asilbalaban/MKYADA/docs/images/1-2x2-wide.png

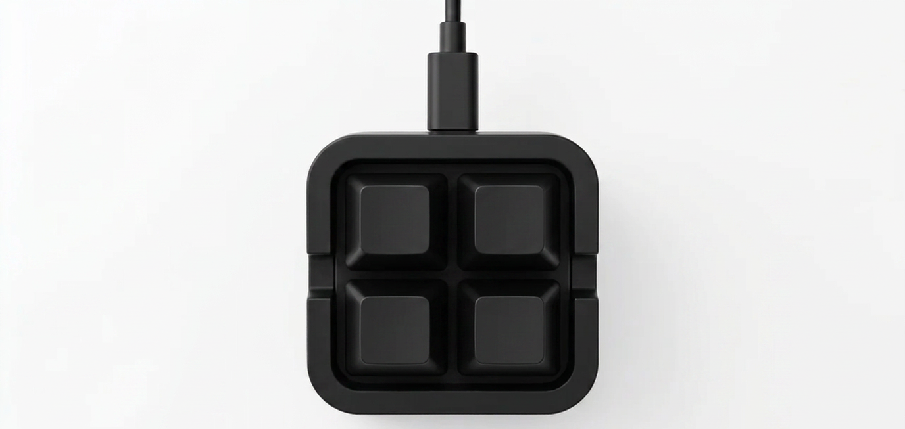
docs/images/1-2x2-wide.png
