asilbalaban/MKYADA/docs/images/2-3x2.png

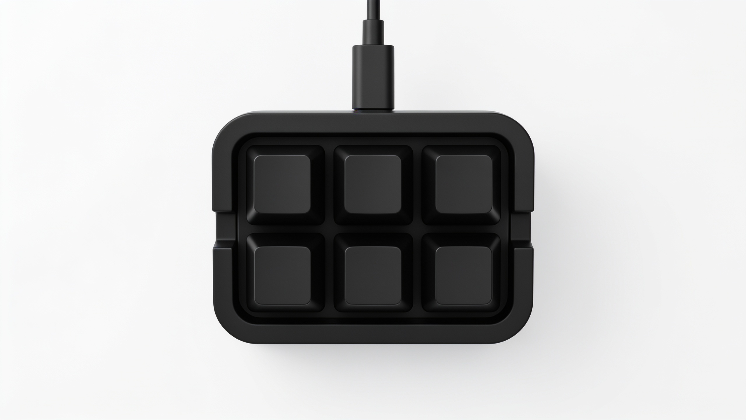
docs/images/2-3x2.png
