asilbalaban/MKYADA/docs/images/3-5x2-wide.png

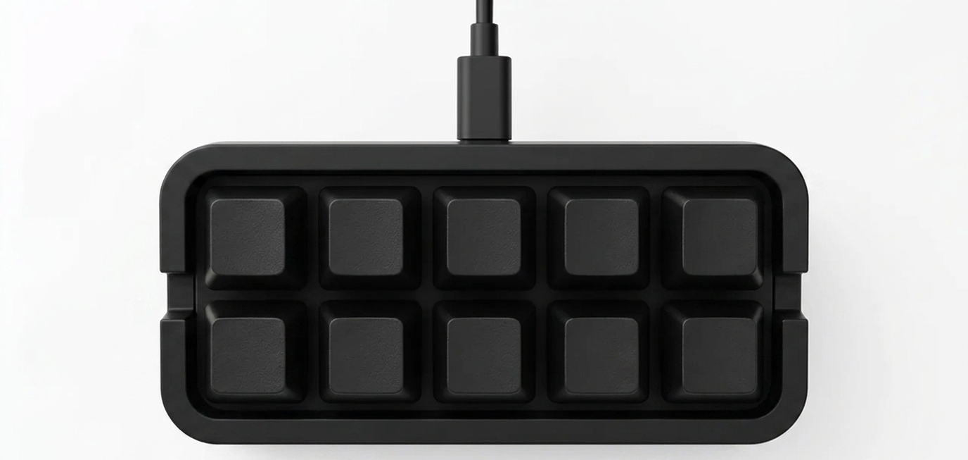
docs/images/3-5x2-wide.png
