asilbalaban/MKYADA/docs/images/3-5x2.png

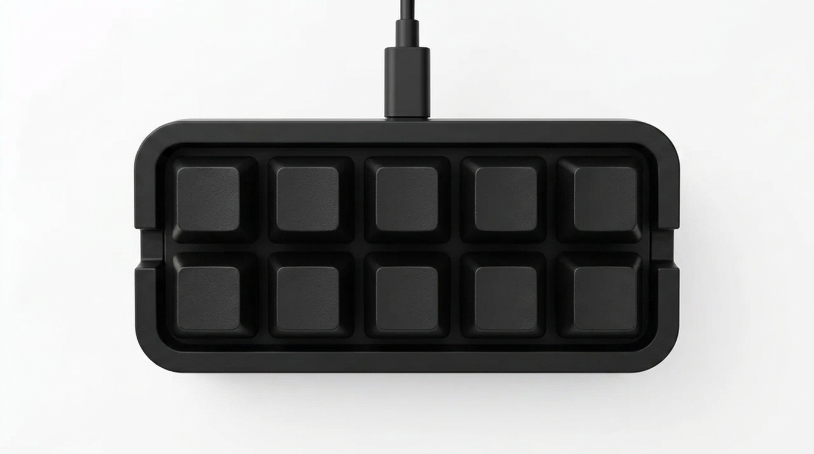
docs/images/3-5x2.png
