asilbalaban/MKYADA/docs/images/4-9x2.png

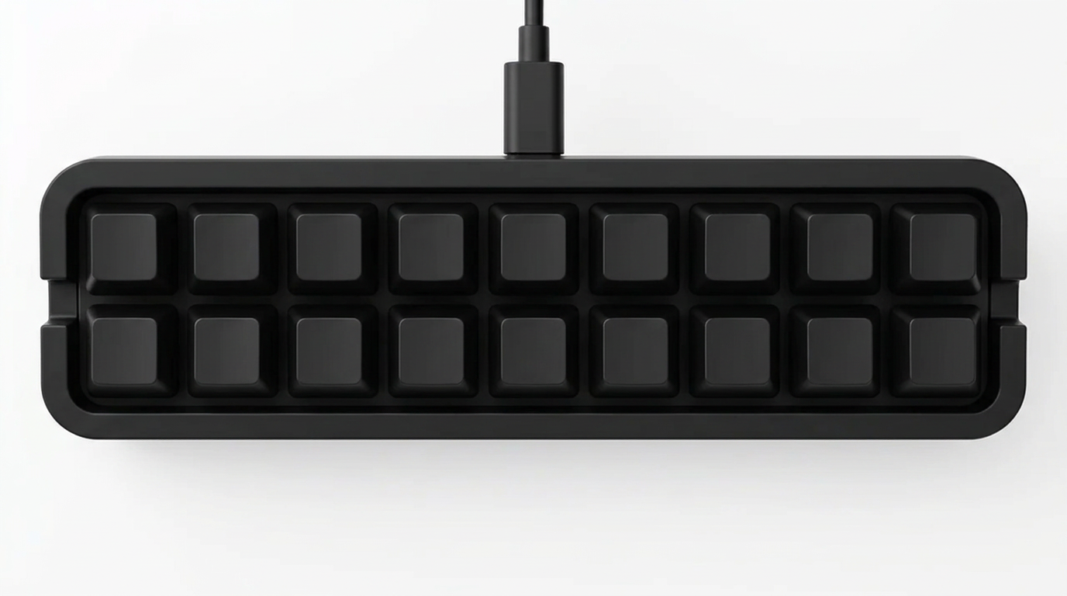
docs/images/4-9x2.png
