asilbalaban/MKYADA/docs/images/5-10x2.png

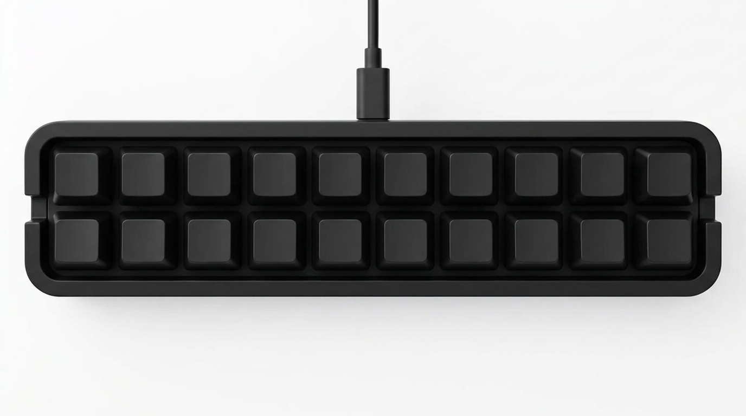
docs/images/5-10x2.png
