asilbalaban/MKYADA/docs/images/mkyada-backview-1800.jpg

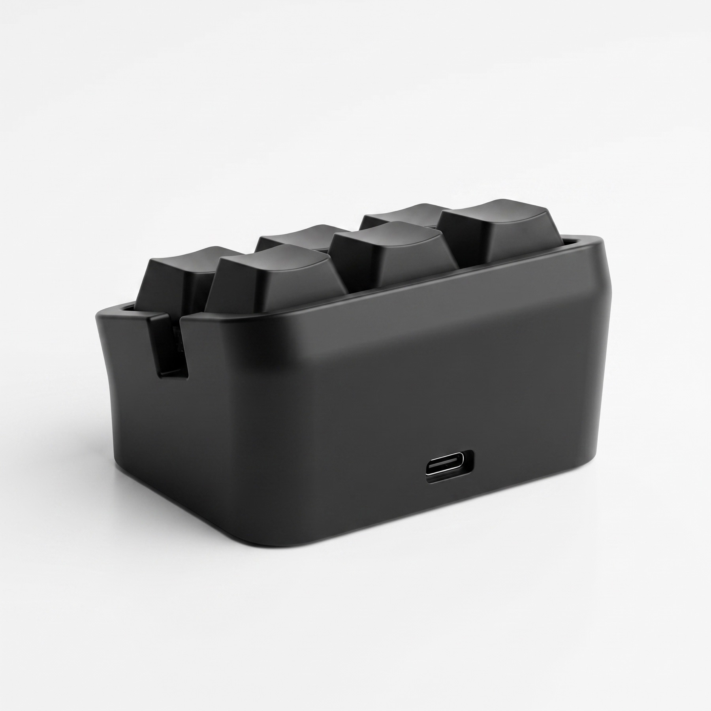
docs/images/mkyada-backview-1800.jpg
