asilbalaban/MKYADA/docs/images/mkyada-backview-cropped.png

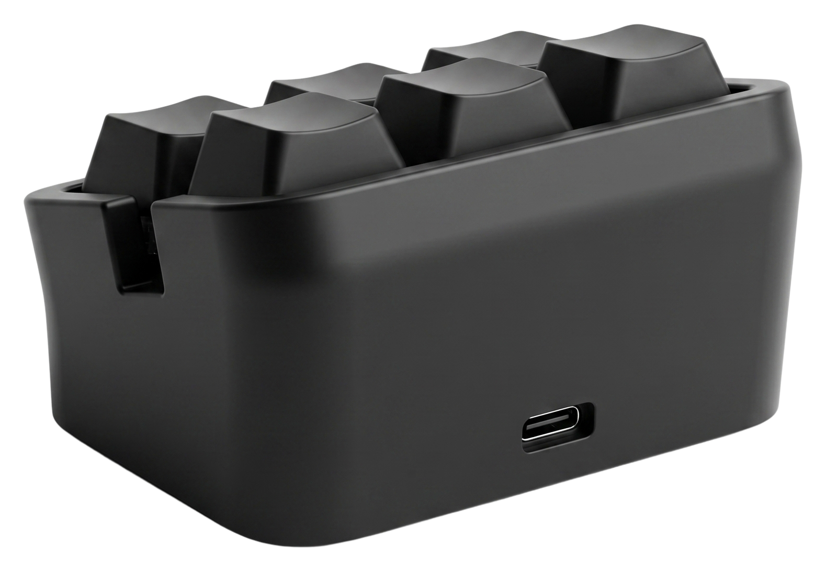
docs/images/mkyada-backview-cropped.png
