asilbalaban/MKYADA/docs/images/mkyada-backview-transparent.png

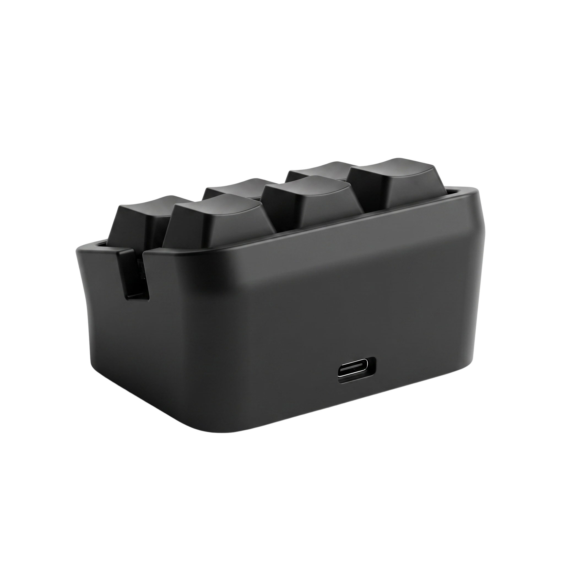
docs/images/mkyada-backview-transparent.png
