asilbalaban/MKYADA/docs/images/mkyada-topview-1800.jpg

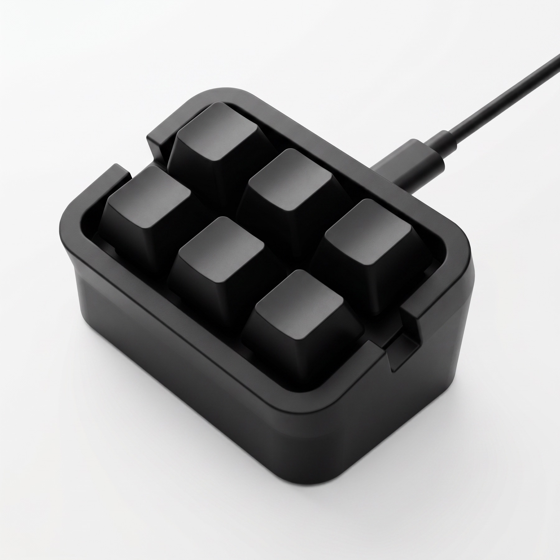
docs/images/mkyada-topview-1800.jpg
