asilbalaban/MKYADA/docs/images/mkyada-topview-cropped.png

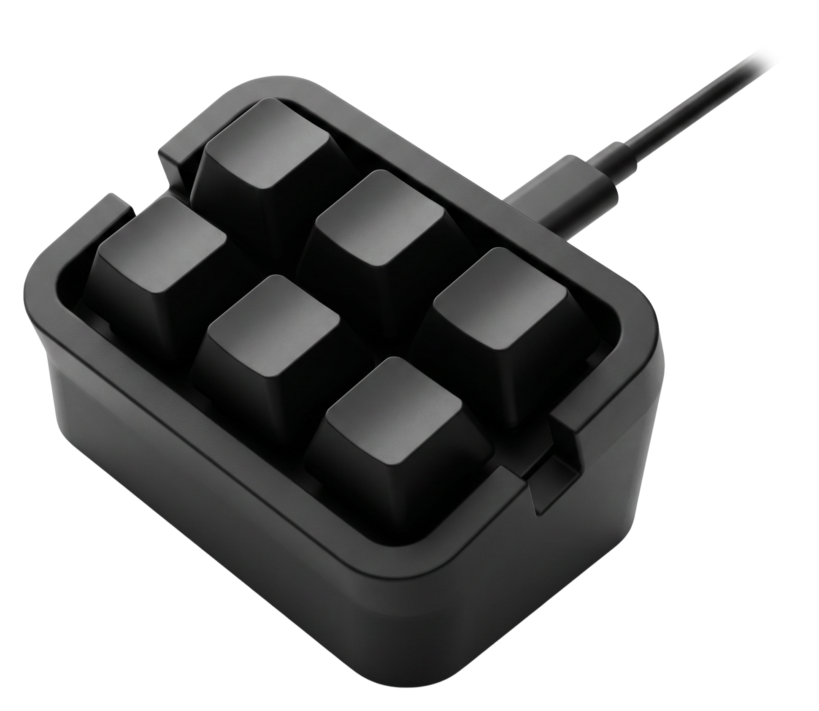
docs/images/mkyada-topview-cropped.png
