asilbalaban/MKYADA/docs/images/mkyada-topview-transparent.png

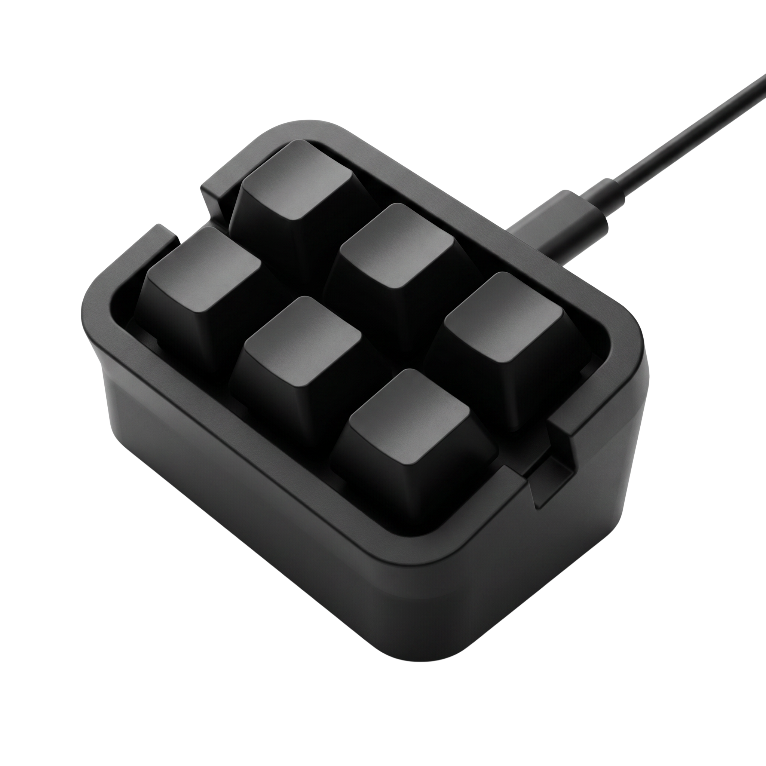
docs/images/mkyada-topview-transparent.png
