asilbalaban/MKYADA/docs/images/screens/core6-control-playing.png

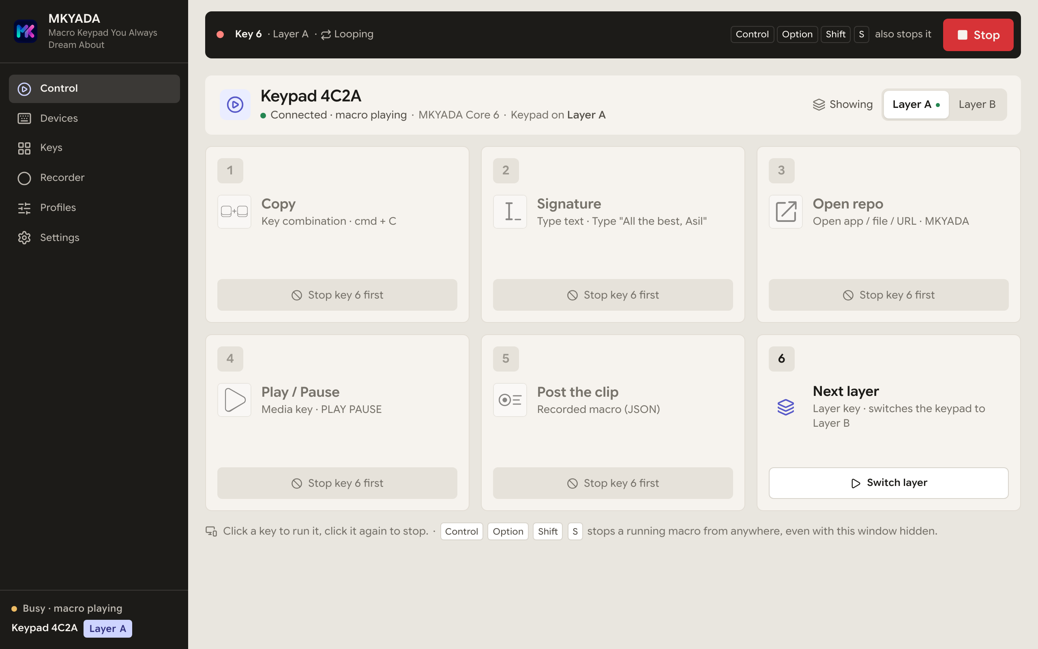
docs/images/screens/core6-control-playing.png
