asilbalaban/MKYADA/docs/images/screens/core6-control.png

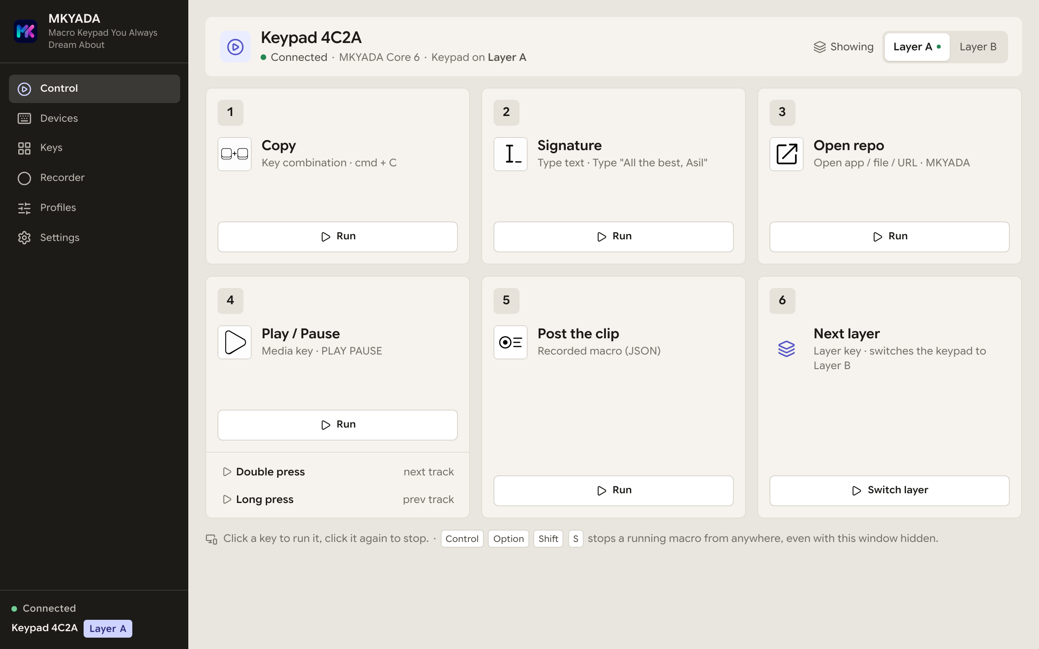
docs/images/screens/core6-control.png
