asilbalaban/MKYADA/docs/images/screens/core6-devices-others.png

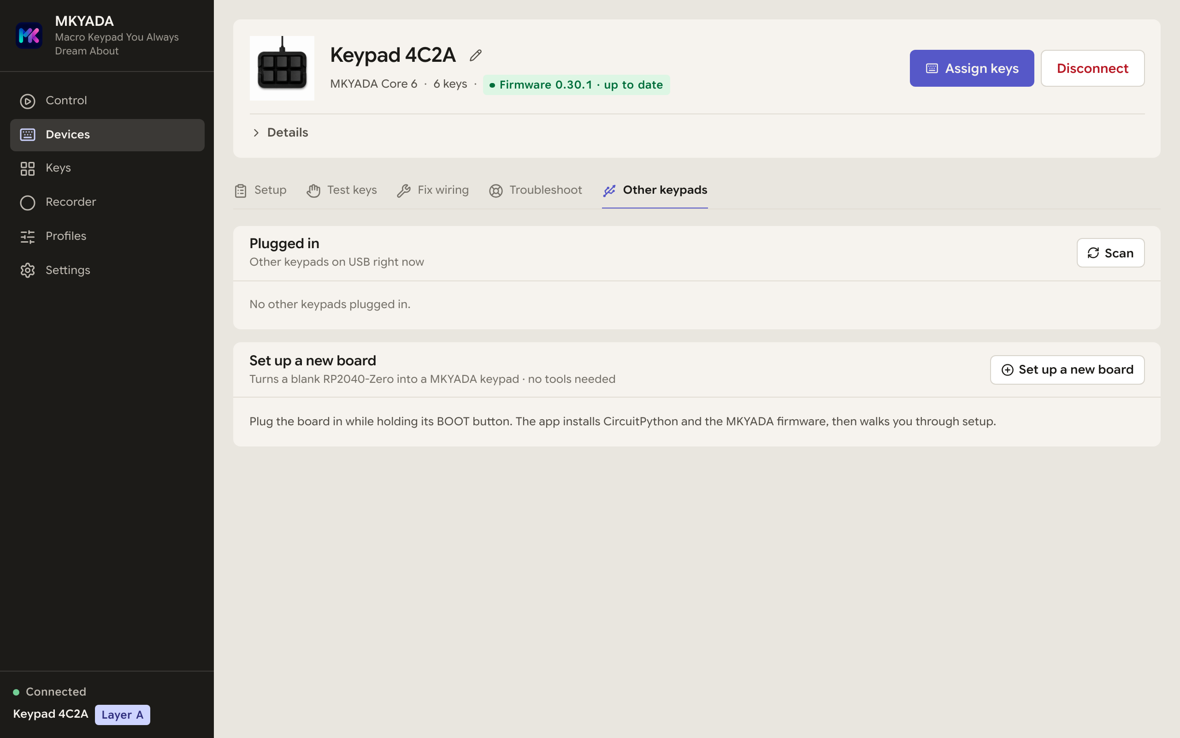
docs/images/screens/core6-devices-others.png
