asilbalaban/MKYADA/docs/images/screens/core6-settings-integrations.png

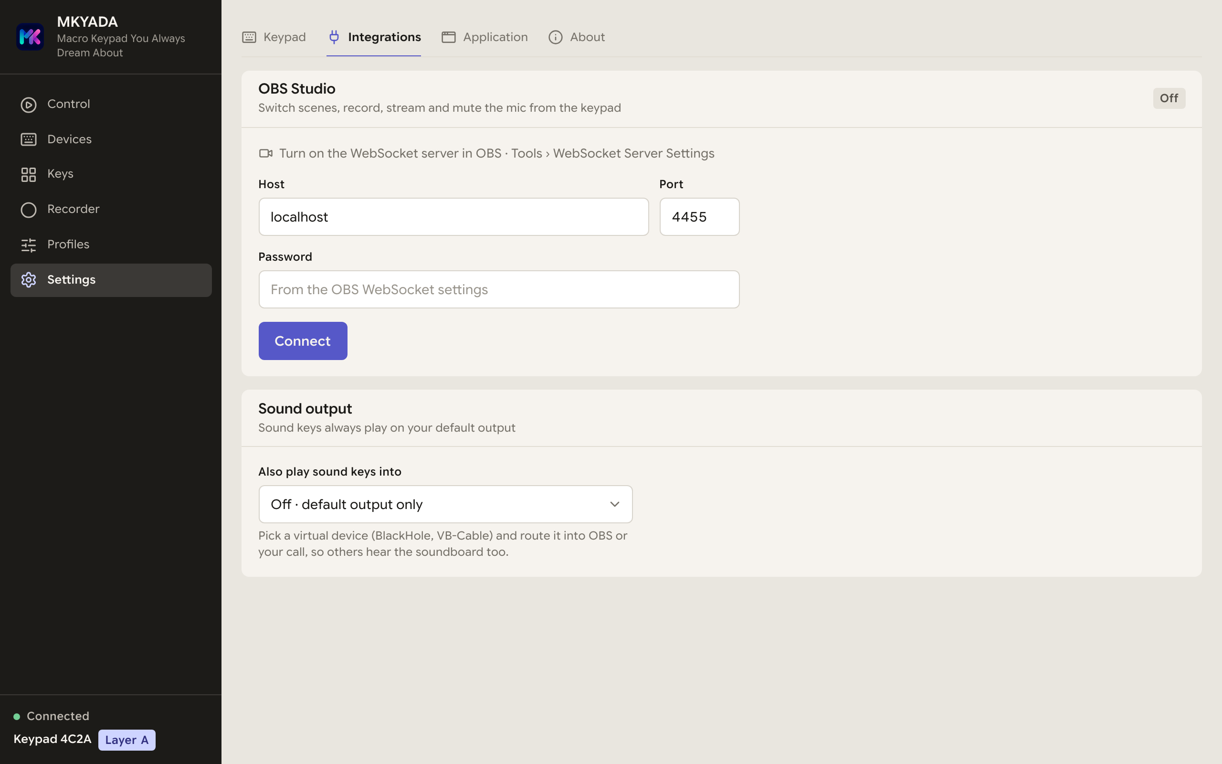
docs/images/screens/core6-settings-integrations.png
