asilbalaban/MKYADA/docs/images/screens/core6-settings.png

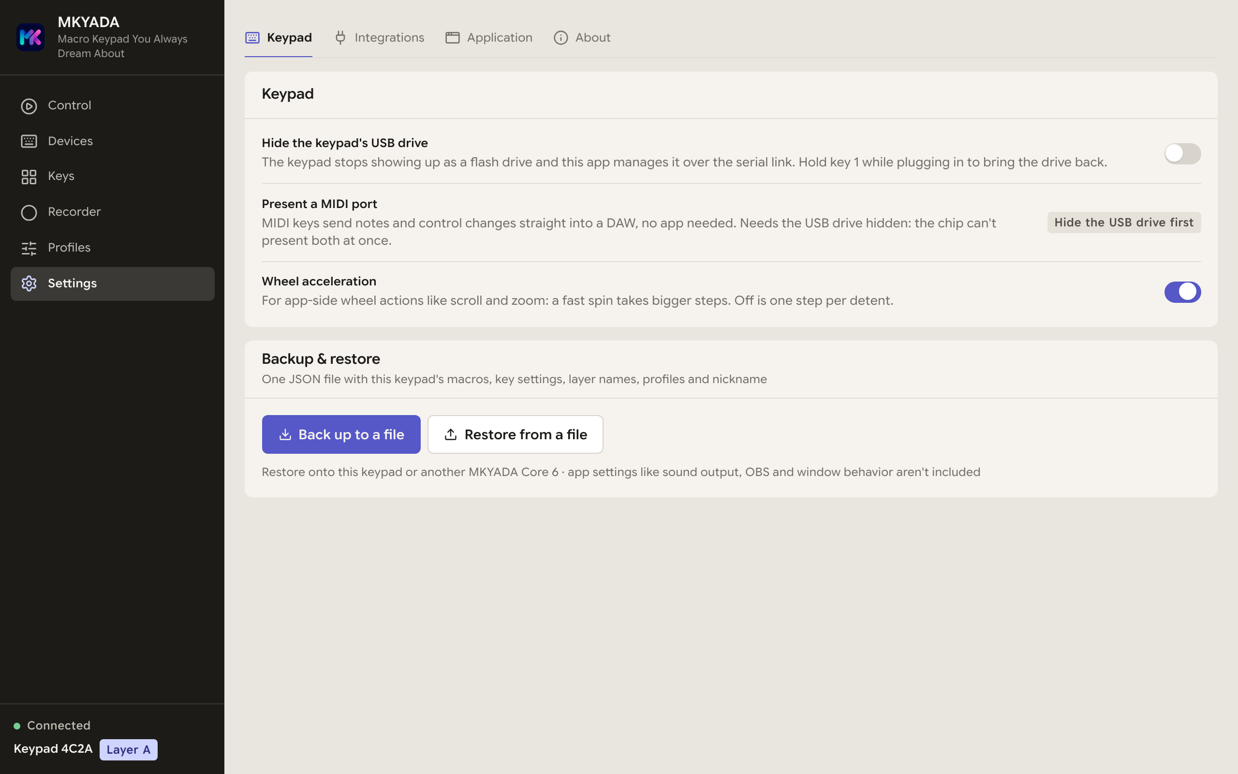
docs/images/screens/core6-settings.png
