asilbalaban/MKYADA/docs/images/screens/core6-wizard.png

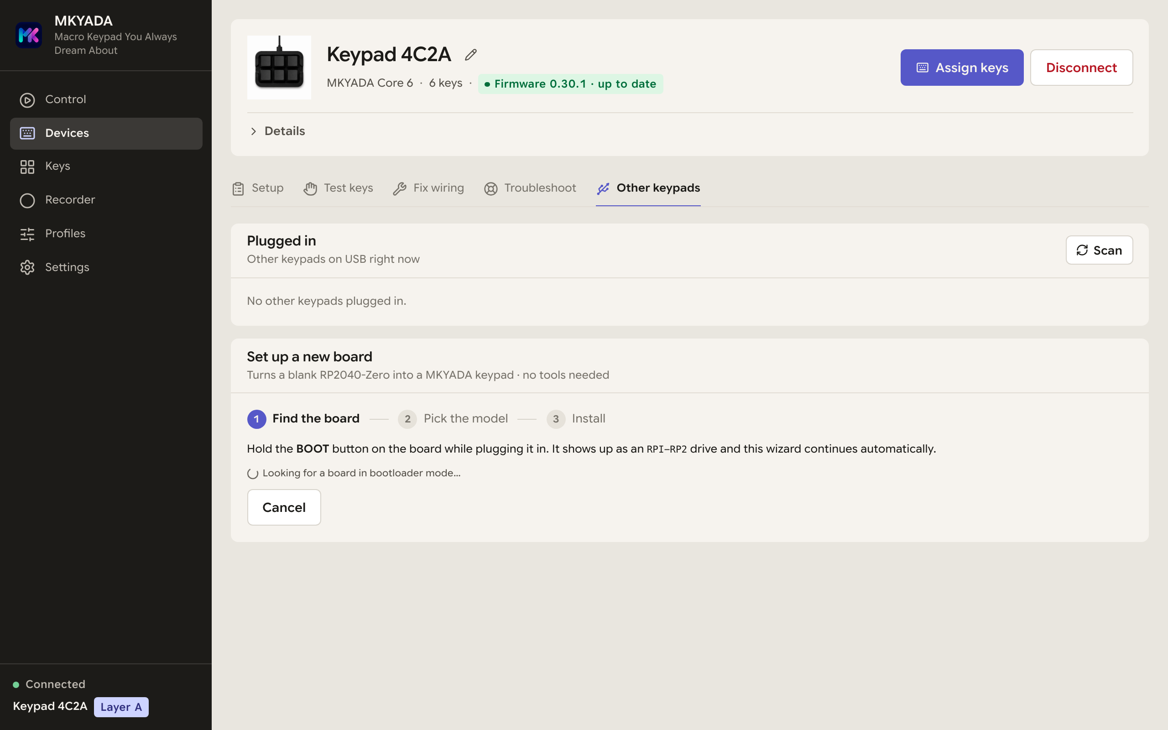
docs/images/screens/core6-wizard.png
