asilbalaban/MKYADA/docs/images/screens/core6-devices-wiring.png

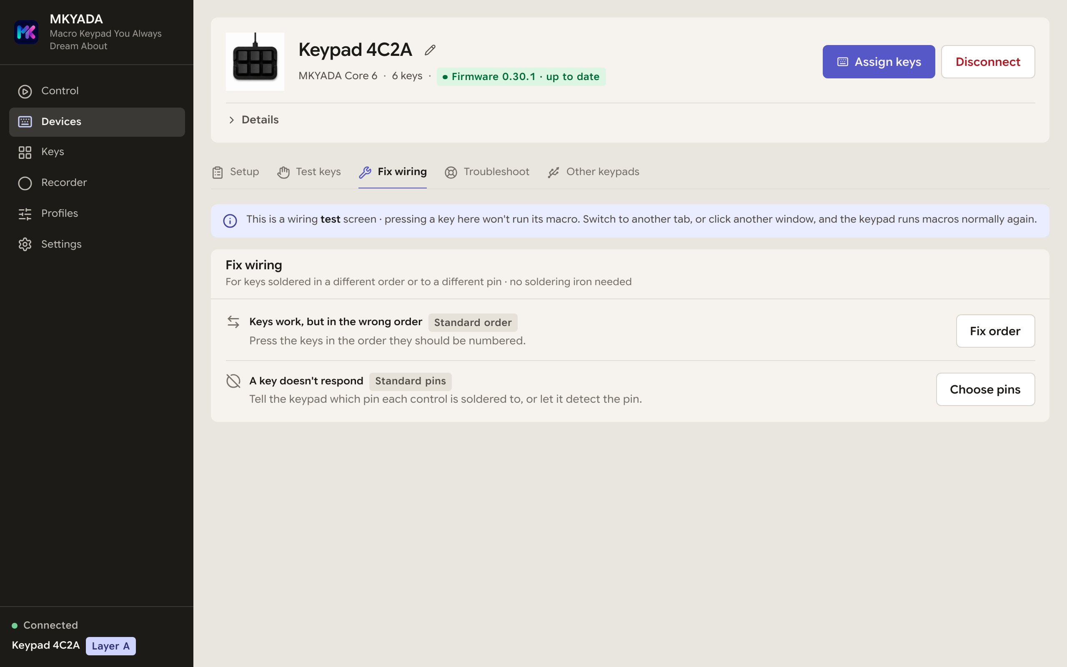
docs/images/screens/core6-devices-wiring.png
