asilbalaban/MKYADA/docs/images/screens/core6-devices-troubleshoot.png

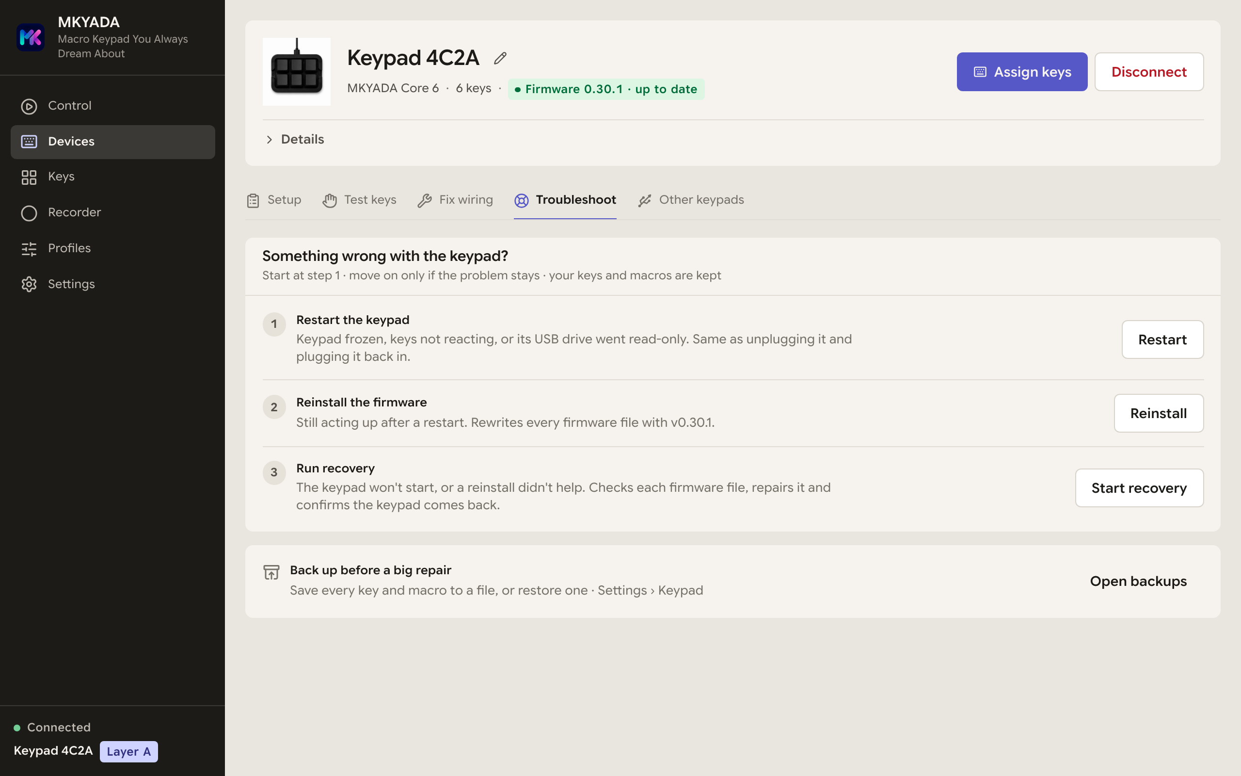
docs/images/screens/core6-devices-troubleshoot.png
