asilbalaban/MKYADA/firmware/mkyada/engine.py

# Macro playback engine: mkyada-macro JSON events -> USB HID reports.
# Port of the proven Raspberry Pi engine (pi/player.py); writes through
# usb_hid.devices instead of /dev/hidg*.

import struct
import time

import usb_hid

from mkyada.hidmap import CONSUMER_USAGE, resolve_key

try:
    from supervisor import ticks_ms
except ImportError:  # desktop simulation
    def ticks_ms():
        return int(time.monotonic() * 1000)

# supervisor.ticks_ms() wraps at 2**29; monotonic-float clocks lose ms
# precision after ~1h uptime, ticks don't.
_TICKS_PERIOD = 1 << 29
_TICKS_HALF = _TICKS_PERIOD // 2


def _ticks_diff(a, b):
    """a - b in ms, correct across the ticks_ms wrap."""
    return ((a - b + _TICKS_HALF) & (_TICKS_PERIOD - 1)) - _TICKS_HALF


def _find_device(usage_page, usage):
    for dev in usb_hid.devices:
        if dev.usage_page == usage_page and dev.usage == usage:
            return dev
    raise RuntimeError("HID device %02x:%02x not found" % (usage_page, usage))


class StopPlayback(Exception):
    pass


class Engine:
    """Owns the three HID interfaces and plays event streams through them."""

    POLL_MS = 20  # how often should_stop()/tick() run during playback

    def __init__(self):
        self.kbd = _find_device(0x01, 0x06)
        self.mouse = _find_device(0x01, 0x02)
        self.consumer = _find_device(0x0C, 0x01)
        self.mods = 0        # modifier byte
        self.keys = []       # pressed usages (max 6)
        self.buttons = 0     # mouse button byte (abs pointer, id 2)
        self.rel_buttons = 0  # mouse button byte (rel pointer, id 5)
        self.mx = 16384      # last absolute position (0..32767)
        self.my = 16384
        self.sw = 1919       # screen size - 1 for scaling
        self.sh = 1079
        self._last_poll = ticks_ms()
        self._midi_tried = False
        self._midi_port = None
        self._midi_notes = []  # (channel, note) sounding right now

    def set_screen(self, width, height):
        self.sw = max(1, int(width) - 1)
        self.sh = max(1, int(height) - 1)

    # --- keyboard ---
    def _kbd_report(self):
        ks = (self.keys + [0, 0, 0, 0, 0, 0])[:6]
        self.kbd.send_report(bytes([self.mods & 0xFF, 0] + ks))

    def key_down(self, ev):
        r = resolve_key(ev)
        if not r:
            return
        kind, val = r
        if kind == "mod":
            self.mods |= val
        elif val not in self.keys:
            if len(self.keys) < 6:
                self.keys.append(val)
        self._kbd_report()

    def key_up(self, ev):
        r = resolve_key(ev)
        if not r:
            return
        kind, val = r
        if kind == "mod":
            self.mods &= ~val & 0xFF
        elif val in self.keys:
            self.keys.remove(val)
        self._kbd_report()

    # --- mouse ---
    # Three reports on the mouse interface (boot.py ABS_MOUSE_DESCRIPTOR):
    # pointer (id 2) carries buttons + absolute X/Y, scroll (id 4) carries
    # the relative wheel/pan bytes ONLY, rel pointer (id 5) carries its own
    # button state + relative dX/dY. Absolute X/Y in a scroll report would
    # re-assert the last known position and teleport the cursor to wherever
    # the previous macro left it (screen center after boot); the rel report
    # exists so Dial drag slots can nudge the cursor from wherever the USER
    # left it. usb_hid rejects a wrong length, so these packs and boot.py's
    # in_report_lengths must stay in lockstep.
    def _mouse_report(self):
        self.mouse.send_report(struct.pack(
            "<BHH", self.buttons & 0x07, self.mx & 0x7FFF, self.my & 0x7FFF), 2)

    def _wheel_report(self, wheel=0, pan=0):
        self.mouse.send_report(struct.pack("<bb", wheel, pan), 4)

    def move(self, x, y):
        self.mx = max(0, min(32767, int(x * 32767 / self.sw)))
        self.my = max(0, min(32767, int(y * 32767 / self.sh)))
        self._mouse_report()

    def button(self, name, down, x=None, y=None):
        bit = {"left": 0x01, "right": 0x02, "middle": 0x04}.get(name, 0x01)
        if x is not None:
            self.move(x, y)
        if down:
            self.buttons |= bit
        else:
            self.buttons &= ~bit & 0xFF
        self._mouse_report()

    def _rel_report(self, dx=0, dy=0):
        self.mouse.send_report(struct.pack(
            "<Bbb", self.rel_buttons & 0x07,
            max(-127, min(127, int(dx))), max(-127, min(127, int(dy)))), 5)

    def rel_move(self, dx, dy):
        """Nudge the cursor relative to wherever it is now (report id 5).
        The id-2 abs state (mx/my) is deliberately untouched: abs macros
        keep replaying to their recorded positions regardless of nudges."""
        self._rel_report(dx, dy)

    def rel_button(self, name, down):
        bit = {"left": 0x01, "right": 0x02, "middle": 0x04}.get(name, 0x01)
        if down:
            self.rel_buttons |= bit
        else:
            self.rel_buttons &= ~bit & 0xFF
        self._rel_report()

    def hold_mods(self, mod_names):
        """Press modifier keys and KEEP them down (Dial move gestures:
        Ctrl+Opt+drag is Photoshop's brush-size scrub). Returns the modifier
        bits so the caller can drop_mods() exactly what it added."""
        from mkyada.hidmap import MOD_NAME
        added = 0
        for m in mod_names or ():
            added |= MOD_NAME.get(str(m).lower(), 0)
        if added:
            self.mods |= added
            self._kbd_report()
            time.sleep(0.01)  # let the host see the modifiers before the drag
        return added

    def drop_mods(self, bits):
        if bits:
            self.mods &= ~bits & 0xFF
            self._kbd_report()

    SCROLL_MAX_TICKS = 20  # per event/burst; matches the app's amount clamp

    def scroll(self, dy, dx=0):
        """Vertical (dy) and/or horizontal (dx) wheel ticks. Each unit is one
        detent-sized report, sent a few ms apart so hosts register every step
        (a single big report gets coalesced into one notch by some apps).
        The cursor never moves: scroll reports carry no X/Y."""
        vstep = 1 if dy > 0 else -1
        for _ in range(min(abs(int(dy)), self.SCROLL_MAX_TICKS)):
            self._wheel_report(wheel=vstep)
            time.sleep(0.008)
        hstep = 1 if dx > 0 else -1
        for _ in range(min(abs(int(dx)), self.SCROLL_MAX_TICKS)):
            self._wheel_report(pan=hstep)
            time.sleep(0.008)

    def wheel_burst(self, dy=0, dx=0, mod_names=None):
        """One serial-commanded scroll burst ({"t":"scroll"}, proto v6):
        optional modifiers held around the ticks (Ctrl+wheel = zoom). The
        app drives profile wheel slots through this — no file playback, so
        a spin feels like a real wheel, and it decides the acceleration."""
        from mkyada.hidmap import MOD_NAME
        added = 0
        for m in mod_names or ():
            added |= MOD_NAME.get(str(m).lower(), 0)
        if added:
            self.mods |= added
            self._kbd_report()
            time.sleep(0.01)  # let the host see the modifier before the ticks
        try:
            self.scroll(int(dy or 0), int(dx or 0))
        finally:
            if added:
                self.mods &= ~added & 0xFF
                self._kbd_report()

    # --- consumer (media keys) ---
    def consumer_tap(self, usage_name):
        usage = CONSUMER_USAGE.get(usage_name)
        if usage is None:
            return
        self.consumer.send_report(struct.pack("<H", usage))
        time.sleep(0.02)
        self.consumer.send_report(struct.pack("<H", 0))

    # --- MIDI ---
    # Lazy and optional, unlike the HID interfaces: usb_midi may be off at
    # boot (config "midi": false, or boot.py's endpoint budget refused it)
    # and the desktop simulator has no such module at all. A missing port is
    # a silent no-op — _find_device's RuntimeError would be wrong here.
    def _midi(self):
        if not self._midi_tried:
            self._midi_tried = True
            try:
                import usb_midi
                self._midi_port = usb_midi.ports[1]
            except (ImportError, IndexError, AttributeError):
                self._midi_port = None
        return self._midi_port

    def midi_send(self, msg, ch=0, d1=0, d2=0):
        """One MIDI message out. `msg` is note_on / note_off / cc / pc;
        d1 and d2 are note+velocity, controller+value, or program (d2
        unused). Held notes are tracked so release_all can silence them."""
        port = self._midi()
        if port is None:
            return
        ch = int(ch) & 0x0F
        d1 = int(d1) & 0x7F
        d2 = int(d2) & 0x7F
        if msg == "note_on":
            port.write(bytes([0x90 | ch, d1, d2]))
            if (ch, d1) not in self._midi_notes:
                self._midi_notes.append((ch, d1))
        elif msg == "note_off":
            port.write(bytes([0x80 | ch, d1, 0]))
            if (ch, d1) in self._midi_notes:
                self._midi_notes.remove((ch, d1))
        elif msg == "cc":
            port.write(bytes([0xB0 | ch, d1, d2]))
        elif msg == "pc":
            port.write(bytes([0xC0 | ch, d1]))

    def release_all(self):
        self.mods = 0
        self.keys = []
        self._kbd_report()
        # A macro stopped mid-note must not leave the DAW sounding — the
        # same contract as the key-up above, and the reason a note_on is
        # tracked at all.
        if self._midi_notes:
            held, self._midi_notes = self._midi_notes, []
            port = self._midi()
            if port is not None:
                for ch, note in held:
                    port.write(bytes([0x80 | ch, note, 0]))
        # Only touch the mouse when there is a button to release: the pointer
        # report is absolute, so sending it "just in case" teleports the
        # cursor to the last macro position (screen center after boot) even
        # for keyboard-only macros.
        if self.buttons:
            self.buttons = 0
            self._mouse_report()
        # Same rule for the rel pointer: only report when a drag is actually
        # held, and a zero-delta release leaves the cursor where it is.
        if self.rel_buttons:
            self.rel_buttons = 0
            self._rel_report()

    # --- direct combo (serial "keys" command / tiny bindings) ---
    def tap_combo(self, mod_names, key_label, hold_ms=30):
        from mkyada.hidmap import MOD_NAME
        for m in mod_names or ():
            self.mods |= MOD_NAME.get(str(m).lower(), 0)
        self._kbd_report()
        self.key_down({"key": key_label})
        time.sleep(hold_ms / 1000)
        self.key_up({"key": key_label})
        self.mods = 0
        self._kbd_report()

    # --- playback ---
    def _poll(self, should_stop, tick):
        self._last_poll = ticks_ms()
        if should_stop and should_stop():
            raise StopPlayback()
        if tick:
            tick()

    def _wait_until(self, start, due_ms, should_stop, tick):
        """Wait until `due_ms` after `start` (absolute deadline, so per-event
        overhead is absorbed instead of accumulating across the macro)."""
        while True:
            now = ticks_ms()
            if _ticks_diff(now, self._last_poll) >= self.POLL_MS:
                self._poll(should_stop, tick)
                now = ticks_ms()
            remaining = due_ms - _ticks_diff(now, start)
            if remaining <= 0:
                return
            # short slices keep the deadline sharp; host HID polling
            # quantizes to >=1ms anyway, so no busy-spin needed
            time.sleep(0.004 if remaining > 4 else remaining / 1000.0)

    def play(self, events, screen=None, speed=1.0, should_stop=None, tick=None):
        """Play one pass over an iterable of events. Raises StopPlayback on abort."""
        if screen:
            self.set_screen(screen.get("width", 1920), screen.get("height", 1080))
        speed = max(0.01, speed)
        self.release_all()
        start = ticks_ms()
        due = 0.0  # ms since start; float so speed scaling stays exact
        try:
            # poll once per pass so even an all-zero-delay macro (where no
            # wait ever goes stale) still honors stop/restart/switch presses
            self._poll(should_stop, tick)
            for ev in events:
                due += ev.get("delay", 0) / speed
                self._wait_until(start, due, should_stop, tick)
                t = ev.get("type")
                if t == "key":
                    (self.key_down if ev.get("action") == "down" else self.key_up)(ev)
                elif t == "move":
                    self.move(ev.get("x", 0), ev.get("y", 0))
                elif t == "button":
                    self.button(ev.get("button", "left"), ev.get("action") == "down",
                                ev.get("x"), ev.get("y"))
                elif t == "scroll":
                    self.scroll(ev.get("dy", 0), ev.get("dx", 0))
                elif t == "consumer":
                    self.consumer_tap(ev.get("usage", ""))
                elif t == "midi":
                    self.midi_send(ev.get("m", ""), ev.get("ch", 0),
                                   ev.get("d1", 0), ev.get("d2", 0))
                # "wait" and unknown types: delay already applied above
        finally:
            self.release_all()
