asilbalaban/MKYADA/firmware/mkyada/led.py

# Status LED on the RP2040-Zero's onboard WS2812 (GP16).
#
#   idle        layer color, dim solid (A green / B blue / C purple / D teal)
#   playing     amber fast blink; looping macro -> slow amber blink
#   host mode   layer color breathing toward white
#   error       red triple-blink overlay, then back to current state
#   override    app-commanded feedback color (serial "led" op, e.g. mic muted
#               -> solid red). Shown when idle/host; playback blinks win.
#               Cleared when the app disconnects, so the standalone LED
#               grammar is untouched without a host.

import time

import board

try:
    import neopixel
except ImportError:
    neopixel = None  # lib missing: run without a status LED

# A-D unchanged from the original 4-layer palette; E-H added for the
# 8-layer cap (amber is reserved for "playing", red for errors).
LAYER_COLORS = ((0, 255, 0), (0, 80, 255), (170, 0, 255), (0, 255, 180),
                (255, 255, 255), (255, 0, 150), (160, 255, 0), (255, 200, 0))
AMBER = (255, 120, 0)
RED = (255, 0, 0)

IDLE, PLAYING, LOOPING, HOST = 0, 1, 2, 3


class Led:
    def __init__(self):
        try:
            self.px = neopixel.NeoPixel(board.GP16, 1, brightness=0.15, auto_write=True) if neopixel else None
        except Exception:
            self.px = None
        self.state = IDLE
        self.layer = 0
        self.error_until = 0
        self.override = None  # ("solid"|"blink", (r, g, b)) from the app
        self._apply()

    def _color(self):
        return LAYER_COLORS[self.layer % len(LAYER_COLORS)]

    def _apply(self, color=None):
        if self.px:
            try:
                self.px[0] = color or self._color()
            except Exception:
                pass

    def set(self, state=None, layer=None):
        if state is not None:
            self.state = state
        if layer is not None:
            self.layer = layer
        self._apply(AMBER if self.state in (PLAYING, LOOPING) else None)

    def error(self):
        self.error_until = time.monotonic() + 1.2

    def set_override(self, mode, rgb):
        """App-commanded feedback color; mode "off" clears it."""
        if mode not in ("solid", "blink") or not rgb:
            self.override = None
        else:
            try:
                self.override = (mode, (int(rgb[0]), int(rgb[1]), int(rgb[2])))
            except (TypeError, ValueError, IndexError):
                self.override = None
        self._apply()

    def clear_override(self):
        self.override = None
        self._apply()

    def tick(self):
        """Animate; call every main-loop iteration."""
        if not self.px:
            return
        now = time.monotonic()
        if now < self.error_until:                       # red triple-blink overlay
            self._apply(RED if int(now * 5) % 2 == 0 else (0, 0, 0))
            return
        if self.state == LOOPING:                        # slow amber blink
            self._apply(AMBER if int(now * 2) % 2 == 0 else (0, 0, 0))
        elif self.state == PLAYING:                      # fast amber blink
            self._apply(AMBER if int(now * 4) % 2 == 0 else (0, 0, 0))
        elif self.override:                              # app feedback color
            mode, rgb = self.override
            if mode == "blink":
                self._apply(rgb if int(now * 2) % 2 == 0 else (0, 0, 0))
            else:
                self._apply(rgb)
        elif self.state == HOST:                         # breathe layer color -> white
            phase = (now % 2.0) / 2.0
            level = phase * 2 if phase < 0.5 else (1 - phase) * 2
            r, g, b = self._color()
            self._apply((int(r + (255 - r) * level * 0.6),
                         int(g + (255 - g) * level * 0.6),
                         int(b + (255 - b) * level * 0.6)))
        else:
            self._apply()
