asilbalaban/MKYADA/tests/firmware_sim_test.py

"""Desktop simulation of the MKYADA firmware: stubs CircuitPython modules,
then exercises engine playback, config loading, layer logic and the serial
protocol handler. Run: python3 tests/firmware_sim_test.py"""
import json
import os
import sys
import types

REPO = os.path.dirname(os.path.dirname(os.path.abspath(__file__)))
FFW = os.path.join(REPO, "firmware")

# ---------- CircuitPython stubs ----------
sent_reports = []


class FakeHidDevice:
    def __init__(self, usage_page, usage):
        self.usage_page, self.usage = usage_page, usage

    def send_report(self, buf, report_id=None):
        # mouse is a two-report device (pointer id 2 / scroll id 4); the
        # tests tell them apart by length, matching boot.py's lengths
        sent_reports.append((self.usage_page, self.usage, bytes(buf)))


usb_hid = types.ModuleType("usb_hid")
usb_hid.devices = [FakeHidDevice(0x01, 0x06), FakeHidDevice(0x01, 0x02),
                   FakeHidDevice(0x0C, 0x01)]
sys.modules["usb_hid"] = usb_hid

sent_midi = []


class FakeMidiPort:
    def write(self, buf):
        sent_midi.append(bytes(buf))


# ports[0] is in (host->device), ports[1] is out — engine.py only writes.
usb_midi = types.ModuleType("usb_midi")
usb_midi.ports = [None, FakeMidiPort()]
sys.modules["usb_midi"] = usb_midi

usb_cdc = types.ModuleType("usb_cdc")
usb_cdc.data = None
sys.modules["usb_cdc"] = usb_cdc

board = types.ModuleType("board")
for i in list(range(16)) + [16] + list(range(26, 30)):
    setattr(board, "GP%d" % i, "GP%d" % i)
sys.modules["board"] = board


class FakeDigitalInOut:
    def __init__(self, pin):
        self.pin = pin
        self.direction = None
        self.pull = None
        self.value = True  # not pressed (pull-up)


digitalio = types.ModuleType("digitalio")
digitalio.DigitalInOut = FakeDigitalInOut
digitalio.Direction = types.SimpleNamespace(INPUT="in")
digitalio.Pull = types.SimpleNamespace(UP="up")
sys.modules["digitalio"] = digitalio

class _ResetCalled(SystemExit):
    pass


microcontroller = types.ModuleType("microcontroller")
microcontroller.cpu = types.SimpleNamespace(uid=bytes(range(8)))
microcontroller.reset = lambda: (_ for _ in ()).throw(_ResetCalled())
microcontroller.RunMode = types.SimpleNamespace(UF2="uf2", BOOTLOADER="btl")
microcontroller.next_reset_to = []
microcontroller.on_next_reset = lambda mode: microcontroller.next_reset_to.append(mode)
sys.modules["microcontroller"] = microcontroller


class FakeNeoPixel(list):
    def __init__(self, pin, n, brightness=1.0, auto_write=True):
        super().__init__([(0, 0, 0)] * n)


neopixel = types.ModuleType("neopixel")
neopixel.NeoPixel = FakeNeoPixel
sys.modules["neopixel"] = neopixel

# --- display / encoder stubs (vision6 UI). busio, i2cdisplaybus and
# adafruit_displayio_sh1106 are deliberately NOT stubbed: Oled.__init__ then
# fails its retries and runs headless, which is exactly the code path a
# desktop test can exercise.


# displayio and bitmaptools are software implementations with real pixel
# semantics (tests/fakedisplayio.py), shared with tests/oled_render_test.py
# which renders the screens and diffs them against golden pictures.
sys.path.insert(0, os.path.join(REPO, "tests"))
import fakedisplayio  # noqa: E402

fakedisplayio.install()

rotaryio = types.ModuleType("rotaryio")


class FakeEncoder:
    def __init__(self, a, b):
        self.position = 0


rotaryio.IncrementalEncoder = FakeEncoder
sys.modules["rotaryio"] = rotaryio

keypad = types.ModuleType("keypad")


class FakeKeyEvent:
    def __init__(self, key_number, pressed):
        self.key_number, self.pressed = key_number, pressed


class FakeEventQueue:
    def __init__(self):
        self.queue = []

    def get(self):
        return self.queue.pop(0) if self.queue else None


class FakeKeys:
    def __init__(self, pins, value_when_pressed=False, pull=True):
        self.pins = pins
        self.events = FakeEventQueue()


keypad.Keys = FakeKeys
keypad.Event = FakeKeyEvent
sys.modules["keypad"] = keypad

sys.path.insert(0, FFW)

# ---------- tests ----------
failures = []


def check(name, cond, detail=""):
    print(("PASS" if cond else "FAIL"), name, detail if not cond else "")
    if not cond:
        failures.append(name)


# 1. hidmap resolution
from mkyada.hidmap import resolve_key  # noqa: E402

check("vk letter A", resolve_key({"vk": 65}) == ("key", 0x04))
check("mod ctrl_l by name", resolve_key({"key": "ctrl_l"}) == ("mod", 0x01))
check("char fallback 'a'", resolve_key({"key": "a"}) == ("key", 0x04))
check("f5 by name", resolve_key({"key": "f5"}) == ("key", 0x3E))
check("unknown -> None", resolve_key({"key": "☃"}) is None)

# 2. engine playback of the demo macro
from mkyada.engine import Engine, StopPlayback  # noqa: E402

eng = Engine()
with open(os.path.join(FFW, "macros", "key1.json")) as f:
    demo = json.load(f)
for ev in demo["events"]:
    ev["delay"] = min(ev["delay"], 1)  # speed the test up
eng.play(demo["events"], screen={"width": 1920, "height": 1080})
kbd = [r for r in sent_reports if r[1] == 0x06]
check("kbd reports emitted", len(kbd) > 12, str(len(kbd)))
check("report is 8 bytes", all(len(r[2]) == 8 for r in kbd))
check("'m' pressed", any(r[2][2] == 0x10 for r in kbd))
check("ends released", kbd[-1][2] == bytes(8))

# mouse + consumer
import struct  # noqa: E402

sent_reports.clear()
eng.play([{"delay": 0, "type": "move", "x": 960, "y": 540},
          {"delay": 0, "type": "button", "action": "down", "button": "left"},
          {"delay": 0, "type": "button", "action": "up", "button": "left"},
          {"delay": 0, "type": "consumer", "usage": "volume_up"}],
         screen={"width": 1920, "height": 1080})
mouse = [r for r in sent_reports if r[1] == 0x02]
cons = [r for r in sent_reports if r[0] == 0x0C]
# pointer report is buttons + X + Y (5 bytes, report id 2; boot.py descriptor)
check("mouse pointer report is 5 bytes", all(len(r[2]) == 5 for r in mouse), str(mouse[:1]))
xy = struct.unpack("<BHH", mouse[0][2]) if mouse else None
check("abs move scaled", xy and abs(xy[1] - 16383) < 40 and abs(xy[2] - 16391) < 60, str(xy))
check("left click down bit", any(r[2][0] & 0x01 for r in mouse))
check("consumer volume_up", any(struct.unpack('<H', r[2])[0] == 0xE9 for r in cons), str(cons))

# scroll: its own 2-byte report (wheel + pan) so the cursor never moves
sent_reports.clear()
eng.play([{"delay": 0, "type": "scroll", "dy": 3}], screen=None)
wheel = [struct.unpack("<bb", r[2]) for r in sent_reports
         if r[1] == 0x02 and len(r[2]) == 2]
check("vertical scroll wheel +1 steps", sum(1 for m in wheel if m[0] == 1) == 3, str(wheel))
check("vertical scroll no pan", all(m[1] == 0 for m in wheel), str(wheel))
check("scroll sends no pointer report",
      not any(r[1] == 0x02 and len(r[2]) == 5 for r in sent_reports),
      str(sent_reports))

# --- MIDI (proto v16) ---
sent_midi.clear()
sent_reports.clear()
eng.play([{"delay": 0, "type": "midi", "m": "note_on", "ch": 0, "d1": 60, "d2": 100},
          {"delay": 0, "type": "midi", "m": "note_off", "ch": 0, "d1": 60}],
         screen=None)
check("note on/off bytes", sent_midi[:2] == [b"\x90\x3c\x64", b"\x80\x3c\x00"],
      str(sent_midi))
# release_all's empty keyboard report bookends every macro; what must NOT
# happen is a mouse or consumer report, which would move the cursor or fire a
# media key alongside the note
check("midi touches no mouse or consumer device",
      all(r[0] == 0x01 and r[1] == 0x06 for r in sent_reports), str(sent_reports))

sent_midi.clear()
eng.play([{"delay": 0, "type": "midi", "m": "cc", "ch": 2, "d1": 74, "d2": 64},
          {"delay": 0, "type": "midi", "m": "pc", "ch": 15, "d1": 5}], screen=None)
check("cc carries its channel", sent_midi[0] == b"\xb2\x4a\x40", str(sent_midi))
check("pc is two bytes", sent_midi[1] == b"\xcf\x05", str(sent_midi))

# out-of-range values are masked, never sent raw (a 7-bit field with the top
# bit set would read as a status byte and desync the DAW's parser)
sent_midi.clear()
eng.midi_send("note_on", 99, 200, 300)
check("midi values masked to 7 bits",
      sent_midi == [b"\x93\x48\x2c"], str(sent_midi))

# a macro that ends mid-note must not leave the DAW sounding
sent_midi.clear()
eng.play([{"delay": 0, "type": "midi", "m": "note_on", "ch": 1, "d1": 64, "d2": 100}],
         screen=None)
check("hanging note silenced by release_all", sent_midi[-1] == b"\x81\x40\x00",
      str(sent_midi))
check("no note left tracked", eng._midi_notes == [], str(eng._midi_notes))

sent_reports.clear()
eng.play([{"delay": 0, "type": "scroll", "dy": 0, "dx": -2}], screen=None)
hwheel = [struct.unpack("<bb", r[2]) for r in sent_reports
          if r[1] == 0x02 and len(r[2]) == 2]
check("horizontal scroll pan -1 steps", sum(1 for m in hwheel if m[1] == -1) == 2, str(hwheel))
check("horizontal scroll no wheel", all(m[0] == 0 for m in hwheel), str(hwheel))

# keyboard-only macros must not touch the mouse at all — the pointer report
# is absolute, so a stray one teleports the cursor (the old release_all bug)
sent_reports.clear()
eng.play([{"delay": 0, "type": "key", "action": "down", "key": "a"},
          {"delay": 0, "type": "key", "action": "up", "key": "a"}], screen=None)
check("kbd-only macro sends no mouse report",
      not any(r[1] == 0x02 for r in sent_reports), str(sent_reports))

# wheel_burst (serial "scroll", proto v6): modifiers held around the ticks
sent_reports.clear()
eng.wheel_burst(2, 0, ["ctrl"])
burst_kbd = [r[2] for r in sent_reports if r[1] == 0x06]
burst_wheel = [struct.unpack("<bb", r[2]) for r in sent_reports
               if r[1] == 0x02 and len(r[2]) == 2]
check("wheel_burst holds ctrl", burst_kbd and burst_kbd[0][0] == 0x01, str(burst_kbd))
check("wheel_burst releases ctrl", burst_kbd[-1][0] == 0x00, str(burst_kbd))
check("wheel_burst ticks", [m[0] for m in burst_wheel] == [1, 1], str(burst_wheel))

# rel pointer (id 5, 3 bytes): Dial drag slots nudge from the user's position
sent_reports.clear()
eng.rel_move(30, -4)
rel = [struct.unpack("<Bbb", r[2]) for r in sent_reports
       if r[1] == 0x02 and len(r[2]) == 3]
check("rel move dx/dy", rel == [(0, 30, -4)], str(rel))
check("rel move sends no abs pointer",
      not any(r[1] == 0x02 and len(r[2]) == 5 for r in sent_reports),
      str(sent_reports))

sent_reports.clear()
eng.rel_move(500, -500)
rel = [struct.unpack("<Bbb", r[2]) for r in sent_reports
       if r[1] == 0x02 and len(r[2]) == 3]
check("rel move clamps to +/-127", rel == [(0, 127, -127)], str(rel))

sent_reports.clear()
eng.rel_button("left", True)
eng.rel_move(5, 0)
eng.release_all()
rel = [struct.unpack("<Bbb", r[2]) for r in sent_reports
       if r[1] == 0x02 and len(r[2]) == 3]
check("rel drag press/move/release", rel == [(1, 0, 0), (1, 5, 0), (0, 0, 0)],
      str(rel))
check("release_all clears rel buttons", eng.rel_buttons == 0)

sent_reports.clear()
eng.release_all()
check("release_all quiet without rel drag",
      not any(r[1] == 0x02 and len(r[2]) == 3 for r in sent_reports),
      str(sent_reports))

# stop mid-play
calls = {"n": 0}


def stopper():
    calls["n"] += 1
    return calls["n"] > 2


try:
    eng.play([{"delay": 5, "type": "wait"}] * 100, should_stop=stopper)
    check("StopPlayback raised", False)
except StopPlayback:
    check("StopPlayback raised", True)

# drift-free scheduling: 100 x 10ms events with a 2ms-slow tick must finish in
# ~1.0s wall time. The old per-event relative sleeps accumulated the tick cost
# (>=1.2s); absolute deadlines absorb it.
import time as _time  # noqa: E402

t0 = _time.monotonic()
eng.play([{"delay": 10, "type": "wait"}] * 100, tick=lambda: _time.sleep(0.002))
drift_t = _time.monotonic() - t0
check("playback timing drift-free", 0.93 <= drift_t <= 1.15, "%.3fs (want ~1.0s)" % drift_t)

# 3. serial protocol line parsing (the CircuitPython bytearray regression)
from mkyada.proto import Proto  # noqa: E402


class FakeSerial:
    def __init__(self, chunks):
        self.buf = b"".join(chunks)
        self.connected = True

    @property
    def in_waiting(self):
        return len(self.buf)

    def read(self, n):
        out, self.buf = self.buf[:n], self.buf[n:]
        return out

    def write(self, data):
        return len(data)


p = Proto()
p.ser = FakeSerial([b'{"t":"ping"}\n{"t":"iden', b'tify"}\npartial'])
msgs = p.poll()
check("proto parses two lines", [m["t"] for m in msgs] == ["ping", "identify"], str(msgs))
check("proto keeps partial", bytes(p.buf) == b"partial", str(bytes(p.buf)))

# 4. App logic (exec mkyada/app.py's body; nothing runs at module level —
# code.py's bootstrap is what calls main())
with open(os.path.join(FFW, "mkyada", "app.py")) as f:
    src = f.read()
code_mod = types.ModuleType("fwmain")
exec(compile(src, "app.py", "exec"), code_mod.__dict__)

app = code_mod.App()
check("default key_count", app.config["key_count"] == 6)
check("default key_map identity", app.config["key_map"] == [1, 2, 3, 4, 5, 6])
check("macro path layer a", app.macro_path(1) == "/macros/key1.json")
app.layer = 1
check("macro path layer b", app.macro_path(3) == "/macros/key3-b.json")
app.layer = 0

hello = app.hello()
check("hello uid", hello["uid"] == "0001020304050607")
check("hello mode", hello["mode"] == "standalone")

# layer toggle via on_edge (+ every change announces {"t":"layer"} to the app)
app.config["layer_key"] = 6
app.config["layer_count"] = 3
layer_msgs = []
_orig_send = app.proto.send
app.proto.send = lambda obj: (layer_msgs.append(obj), True)[1]
app.on_edge(5, True)
check("toggle -> layer b", app.layer == 1)
check("layer announced", layer_msgs[-1] == {"t": "layer", "layer": "b"}, str(layer_msgs))
app.on_edge(5, True)
check("toggle -> layer c", app.layer == 2)
app.on_edge(5, True)
check("toggle wraps -> a", app.layer == 0)

# "hold" layer mode was removed — even with it in config, press just cycles
app.config["layer_mode"] = "hold"
app.on_edge(5, True)
check("hold config still cycles", app.layer == 1)
app.on_edge(5, False)
check("release does nothing", app.layer == 1)
app.on_edge(5, True)
app.on_edge(5, True)
check("back to a", app.layer == 0)
app.proto.send = _orig_send

# key_map remap: GPIO 0 -> logical key 3
app.config["layer_key"] = None
app.config["layer_mode"] = "toggle"
app.config["key_map"] = [3, 1, 2, 4, 5, 6]
played = []
app.play_file = lambda path, trigger=None, **kw: played.append(path)
app.on_edge(0, True)
check("remap gpio0 -> key3", played == ["/macros/key3.json"], str(played))
app.on_edge(1, True)
check("remap gpio1 -> key1", played[-1] == "/macros/key1.json", str(played))

# key_map validation: bad map falls back to identity
app.config = dict(app.config)
del app.play_file  # restore real method

# more than 6 keys: key_count 8 survives load_config; 13 clamps to the pin count
import builtins as _b, io as _io
_real_open = _b.open
def _cfg_open(payload):
    def fake(path, *a, **k):
        if str(path) == "/config.json":
            return _io.StringIO(json.dumps(payload))
        return _real_open(path, *a, **k)
    return fake
_b.open = _cfg_open({"key_count": 8})
app.load_config()
check("8 keys allowed", app.config["key_count"] == 8, str(app.config["key_count"]))
check("8-key identity map", app.config["key_map"] == list(range(1, 9)), str(app.config["key_map"]))
_b.open = _cfg_open({"key_count": 99})
app.load_config()
check("key_count clamped to pins", app.config["key_count"] == 20, str(app.config["key_count"]))
_b.open = _real_open
_b.open = _cfg_open({"key_count": 6})
app.load_config()
_b.open = _real_open
app.config["key_map"] = [3, 1, 2, 4, 5, 6]

# host mode: btn events carry logical key + physical pin
outbox = []
app.proto.send = lambda obj: (outbox.append(obj), True)[1]
app.handle_msg({"t": "host_enter"})
check("mode host", app.mode == "host")
app.on_edge(1, True)
check("btn streamed logical", any(m.get("t") == "btn" and m["key"] == 1 for m in outbox), str(outbox))
check("btn has phys", any(m.get("t") == "btn" and m.get("phys") == 2 for m in outbox), str(outbox))

# play command with missing file -> err not_found
outbox.clear()
app.handle_msg({"t": "play", "file": "macros/nope.json"})
check("err not_found", any(m.get("code") == "not_found" for m in outbox), str(outbox))

# --- playback collision policies + hold-to-repeat ------------------------
import tempfile

app.handle_msg({"t": "host_leave"})
app.config["key_map"] = list(range(1, 7))
app.config["layer_key"] = None
app.config["busy_other"] = "ignore"
_orig_scan = app.buttons.scan
_orig_play = app.engine.play

def macro_file(settings):
    f = tempfile.NamedTemporaryFile("w", suffix=".json", delete=False)
    json.dump({"format": "mkyada-macro", "version": 2, "settings": settings,
               "events": [{"delay": 0, "type": "key", "action": "down", "key": "a"},
                          {"delay": 0, "type": "key", "action": "up", "key": "a"}]}, f)
    f.close()
    return f.name

# on_repress "restart": same key mid-play queues a replay
path_restart = macro_file({"on_repress": "restart"})
presses = [[(0, True)]]
app.buttons.scan = lambda: presses.pop(0) if presses else []
app.pending_play = None
app.play_file(path_restart, trigger=0)
check("restart queues same macro", app.pending_play == (path_restart, 0), str(app.pending_play))

# on_repress default: same key just stops
path_stop = macro_file({})
presses = [[(0, True)]]
app.pending_play = None
app.play_file(path_stop, trigger=0)
check("re-press stops by default", app.pending_play is None, str(app.pending_play))

# busy_other "switch": another key mid-play queues that key's macro
app.config["busy_other"] = "switch"
presses = [[(2, True)]]
app.pending_play = None
app.play_file(path_stop, trigger=0)
check("switch queues other macro", app.pending_play == ("/macros/key3.json", 2), str(app.pending_play))

# busy_other "ignore" (default): another key does nothing
app.config["busy_other"] = "ignore"
presses = [[(2, True)]]
app.pending_play = None
app.play_file(path_stop, trigger=0)
check("ignore keeps playing", app.pending_play is None, str(app.pending_play))

# single keys hold like a real keyboard BY DEFAULT (issue #20): the HID key
# stays down while the physical key is down — the host's typematic repeat
# makes the eeee… — and is released when the key is released. No replay loop.
path_hold = macro_file({})  # plain tap, no explicit hold_repeat
sent_reports.clear()
runs = {"n": 0}
app.engine.play = lambda *a, **kw: runs.__setitem__("n", runs["n"] + 1)
app.buttons.scan = lambda: []
app.buttons.stable[0] = True
_orig_tick = app.led.tick
ticks = {"n": 0}
def _release_after_3_ticks():
    ticks["n"] += 1
    if ticks["n"] >= 3:
        app.buttons.stable[0] = False
app.led.tick = _release_after_3_ticks
app.play_file(path_hold, trigger=0)
kbd = [r[2] for r in sent_reports if r[1] == 0x06]
check("hold: key pressed", any(0x04 in r[2:] for r in kbd), str(kbd))
check("hold: released on key-up", kbd and 0x04 not in kbd[-1][2:], str(kbd))
check("hold: held across ticks", ticks["n"] >= 3, str(ticks))
check("hold: no replay loop", runs["n"] == 0, str(runs))

# A momentary MIDI note rides the same hold path with a different transport:
# note_on on press, note_off on release. This is the mode Ableton's Looper and
# drum-rack pads need — a note that only ever sends "on" reads as stuck.
_midi_note = tempfile.NamedTemporaryFile("w", suffix=".json", delete=False)
json.dump({"format": "mkyada-macro", "version": 2, "kind": "midi",
           "midi": {"msg": "note", "ch": 0, "d1": 60, "d2": 100,
                    "mode": "momentary"},
           "events": [
               {"delay": 0, "type": "midi", "m": "note_on", "ch": 0,
                "d1": 60, "d2": 100},
               {"delay": 0, "type": "midi", "m": "note_off", "ch": 0,
                "d1": 60}]}, _midi_note)
_midi_note.close()
sent_midi.clear()
runs["n"] = 0
app.buttons.stable[0] = True
ticks["n"] = 0
app.led.tick = _release_after_3_ticks
app.play_file(_midi_note.name, trigger=0)
check("momentary: note on then off around the hold",
      sent_midi == [b"\x90\x3c\x64", b"\x80\x3c\x00"], str(sent_midi))
check("momentary: held across ticks, never replayed",
      ticks["n"] >= 3 and runs["n"] == 0, "ticks=%s runs=%s" % (ticks, runs))

# "tap" mode is the same two events, so only the payload tells them apart:
# it must go through normal playback instead of the hold path
_midi_tap = tempfile.NamedTemporaryFile("w", suffix=".json", delete=False)
json.dump({"format": "mkyada-macro", "version": 2, "kind": "midi",
           "midi": {"msg": "note", "ch": 0, "d1": 60, "d2": 100,
                    "mode": "tap"},
           "events": [
               {"delay": 0, "type": "midi", "m": "note_on", "ch": 0,
                "d1": 60, "d2": 100},
               {"delay": 20, "type": "midi", "m": "note_off", "ch": 0,
                "d1": 60}]}, _midi_tap)
_midi_tap.close()
sent_midi.clear()
runs["n"] = 0
app.buttons.stable[0] = True
ticks["n"] = 0
app.play_file(_midi_tap.name, trigger=0)
check("tap: plays straight through, no hold", runs["n"] == 1, str(runs))
# leave app.engine.play / led.tick stubbed: the checks below still count runs

# "hold_repeat": false opts a single key back into play-once
path_once = macro_file({"hold_repeat": False})
app.led.tick = _orig_tick
app.buttons.stable[0] = True
runs["n"] = 0
app.play_file(path_once, trigger=0)
check("hold_repeat false plays once", runs["n"] == 1, str(runs))
app.buttons.stable[0] = False

# non-single-key macros keep the replay-while-held behaviour
def multi_macro_file(settings):
    f = tempfile.NamedTemporaryFile("w", suffix=".json", delete=False)
    json.dump({"format": "mkyada-macro", "version": 2, "settings": settings,
               "events": [{"delay": 0, "type": "key", "action": "down", "key": "ctrl_l"},
                          {"delay": 0, "type": "key", "action": "down", "key": "a"},
                          {"delay": 0, "type": "key", "action": "up", "key": "a"},
                          {"delay": 0, "type": "key", "action": "up", "key": "ctrl_l"}]}, f)
    f.close()
    return f.name

path_multi = multi_macro_file({"hold_repeat": True})
runs["n"] = 0
def _fake_play(events, **kw):
    runs["n"] += 1
    if runs["n"] >= 3:
        app.buttons.stable[0] = False
app.engine.play = _fake_play
app.buttons.stable[0] = True
app.play_file(path_multi, trigger=0)
check("hold_repeat replays while held", runs["n"] == 3, str(runs))

# serial hold (proto v5): {"t":"play","hold":true} keeps the key down until
# the app's {"t":"stop"} — how host mode gives profile keys the same feel
app.engine.play = _orig_play
sent_reports.clear()
app.proto.ser = FakeSerial([])  # connected, so the hold doesn't bail out
app.last_rx = _time.monotonic()
_orig_poll = app.proto.poll
polls = {"n": 0}
def _stop_on_second_poll():
    polls["n"] += 1
    return [{"t": "stop"}] if polls["n"] >= 2 else []
app.proto.poll = _stop_on_second_poll
app.play_file(path_hold, trigger=None, hold=True)
kbd = [r[2] for r in sent_reports if r[1] == 0x06]
check("serial hold: key pressed", any(0x04 in r[2:] for r in kbd), str(kbd))
check("serial hold: released on stop", kbd and 0x04 not in kbd[-1][2:], str(kbd))
check("serial hold: waited for stop", polls["n"] >= 2, str(polls))
app.proto.poll = _orig_poll
app.proto.ser = None

app.buttons.scan = _orig_scan
app.engine.play = _orig_play

# --- remote control (proto v17): press / stop reply / playing state --------
# Users on a remote desktop can't touch the keypad: the app must be able to
# stop a looping macro and "press" a key exactly like a physical press.
def _ev(k):
    return [{"delay": 0, "type": "key", "action": "down", "key": k},
            {"delay": 0, "type": "key", "action": "up", "key": k}]

def rc_file(settings, variants=None, events=None):
    f = tempfile.NamedTemporaryFile("w", suffix=".json", delete=False)
    d = {"format": "mkyada-macro", "version": 3, "settings": settings,
         "events": events or _ev("a")}
    if variants:
        d["variants"] = variants
    json.dump(d, f)
    f.close()
    return f.name

rc_paths = {}
_orig_mpf = app.macro_path_for
app.macro_path_for = lambda k, l: rc_paths.get((k, l), "/nonexistent/key%d.json" % k)
app.macro_path = lambda k: app.macro_path_for(k, app.layer)
app.config["key_map"] = list(range(1, 7))
app.config["layer_key"] = None
app.config["layer_count"] = 3
app.config["busy_other"] = "ignore"
app.layer = 0
app.pending_play = None
app.remote = None
app.inbox = []
app.proto.ser = FakeSerial([])  # connected: key_action is only sent then
app.last_rx = _time.monotonic()
rc_out = []
app.proto.send = lambda obj: (rc_out.append(obj), True)[1]
rc_inbox = []
app.proto.poll = lambda: [rc_inbox.pop(0)] if rc_inbox else []
app.buttons.scan = lambda: []
rc_played = []
rc_seen = {}

def rc_engine(evs, **kw):
    """Record the played keys; a loop keeps asking should_stop until told."""
    rc_played.append([e.get("key") for e in evs])
    rc_seen["hello"] = app.hello().get("playing")
    for _ in range(50):
        if kw["should_stop"]():
            raise StopPlayback()
        if not rc_inbox:
            return

app.engine.play = rc_engine

def rc_by(t, **kv):
    return [m for m in rc_out
            if m.get("t") == t and all(m.get(k) == v for k, v in kv.items())]

# validation errors answer err re:"press" and queue nothing
for bad, code in (({"key": 0}, "bad_key"), ({"key": 9}, "bad_key"),
                  ({"key": "2"}, "bad_key"), ({"key": 2, "layer": 7}, "bad_layer"),
                  ({"key": 2, "layer": "z"}, "bad_layer"),
                  ({"key": 2, "gesture": "triple"}, "bad_gesture")):
    rc_out.clear()
    app.handle_msg(dict(bad, t="press"))
    check("press rejects %s" % code, rc_by("err", re="press", code=code)
          and app.remote is None, str(rc_out))

# idle press is queued, never run inside handle_msg
rc_paths[(2, 0)] = rc_file({}, variants={"double": {"events": _ev("d")},
                                         "hold": {"events": _ev("h")}})
rc_out.clear()
app.handle_msg({"t": "press", "key": 2})
check("press queued, not played in handle_msg",
      app.remote == (2, 0, "tap") and not rc_by("play_start"), str(rc_out))
app.handle_msg({"t": "press", "key": 2, "layer": "b", "gesture": "hold"})
check("press layer letter + gesture", app.remote == (2, 1, "hold"), str(app.remote))
# a stop right after a press drops the queued press
rc_out.clear()
app.handle_msg({"t": "stop"})
check("idle stop replies was_playing false",
      rc_by("ok", re="stop", was_playing=False), str(rc_out))
check("idle stop drops queued press", app.remote is None)

# gestures pick the variant directly (no physical key is read)
for g, want in (("tap", "a"), ("double", "d"), ("hold", "h")):
    rc_out.clear()
    rc_played.clear()
    app.remote_press(2, 0, g)
    check("press %s plays its variant" % g, rc_played == [[want, want]], str(rc_played))
    check("press %s announces key_action" % g,
          rc_by("key_action", key=2, variant=g, layer="a"), str(rc_out))
    check("press %s ok play" % g, rc_by("ok", re="press", action="play"), str(rc_out))
st = rc_by("play_start")
check("play_start carries key/layer/loop/src",
      st and st[-1].get("key") == 2 and st[-1].get("layer") == "a"
      and st[-1].get("loop") is False and st[-1].get("src") == "remote", str(st))
check("play_done reason done", rc_by("play_done", reason="done", stopped=False), str(rc_out))

# a looping key: hello reports it, a serial stop ends it and is acknowledged
rc_paths[(3, 0)] = rc_file({"repeat": 0})
rc_out.clear()
rc_inbox[:] = [{"t": "ping"}, {"t": "stop"}]
app.remote_press(3, 0, "tap")
check("hello.playing during a loop",
      rc_seen.get("hello") == {"file": rc_paths[(3, 0)], "key": 3,
                               "layer": "a", "loop": True}, str(rc_seen))
check("loop play_start loop:true", rc_by("play_start", loop=True, key=3), str(rc_out))
check("stop mid-loop acknowledged", rc_by("ok", re="stop", was_playing=True), str(rc_out))
check("stop mid-loop reason stop", rc_by("play_done", stopped=True, reason="stop"), str(rc_out))
check("hello.playing cleared after", app.hello().get("playing") is None)

# pressing the playing key remotely = physical re-press (stop)
rc_out.clear()
rc_inbox[:] = [{"t": "press", "key": 3}]
app.remote_press(3, 0, "tap")
check("remote re-press stops the loop",
      rc_by("play_done", stopped=True, reason="repress")
      and rc_by("ok", re="press", action="stop") and app.remote is None, str(rc_out))

# on_repress "restart": the re-press queues the same press again
rc_paths[(4, 0)] = rc_file({"repeat": 0, "on_repress": "restart"})
rc_out.clear()
rc_inbox[:] = [{"t": "press", "key": 4, "gesture": "double"}]
app.remote_press(4, 0, "tap")
check("remote re-press restart queues it", app.remote == (4, 0, "double")
      and rc_by("play_done", reason="repress"), str((app.remote, rc_out)))
app.remote = None

# another key while busy: busy_other ignore -> err busy, loop keeps going
rc_out.clear()
rc_inbox[:] = [{"t": "press", "key": 2}, {"t": "stop"}]
app.remote_press(3, 0, "tap")
check("other key ignored -> err busy", rc_by("err", re="press", code="busy")
      and rc_by("play_done", reason="stop") and app.remote is None, str(rc_out))
# ...busy_other switch -> stops and queues the other key's press
app.config["busy_other"] = "switch"
rc_out.clear()
rc_inbox[:] = [{"t": "press", "key": 2, "gesture": "hold"}]
app.remote_press(3, 0, "tap")
check("other key switch queues it", app.remote == (2, 0, "hold")
      and rc_by("play_done", reason="other"), str((app.remote, rc_out)))
app.remote = None
app.config["busy_other"] = "ignore"
# a bad press mid-playback is refused without stopping anything
rc_out.clear()
rc_inbox[:] = [{"t": "press", "key": 99}, {"t": "stop"}]
app.remote_press(3, 0, "tap")
check("bad press mid-loop doesn't stop", rc_by("err", re="press", code="bad_key")
      and rc_by("play_done", reason="stop"), str(rc_out))

# a physical press of the remotely started key is a re-press too
rc_out.clear()
_phys = [[(2, True)]]
app.buttons.scan = lambda: _phys.pop(0) if _phys else []
app.remote_press(3, 0, "tap")
check("physical key re-presses a remote loop",
      rc_by("play_done", reason="repress"), str(rc_out))
app.buttons.scan = lambda: []

# test mode doesn't block a remote press (explicit user action)
app.test_mode = True
rc_out.clear()
app.remote_press(2, 0, "tap")
check("remote press plays in test mode", rc_by("play_start", src="remote"), str(rc_out))
app.test_mode = False

# layer key cycles the layer; menu keys and missing files are refused
app.config["layer_key"] = 6
rc_out.clear()
app.remote_press(6, 0, "tap")
check("remote layer key cycles", app.layer == 1
      and rc_by("ok", re="press", action="layer"), str(rc_out))
app.set_layer_idx(0)
app.config["layer_key"] = None
_orig_pom = app.press_opens_menu
app.press_opens_menu = lambda k, l=None: True
rc_out.clear()
app.remote_press(2, 0, "tap")
check("menu key -> err unsupported", rc_by("err", re="press", code="unsupported")
      and not rc_by("play_start"), str(rc_out))
app.press_opens_menu = _orig_pom
rc_out.clear()
app.remote_press(5, 2, "tap")
check("unassigned key -> err not_assigned",
      rc_by("err", re="press", code="not_assigned"), str(rc_out))
app.xfer = True
rc_out.clear()
app.remote_press(2, 0, "tap")
check("press during transfer -> err busy", rc_by("err", re="press", code="busy")
      and not rc_by("play_start"), str(rc_out))
app.xfer = False

# a stop that lands while a physical gesture is still resolving (pump()
# parks it in the inbox) must cancel the playback that follows
rc_paths[(1, 0)] = rc_file({"repeat": 0, "double_ms": 20},
                           variants={"double": {"events": _ev("d")}})
app.buttons.stable[0] = True
def _release_scan():
    app.buttons.stable[0] = False
    return []
app.buttons.scan = _release_scan
rc_inbox[:] = [{"t": "stop"}]
rc_out.clear()
rc_played.clear()
app.play_file(rc_paths[(1, 0)], trigger=0)
check("stop during gesture resolution cancels the loop",
      not rc_played and rc_by("play_done", stopped=True, reason="stop")
      and rc_by("ok", re="stop", was_playing=True), str((rc_played, rc_out)))
check("physical play_start src key", rc_by("play_start", src="key", key=1), str(rc_out))
check("inbox emptied of the stop", not any(m.get("t") == "stop" for m in app.inbox))

# the app's play command reports src host
rc_out.clear()
app.handle_msg({"t": "play", "file": rc_paths[(2, 0)].lstrip("/")})
check("host play src host", rc_by("play_start", src="host", key=None), str(rc_out))

app.inbox = []
app.buttons.scan = _orig_scan
app.engine.play = _orig_play
app.proto.poll = _orig_poll
app.proto.ser = None
app.proto.send = lambda obj: (outbox.append(obj), True)[1]
del app.macro_path_for, app.macro_path  # back to the real methods

# --- v4 stream macro files (proto v4): header line + one event per line ---
def stream_macro_file(events, settings=None):
    f = tempfile.NamedTemporaryFile("w", suffix=".json", delete=False)
    hdr = {"format": "mkyada-macro", "version": 4, "stream": True,
           "screen": {"width": 1920, "height": 1080}}
    if settings:
        hdr["settings"] = settings
    f.write(json.dumps(hdr) + "\n")
    for ev in events:
        f.write(json.dumps(ev) + "\n")
    f.close()
    return f.name


tap_events = [{"delay": 0, "type": "key", "action": "down", "key": "a"},
              {"delay": 0, "type": "key", "action": "up", "key": "a"}]

outbox.clear()
sent_reports.clear()
path_stream = stream_macro_file(
    tap_events + [{"delay": 0, "type": "move", "x": 960, "y": 540}])
app.play_file(path_stream)
check("stream file plays", any(m.get("t") == "play_done" and not m.get("stopped")
                               for m in outbox), str(outbox))
check("stream kbd 'a' pressed", any(r[1] == 0x06 and r[2][2] == 0x04 for r in sent_reports))
check("stream move emitted", any(r[1] == 0x02 for r in sent_reports))
check("stream no error", not any(m.get("t") == "err" for m in outbox), str(outbox))

# repeat replays by seeking back to the first event line — no extra RAM
outbox.clear()
sent_reports.clear()
path_stream3 = stream_macro_file(tap_events, settings={"repeat": 3})
app.play_file(path_stream3)
presses3 = sum(1 for r in sent_reports if r[1] == 0x06 and r[2][2] == 0x04)
check("stream repeat=3 replays 3x", presses3 == 3, str(presses3))

# a corrupt event line is skipped, not fatal
path_corrupt = stream_macro_file(tap_events)
with open(path_corrupt, "a") as fh:
    fh.write("{not json}\n")
    fh.write(json.dumps({"delay": 0, "type": "move", "x": 10, "y": 10}) + "\n")
outbox.clear()
app.play_file(path_corrupt)
check("stream corrupt line skipped",
      any(m.get("t") == "play_done" for m in outbox)
      and not any(m.get("t") == "err" for m in outbox), str(outbox))

# pretty-printed whole-file JSON still plays (hand-made files on the drive)
fpp = tempfile.NamedTemporaryFile("w", suffix=".json", delete=False)
json.dump({"format": "mkyada-macro", "version": 2, "events": tap_events}, fpp, indent=2)
fpp.close()
outbox.clear()
sent_reports.clear()
app.play_file(fpp.name)
check("pretty JSON still plays",
      any(m.get("t") == "play_done" for m in outbox)
      and not any(m.get("t") == "err" for m in outbox), str(outbox))

# a HID report the USB stack rejects (boot.py descriptor older than
# engine.py after a partial update) fails the key soft: err "hid" + LED
# blink, never the fatal handler's crash-loop. The macro must actually
# touch the mouse: keyboard-only macros no longer send pointer reports.
outbox.clear()


def _reject(buf, report_id=None):
    raise ValueError("report length must be 6")


fmm = tempfile.NamedTemporaryFile("w", suffix=".json", delete=False)
json.dump({"format": "mkyada-macro", "version": 2,
           "events": [{"delay": 0, "type": "move", "x": 10, "y": 10}]}, fmm)
fmm.close()
_orig_mouse_send = app.engine.mouse.send_report
app.engine.mouse.send_report = _reject
app.play_file(fmm.name)
check("hid mismatch -> err not crash",
      any(m.get("t") == "err" and m.get("code") == "hid" for m in outbox)
      and any(m.get("t") == "play_done" and m.get("stopped") for m in outbox),
      str(outbox))
app.engine.mouse.send_report = _orig_mouse_send

# --- key logic: tap / double press / long press (macro format v3) ---------
def variant_file():
    f = tempfile.NamedTemporaryFile("w", suffix=".json", delete=False)
    json.dump({
        "format": "mkyada-macro", "version": 3,
        "settings": {"hold_ms": 30, "double_ms": 30},
        "events": [{"delay": 0, "type": "key", "action": "down", "key": "a"},
                   {"delay": 0, "type": "key", "action": "up", "key": "a"}],
        "variants": {
            "double": {"events": [
                {"delay": 0, "type": "key", "action": "down", "key": "b"},
                {"delay": 0, "type": "key", "action": "up", "key": "b"}]},
            "hold": {"events": [
                {"delay": 0, "type": "key", "action": "down", "key": "c"},
                {"delay": 0, "type": "key", "action": "up", "key": "c"}]},
        },
    }, f)
    f.close()
    return f.name


def pressed_usages():
    return {r[2][2] for r in sent_reports if r[1] == 0x06 and r[2][2]}


path_variants = variant_file()
outbox.clear()
app.proto.send = lambda obj: (outbox.append(obj), True)[1]
app.proto.ser = FakeSerial([])  # "connected" so key_action is announced

# tap: key released before the call, no second press within the window
sent_reports.clear()
app.buttons.stable[0] = False
presses = []
app.buttons.scan = lambda: presses.pop(0) if presses else []
app.play_file(path_variants, trigger=0)
check("variant tap plays top-level events", pressed_usages() == {0x04}, str(pressed_usages()))
check("variant tap announced", any(
    m.get("t") == "key_action" and m.get("variant") == "tap" for m in outbox), str(outbox))

# double: a second press arrives inside the double window
sent_reports.clear()
outbox.clear()
app.buttons.stable[0] = False
presses = [[(0, True)]]
app.play_file(path_variants, trigger=0)
check("variant double plays double events", pressed_usages() == {0x05}, str(pressed_usages()))
check("variant double announced", any(
    m.get("t") == "key_action" and m.get("variant") == "double" for m in outbox), str(outbox))

# hold: key stays down past hold_ms
sent_reports.clear()
outbox.clear()
app.buttons.stable[0] = True
presses = []
app.play_file(path_variants, trigger=0)
check("variant hold plays hold events", pressed_usages() == {0x06}, str(pressed_usages()))
check("variant hold announced", any(
    m.get("t") == "key_action" and m.get("variant") == "hold" for m in outbox), str(outbox))
app.buttons.stable[0] = False
app.buttons.scan = _orig_scan
app.proto.send = _orig_send

# --- standalone btn streaming: edges reach a connected app in both modes --
outbox.clear()
app.proto.send = lambda obj: (outbox.append(obj), True)[1]
app.handle_msg({"t": "host_leave"})
app.play_file = lambda path, trigger=None, **kw: None  # don't actually play
app.on_edge(1, True)
check("standalone btn streamed when connected",
      any(m.get("t") == "btn" and m.get("edge") == "down" for m in outbox), str(outbox))
del app.play_file
app.proto.send = _orig_send
app.proto.ser = None

# --- serial "led" op (proto v2): app feedback override --------------------
check("hello reports proto v17", app.hello()["proto"] == 17, str(app.hello()["proto"]))
# hello reports the PORT, not the config key: boot.py can refuse MIDI (a
# visible drive, or key 1 held at power-on) while config still says true, and
# an "On" switch over a board that cannot send anything is a lie.
check("hello reports the live midi port", app.hello()["midi"] is True,
      str(app.hello().get("midi")))
_saved_ports = usb_midi.ports
usb_midi.ports = ()
check("hello reports midi off when boot.py refused it",
      app.hello()["midi"] is False, str(app.hello().get("midi")))
usb_midi.ports = _saved_ports
check("hello reports usb_drive", app.hello()["usb_drive"] == app.config["usb_drive"], str(app.hello()))

# profile path resolution (issue #23): a profile is a full independent config —
# numbered keys resolve to the profile's file with NO fallback (a cleared key
# does nothing), while module slots keep their standalone fallback.
app.handle_msg({"t": "profile", "id": "p_test"})
check("profile set via serial", app.profile_id == "p_test")
check("profile key path no fallback", app.macro_path_for(1, 0) == "/macros/p_test_key1.json",
      app.macro_path_for(1, 0))
check("profile key path ignores layer", app.macro_path_for(2, 1) == "/macros/p_test_key2.json",
      app.macro_path_for(2, 1))
check("profile slot falls back to standalone", app.slot_path("enc-cw", 0) == "/macros/enc-cw.json",
      app.slot_path("enc-cw", 0))
app.handle_msg({"t": "profile", "id": None})
check("profile cleared", app.profile_id is None)
check("no profile -> standalone key path", app.macro_path_for(1, 0) == "/macros/key1.json",
      app.macro_path_for(1, 0))
app.proto.ser = FakeSerial([])
app.handle_msg({"t": "led", "mode": "solid", "rgb": [255, 0, 0]})
check("led solid override set", app.led.override == ("solid", (255, 0, 0)), str(app.led.override))
app.handle_msg({"t": "led", "mode": "blink", "rgb": [0, 0, 255]})
check("led blink override set", app.led.override == ("blink", (0, 0, 255)), str(app.led.override))
app.handle_msg({"t": "led", "mode": "off"})
check("led override cleared by off", app.led.override is None, str(app.led.override))
app.handle_msg({"t": "led", "mode": "solid", "rgb": "garbage"})
check("led garbage rgb tolerated", app.led.override is None, str(app.led.override))

# --- serial "label" op (fw 0.9.0): app-pushed profile label ---------------
outbox.clear()
app.proto.send = lambda obj: (outbox.append(obj), True)[1]
app.handle_msg({"t": "label", "text": "Photoshop"})
check("label stored", app.host_label == "Photoshop", str(app.host_label))
check("label acked", outbox[-1] == {"t": "ok", "re": "label"}, str(outbox[-1:]))
app.handle_msg({"t": "label", "text": "x" * 40})
check("label truncated to 24", app.host_label == "x" * 24, str(app.host_label))
app.handle_msg({"t": "label", "text": ""})
check("label empty clears", app.host_label is None, str(app.host_label))
app.handle_msg({"t": "label"})
check("label missing text clears", app.host_label is None, str(app.host_label))

# proto v6: the label can carry the profile's key names (host-mode grid)
app.handle_msg({"t": "label", "text": "PS", "keys": ["Zoom in", "Zoom out",
                "", "Undo", "Redo", "Save", "extra7"]})
check("label keys stored (capped at 6)",
      app.host_keys == ["Zoom in", "Zoom out", "", "Undo", "Redo", "Save"],
      str(app.host_keys))
app.handle_msg({"t": "label", "text": "PS", "keys": ["", "", "", "", "", ""]})
check("label all-empty keys -> None", app.host_keys is None, str(app.host_keys))
app.handle_msg({"t": "label", "text": "PS", "keys": "garbage"})
check("label garbage keys tolerated", app.host_keys is None, str(app.host_keys))
app.handle_msg({"t": "label", "text": ""})
check("label clear drops keys too", app.host_label is None and app.host_keys is None)

# --- serial "scroll" op (proto v6): app-accelerated wheel -----------------
sent_reports.clear()
outbox.clear()
app.handle_msg({"t": "scroll", "dy": 4, "mods": ["CTRL"]})
check("scroll acked", outbox[-1] == {"t": "ok", "re": "scroll"}, str(outbox[-1:]))
s_wheel = [struct.unpack("<bb", r[2]) for r in sent_reports
           if r[1] == 0x02 and len(r[2]) == 2]
s_kbd = [r[2] for r in sent_reports if r[1] == 0x06]
check("scroll ticks sent", sum(1 for m in s_wheel if m[0] == 1) == 4, str(s_wheel))
check("scroll holds+releases ctrl",
      s_kbd and s_kbd[0][0] == 0x01 and s_kbd[-1][0] == 0x00, str(s_kbd))
outbox.clear()
app.handle_msg({"t": "scroll", "dy": "garbage"})
check("scroll garbage -> err", outbox[-1].get("code") == "hid", str(outbox[-1:]))
app.proto.send = _orig_send
app.proto.ser = None

# --- serial file management (proto v3): fs_* commands ---------------------
# The firmware roots every path at "/" (the CIRCUITPY drive). That maps
# directly onto a POSIX temp dir but not onto Windows drive letters, so this
# section runs on POSIX only (CI covers it).
import binascii  # noqa: E402
import shutil  # noqa: E402


def fs_section():
    fs_dir = tempfile.mkdtemp()  # absolute path; fs_path() keeps it absolute
    fs_rel = fs_dir.lstrip("/")
    outbox.clear()
    app.proto.send = lambda obj: (outbox.append(obj), True)[1]
    # meta.json (proto v14) lives next to the macros; point the module there
    # so the manifest-upkeep checks below see the real file
    import mkyada.meta as metamod
    _meta_path_orig = metamod.PATH
    metamod.PATH = fs_dir + "/macros/meta.json"

    # chunked write: two chunks + eof, lands atomically via .part + rename
    payload = b'{"format":"mkyada-macro","version":2,"events":[]}' * 50
    half = len(payload) // 2
    b64 = lambda b: binascii.b2a_base64(b).decode().strip()  # noqa: E731
    app.handle_msg({"t": "fs_write", "path": fs_rel + "/macros/key1.json",
                    "seq": 0, "data": b64(payload[:half]), "eof": False})
    check("fs_write chunk acked", outbox[-1] == {"t": "ok", "re": "fs_write", "seq": 0}, str(outbox[-1:]))
    app.handle_msg({"t": "fs_write", "path": fs_rel + "/macros/key1.json",
                    "seq": 1, "data": b64(payload[half:]), "eof": True})
    check("fs_write eof acked", outbox[-1].get("eof") is True, str(outbox[-1:]))
    with open(fs_dir + "/macros/key1.json", "rb") as f:
        check("fs_write content intact", f.read() == payload)
    check("fs_write .part cleaned", not os.path.exists(fs_dir + "/macros/key1.json.part"))

    # proto v14: the eof write maintains the meta.json manifest — crc+size
    # land in the entry, and any stale override is cleared (the body written
    # over serial carries the truth now)
    with open(metamod.PATH) as f:
        man = json.load(f)["entries"]
    want_crc = binascii.crc32(payload) & 0xFFFFFFFF
    check("fs_write updates manifest",
          man.get("key1", {}).get("c") == want_crc
          and man["key1"].get("z") == len(payload), str(man))
    metamod.update("key1", fields={"s": 55})
    app.meta_ov["key1"] = {"s": 55}
    app.handle_msg({"t": "fs_write", "path": fs_rel + "/macros/key1.json",
                    "seq": 0, "data": b64(payload), "eof": True})
    with open(metamod.PATH) as f:
        man = json.load(f)["entries"]
    check("fs_write clears stale overrides",
          "s" not in man.get("key1", {}) and "key1" not in app.meta_ov,
          str(man))

    # out-of-order chunk -> bad_seq error, upload discarded
    app.handle_msg({"t": "fs_write", "path": fs_rel + "/x.bin", "seq": 0,
                    "data": b64(b"aa"), "eof": False})
    app.handle_msg({"t": "fs_write", "path": fs_rel + "/x.bin", "seq": 5,
                    "data": b64(b"bb"), "eof": True})
    check("fs_write bad seq rejected", outbox[-1].get("code") == "bad_seq", str(outbox[-1:]))
    check("fs_write bad seq leaves no file", not os.path.exists(fs_dir + "/x.bin"))

    # read it back (multi-chunk: the app acks each chunk; stub that here)
    outbox.clear()
    app.wait_fs_ack = lambda: True
    app.handle_msg({"t": "fs_read", "path": fs_rel + "/macros/key1.json"})
    del app.wait_fs_ack
    chunks = [m for m in outbox if m.get("t") == "fs_chunk"]
    got = b"".join(binascii.a2b_base64(m["data"]) for m in chunks if m["data"])
    check("fs_read roundtrip", got == payload and chunks[-1]["eof"] is True,
          "%d chunks, %d bytes" % (len(chunks), len(got)))

    outbox.clear()
    app.handle_msg({"t": "fs_read", "path": fs_rel + "/nope.json"})
    check("fs_read missing -> not_found", outbox[-1].get("code") == "not_found", str(outbox[-1:]))

    # a MemoryError mid-read reports oom instead of propagating (which would
    # crash the loop and repaint the console onto the OLED)
    outbox.clear()
    _orig_send = app.proto.send
    _calls = {"n": 0}

    def _boom(obj):
        if obj.get("t") == "fs_chunk":
            _calls["n"] += 1
            raise MemoryError("simulated")
        return _orig_send(obj)

    app.proto.send = _boom
    app.wait_fs_ack = lambda: True
    app.handle_msg({"t": "fs_read", "path": fs_rel + "/macros/key1.json"})
    app.proto.send = _orig_send
    del app.wait_fs_ack
    # the adaptive reader halves the chunk a few times before giving up, so
    # several attempts are expected — what matters is err oom, not a crash
    check("fs_read oom -> err not crash",
          _calls["n"] >= 1 and outbox and outbox[-1].get("code") == "oom",
          str(outbox[-1:]))

    # list + delete
    outbox.clear()
    app.handle_msg({"t": "fs_list", "path": fs_rel + "/macros"})
    listed = outbox[-1]
    check("fs_list sees the file",
          listed.get("t") == "fs_list"
          and any(e["name"] == "key1.json" and e["size"] == len(payload) and not e["dir"]
                  for e in listed.get("entries", [])),
          str(listed))
    # a big directory pages its listing (>8 entries → "more"-flagged batches),
    # so the reply never needs one multi-KB dumps on a fragmented heap
    for i in range(20):
        with open(fs_dir + "/macros/pg%02d.json" % i, "w") as f:
            f.write("{}")
    outbox.clear()
    app.handle_msg({"t": "fs_list", "path": fs_rel + "/macros"})
    pages = [m for m in outbox if m.get("t") == "fs_list"]
    total = sum(len(p.get("entries", [])) for p in pages)
    check("fs_list paginates",
          len(pages) >= 3 and all(p.get("more") for p in pages[:-1])
          and not pages[-1].get("more") and total >= 20,
          "pages=%d total=%d" % (len(pages), total))
    for i in range(20):
        os.remove(fs_dir + "/macros/pg%02d.json" % i)

    app.handle_msg({"t": "fs_delete", "path": fs_rel + "/macros/key1.json"})
    check("fs_delete ok", outbox[-1].get("re") == "fs_delete" and outbox[-1].get("t") == "ok", str(outbox[-1:]))
    check("fs_delete removed", not os.path.exists(fs_dir + "/macros/key1.json"))
    with open(metamod.PATH) as f:
        check("fs_delete drops manifest entry",
              "key1" not in json.load(f)["entries"])

    # path traversal is refused
    outbox.clear()
    app.handle_msg({"t": "fs_read", "path": "../etc/passwd"})
    check("fs path traversal refused", outbox[-1].get("code") == "bad_path", str(outbox[-1:]))

    # mid-playback: fs ops answer busy instead of silently stalling the app
    outbox.clear()
    app.handle_msg({"t": "fs_write", "path": fs_rel + "/y.bin", "seq": 0,
                    "data": "", "eof": True}, in_playback=True)
    check("fs busy during playback", outbox[-1].get("code") == "busy", str(outbox[-1:]))

    app.proto.send = _orig_send
    metamod.PATH = _meta_path_orig
    shutil.rmtree(fs_dir, ignore_errors=True)


if os.name != "nt":
    fs_section()
else:
    print("SKIP fs_* section (POSIX-rooted paths; covered on CI)")

# usb_drive config: finished-product default is hidden (False); an explicit
# true shows the drive and survives load_config
_b.open = _cfg_open({"usb_drive": True})
app.load_config()
check("usb_drive true honored", app.config["usb_drive"] is True)
_b.open = _cfg_open({})
app.load_config()
check("usb_drive defaults off", app.config["usb_drive"] is False)
_b.open = _real_open
app.load_config()

# show_layer / show_profile (fw 0.9.0): default off, non-bool coerced off
_b.open = _cfg_open({"show_layer": True, "show_profile": "yes"})
app.load_config()
check("show_layer true honored", app.config["show_layer"] is True)
check("show_profile non-bool -> off", app.config["show_profile"] is False)
_b.open = _cfg_open({})
app.load_config()
check("band flags default off", app.config["show_layer"] is False
      and app.config["show_profile"] is False)
check("hello mirrors band flags", app.hello()["show_layer"] is False
      and app.hello()["show_profile"] is False, str(app.hello()))
_b.open = _real_open
app.load_config()

# --- models / two-device plumbing -----------------------------------------
from mkyada import models as modelsmod  # noqa: E402

VIS_PINS = ["GP29", "GP28", "GP27", "GP26", "GP15", "GP14"]
check("resolve core6", modelsmod.resolve_model("core6") == "core6")
check("resolve vision6", modelsmod.resolve_model("vision6") == "vision6")
check("resolve default (no i2c hw)", modelsmod.resolve_model(None) == "core6")
check("pins valid", modelsmod.validate_key_pins(VIS_PINS, 6, "vision6") == VIS_PINS)
check("pins wrong len", modelsmod.validate_key_pins(VIS_PINS[:5], 6, "vision6") is None)
check("pins reserved refused",
      modelsmod.validate_key_pins(["GP0"] + VIS_PINS[1:], 6, "vision6") is None)
check("pins duplicate refused",
      modelsmod.validate_key_pins(["GP29"] + VIS_PINS[:5], 6, "vision6") is None)
check("pins unknown refused",
      modelsmod.validate_key_pins(["GP99"] + VIS_PINS[1:], 6, "vision6") is None)
cands = modelsmod.detect_candidates("vision6")
check("detect candidates skip reserved",
      "GP13" in cands and not any(c in cands for c in
                                  ("GP0", "GP1", "GP2", "GP3", "GP4", "GP5", "GP6", "GP16")),
      str(cands))

hello2 = app.hello()
check("hello model core6", hello2["model"] == "core6", str(hello2.get("model")))
check("hello pins default order", hello2["pins"] == ["GP0", "GP1", "GP2", "GP3", "GP4", "GP5"],
      str(hello2["pins"]))

# custom pins survive load_config and drive the button pin list
_b.open = _cfg_open({"pins": ["GP5", "GP4", "GP3", "GP2", "GP1", "GP0"]})
app.load_config()
check("custom pins accepted", app.key_pin_names() == ["GP5", "GP4", "GP3", "GP2", "GP1", "GP0"])
_b.open = _cfg_open({"pins": ["GP16", "GP4", "GP3", "GP2", "GP1", "GP0"]})
app.load_config()
check("reserved pin falls back to default", app.config["pins"] is None)
_b.open = _real_open
app.load_config()

# pin_detect: wiring wizard streams GPIO edges, then restores the keys
outbox.clear()
app.proto.send = lambda obj: (outbox.append(obj), True)[1]
app.proto.ser = FakeSerial([])
app.handle_msg({"t": "pin_detect", "on": True})
check("pin watch armed", app.pin_watch is not None)
watch_names, watch_btns = app.pin_watch
watch_btns.ios[watch_names.index("GP13")].value = False  # user presses the key
import time as _t2  # noqa: E402

app.tick_pin_watch(_t2.monotonic())
check("pin event streamed",
      any(m.get("t") == "pin" and m.get("pin") == "GP13" and m.get("down") for m in outbox),
      str(outbox))
app.handle_msg({"t": "pin_detect", "on": False})
check("pin watch restored", app.pin_watch is None and len(app.buttons.stable) == 6)
app.proto.send = _orig_send
app.proto.ser = None

# --- vision6: fresh module exec with a vision6 config ---------------------
_b.open = _cfg_open({"model": "vision6", "layer_key": 3, "layer_count": 1,
                     "key_count": 12})
vis_mod = types.ModuleType("fwvis")
exec(compile(src, "app.py", "exec"), vis_mod.__dict__)
vapp = vis_mod.App()
_b.open = _real_open
import mkyada.ui as uimod  # noqa: E402

check("vision6 model resolved", vapp.model == "vision6")
check("vision6 layer_key forced null", vapp.config["layer_key"] is None)
check("vision6 single layer allowed", vapp.config["layer_count"] == 1)
check("vision6 key_count clamped to 6", vapp.config["key_count"] == 6)
vhello = vapp.hello()
check("vision6 hello model", vhello["model"] == "vision6")
check("vision6 hello pins", vhello["pins"] == VIS_PINS, str(vhello["pins"]))
check("vision6 oled headless on desktop", vis_mod.OLED is not None and not vis_mod.OLED.ok)
check("vision6 ui attached", vapp.ui is not None)

# --- vision6 UI: labels, speed persistence, slots, host events ------------
ui = vapp.ui
voutbox = []
vapp.proto.send = lambda obj: (voutbox.append(obj), True)[1]
vapp.proto.ser = FakeSerial([])
# The device's paths are always POSIX ("/macros/key1.json"), and the firmware
# splits them accordingly — meta.stem_of() does path.rsplit("/", 1). Handing
# it os.path.join's backslashes on Windows made every sidecar entry key on the
# whole absolute path, so the meta tests failed there and only there while CI
# (Linux) stayed green. Join the way the device does, on every platform.
mac_dir = tempfile.mkdtemp().replace(os.sep, "/")
LN = "abcdefgh"


def mpath(name):
    return "%s/%s" % (mac_dir, name)


def vpath(k, l):
    return mpath("key%d%s.json" % (k, "" if l == 0 else "-" + LN[l]))


vapp.macro_path_for = vpath
vapp.slot_path = lambda s, l: mpath(
    "%s%s.json" % (s, "" if l == 0 else "-" + LN[l]))

with open(vpath(1, 0), "w") as f:  # v4 stream file: name+speed in the header
    f.write(json.dumps({"format": "mkyada-macro", "version": 4, "stream": True,
                        "name": "volume up", "settings": {"speed": 1.5}}) + "\n")
    f.write(json.dumps({"delay": 0, "type": "key", "action": "down", "key": "a"}) + "\n")
    f.write(json.dumps({"delay": 0, "type": "key", "action": "up", "key": "a"}) + "\n")
with open(vpath(2, 0), "w") as f:  # single-line legacy whole-file macro
    json.dump({"format": "mkyada-macro", "version": 2, "name": "mute",
               "settings": {"speed": 2.0}, "events": []}, f)

ui.load_layer(0)
vlabels = ui.labels(0)
# "volume up" is 35px wide and a cell holds 40, so it now stays on ONE line.
# The old fixed 10-character cut split it for no reason — that is the
# proportional font paying for itself.
check("label split from stream header", vlabels[0] == ("volume up", ""), str(vlabels[0]))
check("label fallback K3", vlabels[2][0] == "K3", str(vlabels))
check("speed tenths from stream", ui.speed_tenths(0, 0) == 15)
check("speed tenths from legacy", ui.speed_tenths(0, 1) == 20)

# Splitting is by pixels now. The display is headless here (no I2C bus on a
# desktop) so no font was loaded; attach the real one so these exercise the
# metrics the device actually uses.
from mkyada.font import Font as _Font  # noqa: E402
ui.oled.font = _Font(os.path.join(FFW, "fonts", "mkyada.fnt"))
ui._labels.clear()
ui.load_layer(0)
vlabels = ui.labels(0)
check("split short stays", ui._split_name("copy") == ("copy", ""))
check("split at word gap", ui._split_name("switch weapon") == ("switch", "weapon"),
      str(ui._split_name("switch weapon")))
check("narrow letters pack tighter than wide ones",
      ui._split_name("lllllllllllll")[1] == ""
      and ui._split_name("WWWWWWWWWWWWW")[1] != "")
check("split hard cut", ui._split_name("abcdefghijklmnop") == ("abcdefghij", "klmnop"))

# proto v14: a speed edit writes /macros/meta.json, never the macro body —
# the old whole-file rewrite could out-run the watchdog on a long recording
import mkyada.meta as metamod  # noqa: E402

metamod.PATH = mpath("meta.json")
with open(vpath(1, 0), "rb") as f:
    v_before = f.read()
res = ui.persist_speed(0, 0, 30)
check("persist speed ok", res == "ok")
with open(vpath(1, 0), "rb") as f:
    check("persist leaves macro bytes untouched", f.read() == v_before)
with open(metamod.PATH) as f:
    vmeta = json.load(f)
check("meta sidecar format", vmeta.get("format") == "mkyada-meta")
check("meta speed entry", vmeta["entries"]["key1"]["s"] == 30, str(vmeta))
check("persist announces macro_changed",
      any(m.get("t") == "macro_changed" and m.get("reason") == "speed" for m in voutbox),
      str(voutbox))
check("persist cache updated", ui.speed_tenths(0, 0) == 30)
check("persist resident override", vapp.meta_ov.get("key1", {}).get("s") == 30)
check("persist missing file", ui.persist_speed(0, 4, 10) == "missing")
res2 = ui.persist_speed(0, 1, 5)
with open(vpath(2, 0)) as f:
    vdata2 = json.load(f)
check("persist whole-file body untouched",
      res2 == "ok" and vdata2["settings"]["speed"] == 2.0)
with open(metamod.PATH) as f:
    check("meta second entry", json.load(f)["entries"]["key2"]["s"] == 5)

# a fresh boot re-reads only the override fields, and the layer cache
# re-applies them after an invalidate
check("load_overrides picks up sidecar",
      metamod.load_overrides().get("key1") == {"s": 30})
ui.invalidate_labels()
check("speed override survives cache drop", ui.speed_tenths(0, 0) == 30)

# playback resolves the override too (meta_ov beats the header's 1.5)
_played = {}
_orig_engine_play = vapp.engine.play


def _spy_play(events, **kw):
    _played.update(kw)


vapp.engine.play = _spy_play
vapp.play_file(vpath(1, 0))
vapp.engine.play = _orig_engine_play
check("play_file uses meta speed", _played.get("speed") == 3.0,
      str(_played.get("speed")))

# per-profile speed (issue #23): the override keys on the PROFILE's stem —
# no copy-on-write of the whole file anymore. A key without a profile file
# is unassigned in that profile, so its speed edit reports missing.
def vprof_path(k, l):
    return mpath("p_test_key%d.json" % k)


_vpath_std = vapp.macro_path_for
vapp.profile_id = "p_test"
vapp.macro_path_for = vprof_path  # what the real one resolves under a profile
check("profile speed missing without file", ui.persist_speed(0, 0, 40) == "missing")
shutil.copyfile(vpath(1, 0), vprof_path(1, 0))
check("profile speed ok", ui.persist_speed(0, 0, 40) == "ok")
with open(metamod.PATH) as f:
    ventries = json.load(f)["entries"]
check("profile override on profile stem",
      ventries.get("p_test_key1", {}).get("s") == 40
      and ventries["key1"]["s"] == 30, str(ventries))
with open(vpath(1, 0), "rb") as f:  # standalone macro still untouched
    check("standalone macro untouched", f.read() == v_before)
vapp.profile_id = None
vapp.macro_path_for = _vpath_std
ui._speeds.clear()  # drop the profile-scoped cache before the slot tests

with open(vapp.slot_path("enc-cw", 0), "w") as f:  # custom encoder slot
    json.dump({"format": "mkyada-macro", "version": 2, "name": "vol+",
               "events": []}, f)
ui.invalidate_labels()
check("slot found on layer a", bool(ui.slots(0)["enc-cw"]))
check("slot layer b falls back to a",
      ui.slots(1)["enc-cw"]["path"] == vapp.slot_path("enc-cw", 0),
      str(ui.slots(1)["enc-cw"]))
check("slot unassigned is None", ui.slots(0)["btn-back"] is None)
check("slot meta tap is play", ui.slots(0)["enc-cw"]["tap"] == ("play",),
      str(ui.slots(0)["enc-cw"]))

# boot goes straight to the active layer's grid, not the layer picker
ui.start()
check("boot lands on grid not home", ui.state == uimod.S_SELECT)

vplays = []
vapp.play_file = lambda path, trigger=None, **k: vplays.append(path)
ui.state = uimod.S_SELECT
ui.sel_mode = False
ui.enc.position += 2
ui.tick(_t2.monotonic())
check("custom encoder plays per detent",
      vplays == [vapp.slot_path("enc-cw", 0)] * 2, str(vplays))
ui.state = uimod.S_SELECT
ui.sel_mode = True  # select mode: rotation moves the cell instead
vplays.clear()
ui.enc.position += 1
ui.tick(_t2.monotonic())
check("select mode keeps navigation", vplays == [] and ui.sel_key == 1,
      "%s sel=%d" % (vplays, ui.sel_key))

ui._labels[1] = [("x", "")] * 6
ui.invalidate_labels("/macros/key3-b.json")
check("invalidate drops layer b", 1 not in ui._labels)

# menu-nav injected by a macro key drives the UI like the encoder/buttons
ui.state = uimod.S_SELECT
ui.sel_mode = True   # plain navigation grid
ui.sel_key = 0
ui.inject("right")
check("inject right moves selection", ui.sel_key == 1, "sel=%d" % ui.sel_key)
ui.inject("left")
check("inject left moves selection", ui.sel_key == 0, "sel=%d" % ui.sel_key)
ui.inject("confirm")
check("inject confirm opens speed editor", ui.state == uimod.S_SPEED)
ui.inject("back")
check("inject back leaves speed editor", ui.state != uimod.S_SPEED)
prev_state = ui.state
ui.state = uimod.S_HOST
ui.inject("right")  # ignored while app owns the screen
check("inject ignored in host mode", ui.state == uimod.S_HOST)
ui.state = prev_state

# --- wheel paging across layers -------------------------------------------
# With wheel_layers on, a detent past the sixth tile lands on the next layer's
# first. The bug this guards: every detent called set_layer_idx, whose
# on_layer callback reset the selection to tile 0 AND repainted, so the grid
# visibly bounced through the first tile on its way ("2 -> 1 -> 3"). A detent
# must produce exactly one paint, showing the tile it is actually landing on.
_grid_calls = []
_orig_show_grid = ui.oled.show_grid


def _cap_show_grid(labels, active, *a, **k):
    _grid_calls.append(active)
    return _orig_show_grid(labels, active, *a, **k)


ui.oled.show_grid = _cap_show_grid
vapp.config["wheel_layers"] = True
vapp.config["layer_count"] = 3
ui.state = uimod.S_SELECT
vapp.set_layer_idx(0)
# This grid has a custom encoder slot, so navigation needs select mode on —
# and it must survive a layer crossing, or the next detent plays the macro.
ui.sel_mode = True

ui.sel_key = 1
_grid_calls.clear()
ui.enc.position += 1
ui.tick(_t2.monotonic())
check("a detent inside a layer paints once, on the new tile",
      _grid_calls == [2], "sel=%d paints=%s" % (ui.sel_key, _grid_calls))
check("a detent inside a layer does not change layer", vapp.layer == 0,
      "layer=%d" % vapp.layer)

ui.sel_key = 5
_grid_calls.clear()
ui.enc.position += 1
ui.tick(_t2.monotonic())
check("a detent past the last tile crosses into the next layer",
      vapp.layer == 1 and ui.sel_key == 0,
      "layer=%d sel=%d" % (vapp.layer, ui.sel_key))
check("crossing a layer still paints once, never the first tile twice",
      _grid_calls == [0], "paints=%s" % _grid_calls)
check("select mode survives a layer crossing", ui.sel_mode is True)

ui.sel_key = 0
_grid_calls.clear()
ui.enc.position -= 1
ui.tick(_t2.monotonic())
check("a detent before the first tile wraps back to the previous layer's last",
      vapp.layer == 0 and ui.sel_key == 5,
      "layer=%d sel=%d" % (vapp.layer, ui.sel_key))
check("wrapping backwards paints once", _grid_calls == [5],
      "paints=%s" % _grid_calls)

# The layer key / serial set_layer path must STILL reset to the first tile —
# only the wheel is exempt, and only while it is mid-detent.
ui.sel_key = 4
_grid_calls.clear()
vapp.set_layer_idx(2)
check("an outside layer change still resets the selection",
      ui.sel_key == 0 and _grid_calls == [0],
      "sel=%d paints=%s" % (ui.sel_key, _grid_calls))
check("_wheel_move does not leak past the detent", ui._wheel_move is False)

ui.oled.show_grid = _orig_show_grid
vapp.config["wheel_layers"] = False
vapp.set_layer_idx(0)
ui.sel_key = 0

voutbox.clear()
vapp.handle_msg({"t": "host_enter"})
check("host mode shows host screen", ui.state == uimod.S_HOST)
ui.enc.position += 3
ui.tick(_t2.monotonic())
check("host encoder event batched",
      any(m.get("t") == "enc" and m.get("d") == 1 and m.get("n") == 3 for m in voutbox),
      str(voutbox))
ui.nav.events.queue.append(FakeKeyEvent(1, True))
ui.tick(_t2.monotonic())
check("host nav slot event",
      any(m.get("t") == "btn" and m.get("slot") == "back" and m.get("down") for m in voutbox),
      str(voutbox))
vapp.handle_msg({"t": "host_leave"})
check("host exit restores grid", ui.state == uimod.S_SELECT)

# host-mode grid (proto v6): the app pushes the profile's key names in the
# label message; entering host mode (or a label change while in it) draws
# them as a grid — headless here, so the point is state + no crash
vapp.handle_msg({"t": "label", "text": "Photoshop",
                 "keys": ["Zoom in", "Zoom out", "Undo", "", "", ""]})
vapp.handle_msg({"t": "host_enter"})
check("host grid state", ui.state == uimod.S_HOST)
vapp.handle_msg({"t": "label", "text": "Photoshop",
                 "keys": ["A", "B", "C", "D", "E", "F"]})  # on_label redraw
check("host grid survives label update", ui.state == uimod.S_HOST)
vapp.handle_msg({"t": "label", "text": ""})  # back to plain host screen
check("host label cleared in host mode",
      vapp.host_label is None and vapp.host_keys is None)
vapp.handle_msg({"t": "host_leave"})
check("host grid exit restores grid", ui.state == uimod.S_SELECT)

# --- issue #19: btn-psh, slot key logic, per-context overrides ------------
# btn-psh is a grid slot: tap plays its macro (resolved from a queued
# release), holding it past ESC_HOLD_S is the guaranteed select-mode escape
with open(vapp.slot_path("btn-psh", 0), "w") as f:
    json.dump({"format": "mkyada-macro", "version": 2, "name": "mute",
               "kind": "media", "events": []}, f)
ui.invalidate_labels()
ui.state = uimod.S_SELECT
ui.sel_mode = False
vplays.clear()
ui.nav.events.queue.append(FakeKeyEvent(0, False))  # released -> tap
ui._dispatch(_t2.monotonic(), 0, uimod.K_PSH)
check("psh tap plays its macro", vplays == [vapp.slot_path("btn-psh", 0)],
      str(vplays))
vplays.clear()
ui._dispatch(_t2.monotonic(), 0, uimod.K_PSH)  # never released -> escape hold
check("psh hold escape toggles select mode", ui.sel_mode and vplays == [],
      "sel_mode=%s %s" % (ui.sel_mode, vplays))
ui._dispatch(_t2.monotonic(), 0, uimod.K_PSH)  # sel_mode: default PSH exits it
check("psh in select mode toggles back", not ui.sel_mode)

# an own hold variant beats the escape and drives BUILT-IN navigation
with open(vapp.slot_path("btn-psh", 0), "w") as f:
    json.dump({"format": "mkyada-macro", "version": 3, "name": "mute",
               "kind": "media", "events": [],
               "variants": {"hold": {"kind": "menu", "menu": "back",
                                     "events": []}}}, f)
ui.invalidate_labels()
ui.state = uimod.S_SELECT
ui.sel_mode = False
vplays.clear()
ui._dispatch(_t2.monotonic(), 0, uimod.K_PSH)  # held -> hold variant
check("psh hold variant = menu back goes home",
      ui.state == uimod.S_HOME and not ui.sel_mode and vplays == [],
      "state=%d" % ui.state)

# menu-kind tap on an encoder slot drives the built-in nav (no recursion)
with open(vapp.slot_path("enc-ccw", 0), "w") as f:
    json.dump({"format": "mkyada-macro", "version": 2, "kind": "menu",
               "menu": "left", "events": []}, f)
ui.invalidate_labels()
ui.state = uimod.S_SELECT
ui.sel_mode = False
ui.sel_key = 3
vplays.clear()
ui._dispatch(_t2.monotonic(), -1, None)
check("menu-kind enc slot drives built-in nav",
      ui.sel_key == 2 and vplays == [], "sel=%d %s" % (ui.sel_key, vplays))

# menu:"none" = the app's "Do nothing": the input is swallowed — no nav
# move, no playback (an off switch that overrides the built-in action)
with open(vapp.slot_path("enc-ccw", 0), "w") as f:
    json.dump({"format": "mkyada-macro", "version": 2, "kind": "menu",
               "menu": "none", "events": []}, f)
ui.invalidate_labels()
ui.state = uimod.S_SELECT
ui.sel_mode = False
ui.sel_key = 3
vplays.clear()
ui._dispatch(_t2.monotonic(), -1, None)
check("menu-none enc slot swallows the input",
      ui.sel_key == 3 and vplays == [], "sel=%d %s" % (ui.sel_key, vplays))
with open(vapp.slot_path("btn-back", 0), "w") as f:
    json.dump({"format": "mkyada-macro", "version": 2, "kind": "menu",
               "menu": "none", "events": []}, f)
ui.invalidate_labels()
ui._dispatch(_t2.monotonic(), 0, uimod.K_BACK)
check("menu-none BACK slot swallows the press",
      ui.state == uimod.S_SELECT and vplays == [], "state=%d" % ui.state)
os.remove(mpath("btn-back.json"))
ui.invalidate_labels()

# direct-jump menu actions (fw 0.12.0): "settings" opens the settings menu,
# "home" the layer screen — injected from a macro key or assigned to a slot
ui.state = uimod.S_SELECT
ui.inject("settings")
check("inject settings jumps to the settings menu",
      ui.state == uimod.S_SET_MENU, "state=%d" % ui.state)
ui.inject("home")
check("inject home jumps to the layer screen",
      ui.state == uimod.S_HOME and ui.home_pos == vapp.layer,
      "state=%d pos=%d" % (ui.state, ui.home_pos))
with open(vapp.slot_path("btn-confirm", 0), "w") as f:
    json.dump({"format": "mkyada-macro", "version": 2, "kind": "menu",
               "menu": "settings", "events": []}, f)
ui.invalidate_labels()
ui.state = uimod.S_SELECT
vplays.clear()
ui._dispatch(_t2.monotonic(), 0, uimod.K_CONFIRM)
check("menu-settings CONFIRM slot opens settings",
      ui.state == uimod.S_SET_MENU and vplays == [], "state=%d" % ui.state)
os.remove(mpath("btn-confirm.json"))
ui.invalidate_labels()
_lyr0 = vapp.layer
ui.inject("layer_next")
check("inject layer_next cycles the layer and shows the grid",
      vapp.layer == (_lyr0 + 1) % vapp.config["layer_count"]
      and ui.state == uimod.S_SELECT,
      "layer=%d state=%d" % (vapp.layer, ui.state))
ui.inject("layer_prev")
check("inject layer_prev returns", vapp.layer == _lyr0, str(vapp.layer))
ui.state = uimod.S_HOME
ui.inject("grid")
check("inject grid jumps to the key grid", ui.state == uimod.S_SELECT,
      "state=%d" % ui.state)
ui._enter_grid()

# --- context-aware wheel menu (issue: wheel-menu redesign) ----------------
# CONFIRM on the selected key opens a menu that fits the key's action kind,
# not always the speed editor. Each key1 rewrite below is re-read after
# invalidate_labels drops the (kind, sub) cache.
def _write_key1(obj):
    obj.setdefault("format", "mkyada-macro")
    obj.setdefault("version", 2)
    obj.setdefault("events", [])
    with open(vpath(1, 0), "w") as f:
        json.dump(obj, f)
    ui.invalidate_labels("/macros/key1.json")


def _confirm_key1():
    ui.state = uimod.S_SELECT
    ui.sel_mode = False
    ui.sel_key = 0
    vplays.clear()
    ui._dispatch(_t2.monotonic(), 0, uimod.K_CONFIRM)


# no kind (a plain recorded/stream macro) still opens the speed editor
_write_key1({"name": "macro", "stream": True, "settings": {"speed": 1.0}})
_confirm_key1()
check("ctx: kindless key opens speed editor", ui.state == uimod.S_SPEED,
      "state=%d" % ui.state)

# keystroke -> a "key" card (turn = turbo-fire, CONFIRM = fire once)
_write_key1({"name": "Undo", "kind": "keystroke", "combo": {"mods": [], "key": "z"}})
_confirm_key1()
check("ctx: keystroke opens an action card",
      ui.state == uimod.S_CTX and ui.ctx["mode"] == "key",
      "state=%d ctx=%s" % (ui.state, ui.ctx))
ui.enc.position += 2  # turn -> fire the key twice
vplays.clear()
ui.tick(_t2.monotonic())
check("ctx: keystroke card turbo-fires per detent",
      vplays == [vpath(1, 0)] * 2, str(vplays))

# media -> an options browser: cursor starts on the assigned usage; a tap
# fires the highlighted one, a hold reassigns the key to it (issue: grammar)
_write_key1({"name": "Vol+", "kind": "media", "media": "volume_up",
             "events": [{"delay": 0, "type": "consumer", "usage": "volume_up"}]})
_confirm_key1()
check("ctx: media opens an options browser",
      ui.state == uimod.S_CTX and ui.ctx["mode"] == "optlist"
      and ui.ctx["assigned"] == uimod.MEDIA_OPTS.index("volume_up"),
      "ctx=%s" % (ui.ctx,))
# tap the highlighted option -> fires it once (queue a release so it reads tap)
_creports = len(sent_reports)
ui.nav.events.queue.append(FakeKeyEvent(uimod.K_CONFIRM, True))
ui.nav.events.queue.append(FakeKeyEvent(uimod.K_CONFIRM, False))
ui.tick(_t2.monotonic())
check("ctx: media tap fires the highlighted key",
      len(sent_reports) > _creports, "reports+%d" % (len(sent_reports) - _creports))
# hold on a different option -> reassigns the key (device writes the macro)
ui.ctx["sel"] = uimod.MEDIA_OPTS.index("play_pause")
ui.nav.events.queue.append(FakeKeyEvent(uimod.K_CONFIRM, True))  # never released -> hold
ui.tick(_t2.monotonic())
with open(vpath(1, 0)) as f:
    _reassigned = json.load(f)
check("ctx: media hold reassigns the key",
      _reassigned.get("kind") == "media" and _reassigned.get("media") == "play_pause",
      str(_reassigned))

# midi -> the same browser over all 128 notes. The parts the picker does NOT
# edit (channel, velocity, note mode) have to survive a reassign, which is why
# it reads the payload from the file rather than the label cache.
_write_key1({"name": "Note C3 (ch 10)", "kind": "midi", "version": 3,
             "icon": "note", "settings": {"speed": 2.0},
             "midi": {"msg": "note", "ch": 9, "d1": 60, "d2": 111,
                      "mode": "momentary"},
             "events": [
                 {"delay": 0, "type": "midi", "m": "note_on", "ch": 9,
                  "d1": 60, "d2": 111},
                 {"delay": 20, "type": "midi", "m": "note_off", "ch": 9,
                  "d1": 60}]})
_confirm_key1()
check("ctx: midi opens a note browser on the assigned note",
      ui.state == uimod.S_CTX and ui.ctx["mode"] == "optlist"
      and ui.ctx["kind"] == "midi_note" and ui.ctx["assigned"] == 60
      and len(ui.ctx["opts"]) == 128, "ctx=%s" % (ui.ctx.get("kind"),))
check("ctx: midi labels notes the way DAWs print them",
      uimod.note_name(60) == "C3" and uimod.note_name(0) == "C-2"
      and uimod.note_name(127) == "G8", uimod.note_name(60))
# tap auditions the highlighted note as a real on/off pair — a bare note-on
# would hang until something else cleaned it up
ui.ctx["sel"] = 64
sent_midi.clear()
ui.nav.events.queue.append(FakeKeyEvent(uimod.K_CONFIRM, True))
ui.nav.events.queue.append(FakeKeyEvent(uimod.K_CONFIRM, False))
ui.tick(_t2.monotonic())
check("ctx: midi tap auditions the highlighted note",
      sent_midi == [b"\x99\x40\x6f", b"\x89\x40\x00"], str(sent_midi))
# hold reassigns, keeping channel, velocity and mode
ui.ctx["sel"] = 67
ui.nav.events.queue.append(FakeKeyEvent(uimod.K_CONFIRM, True))  # held -> assign
ui.tick(_t2.monotonic())
with open(vpath(1, 0)) as f:
    _remidi = json.load(f)
check("ctx: midi hold reassigns the note",
      _remidi.get("kind") == "midi" and _remidi["midi"]["d1"] == 67
      and _remidi["events"][0]["d1"] == 67, str(_remidi))
check("ctx: midi reassign keeps channel, velocity and mode",
      _remidi["midi"]["ch"] == 9 and _remidi["midi"]["d2"] == 111
      and _remidi["midi"]["mode"] == "momentary", str(_remidi.get("midi")))
check("ctx: midi reassign names the key exactly as the app would",
      _remidi.get("name") == "Note G3 (ch 10)", str(_remidi.get("name")))
check("ctx: midi reassign keeps the icon and variants the app set",
      _remidi.get("icon") == "note" and _remidi.get("version") == 3,
      str({k: _remidi.get(k) for k in ("icon", "version")}))
# a fast spin must cover ground: a tick can carry several detents, and one
# step per tick put the far end of a 128-note list out of reach
ui._enter_grid()
_confirm_key1()
ui.ctx["sel"] = 60
ui.last_move = _t2.monotonic() - 1.0
ui.enc.position += 4          # four detents coalesced into one tick
ui.tick(_t2.monotonic())
check("ctx: a fast spin moves further than one note",
      ui.ctx["sel"] > 63, "sel=%d" % ui.ctx["sel"])
# short lists stay one-per-detent so a nine-item browser cannot overshoot
_write_key1({"name": "Vol+", "kind": "media", "media": "volume_up",
             "events": [{"delay": 0, "type": "consumer", "usage": "volume_up"}]})
ui._enter_grid()
_confirm_key1()
_msel = ui.ctx["sel"]
ui.last_move = _t2.monotonic() - 1.0
ui.enc.position += 1
ui.tick(_t2.monotonic())
check("ctx: a short browser still steps one per detent",
      ui.ctx["sel"] == min(_msel + 1, len(ui.ctx["opts"]) - 1),
      "sel=%d from %d" % (ui.ctx["sel"], _msel))

# a bare key press still plays it — the browser is the PSH/CONFIRM gesture
ui._enter_grid()
check("press: a midi key still runs (no press-menu)",
      ui.wants_press_menu(1) is False)

# discoverability: the browser's bottom bar must advertise hold-to-reassign,
# otherwise a first-timer never learns the gesture (issue: hold hint on screen)
_menu_kw = {}
_orig_show_menu = ui.oled.show_menu
def _cap_show_menu(*a, **k):
    _menu_kw.clear()
    _menu_kw.update(k)
    return _orig_show_menu(*a, **k)
ui.oled.show_menu = _cap_show_menu
_write_key1({"name": "Vol+", "kind": "media", "media": "volume_up",
             "events": [{"delay": 0, "type": "consumer", "usage": "volume_up"}]})
_confirm_key1()
ui._draw_optlist()
check("ctx: media browser shows the hold-to-reassign hint",
      bool(_menu_kw.get("hold")), str(_menu_kw))

# menu (layer / nav) key: the wheel browses the whole family, taps run the
# highlighted one live and holds reassign — not just "run next layer" forever
# (issue: layer keys only ran next layer, no prev/goto/reassign)
vapp.config["layer_count"] = 2
_write_key1({"name": "Layer+", "kind": "menu", "menu": "layer_next"})
_confirm_key1()
check("ctx: menu opens the layer browser",
      ui.state == uimod.S_CTX and ui.ctx.get("mode") == "optlist"
      and ui.ctx.get("kind") == "menu"
      and ui.ctx["opts"][ui.ctx["assigned"]] == "layer_next",
      "ctx=%s" % (ui.ctx,))
check("ctx: layer browser shows the hold-to-reassign hint",
      bool(_menu_kw.get("hold")), str(_menu_kw))
# turn to "layer_prev" and hold -> the device rewrites the key standalone
ui.ctx["sel"] = ui.ctx["opts"].index("layer_prev")
ui.nav.events.queue.append(FakeKeyEvent(uimod.K_CONFIRM, True))  # never released
ui.tick(_t2.monotonic())
with open(vpath(1, 0)) as f:
    _mre = json.load(f)
check("ctx: menu hold reassigns the key to prev layer",
      _mre.get("kind") == "menu" and _mre.get("menu") == "layer_prev", str(_mre))
# a tap on a layer action runs it live and leaves the wheel menu
_write_key1({"name": "Layer+", "kind": "menu", "menu": "layer_next"})
_confirm_key1()
_lyr_before = vapp.layer
ui.ctx["sel"] = ui.ctx["opts"].index("layer_next")
ui.nav.events.queue.append(FakeKeyEvent(uimod.K_CONFIRM, True))
ui.nav.events.queue.append(FakeKeyEvent(uimod.K_CONFIRM, False))  # release -> tap
ui.tick(_t2.monotonic())
check("ctx: menu tap runs the layer action and leaves the menu",
      ui.state != uimod.S_CTX and vapp.layer == (_lyr_before + 1) % 2,
      "state=%d layer=%d" % (ui.state, vapp.layer))
vapp.set_layer_idx(0)  # the tap switched layers; restore for the tests below
vapp.config["layer_count"] = 1  # restore the single-layer vision6 fixture
ui.invalidate_labels("/macros/key1.json")

# a host-only kind (OBS) with no app menu support -> the app-needed toast
vapp.host_menus = False
_write_key1({"name": "Scene", "kind": "obs", "obs": {"action": "setScene"}})
_confirm_key1()
check("ctx: host kind shows the app-needed toast", ui.state == uimod.S_TOAST,
      "state=%d" % ui.state)

# with the app advertising menu support (hostinfo): CONFIRM asks the app for a
# menu (ctx message) and shows a waiting card until the app answers
vapp.handle_msg({"t": "hostinfo", "menus": 1})
check("ctx: hostinfo sets host_menus", vapp.host_menus is True)
voutbox.clear()
_confirm_key1()
_ctxmsg = next((m for m in voutbox if m.get("t") == "ctx"), None)
check("ctx: host kind asks the app (ctx message)",
      _ctxmsg is not None and _ctxmsg.get("kind") == "obs"
      and _ctxmsg.get("sub") == "setScene" and _ctxmsg.get("key") == 1,
      str(_ctxmsg))
check("ctx: host kind waits for the menu",
      ui.state == uimod.S_CTX and ui.ctx["mode"] == "wait", "ctx=%s" % (ui.ctx,))

# the app answers with a list menu (scene picker) -> rendered, cursor navigable
ui.on_menu({"t": "menu", "mtype": "list", "key": 1, "title": "SCENE",
            "items": [["Intro", "Intro", 0], ["Game", "Game", 1]], "sel": 1})
check("ctx: menu switches to host list", ui.ctx["mode"] == "host"
      and ui.ctx["mtype"] == "list" and ui.ctx["sel"] == 1, "ctx=%s" % (ui.ctx,))
# a plain host list (no hold flag) shows no reassign hint...
_menu_kw.clear()
ui._draw_host_menu()
check("ctx: host list without hold flag has no reassign hint",
      not _menu_kw.get("hold"), str(_menu_kw))
# ...but when the app marks the menu reassignable (OBS scene / mic mode), the
# device shows the hold-to-reassign affordance so the gesture is discoverable
ui.on_menu({"t": "menu", "mtype": "list", "key": 1, "title": "SCENE",
            "items": [["Intro", "Intro", 0], ["Game", "Game", 1]], "sel": 1,
            "hold": True})
_menu_kw.clear()
ui._draw_host_menu()
check("ctx: reassignable host list shows the hold hint",
      bool(_menu_kw.get("hold")), str(_menu_kw))
ui.oled.show_menu = _orig_show_menu
voutbox.clear()
ui.enc.position -= 1  # turn up -> select the first scene
ui.tick(_t2.monotonic())
check("ctx: list turn moves the cursor", ui.ctx["sel"] == 0, "sel=%d" % ui.ctx["sel"])
# a tap on a list item = "pick" (use it live); a hold = "assign" (reassign)
ui.nav.events.queue.append(FakeKeyEvent(uimod.K_CONFIRM, True))
ui.nav.events.queue.append(FakeKeyEvent(uimod.K_CONFIRM, False))
ui.tick(_t2.monotonic())
_pick = next((m for m in voutbox if m.get("t") == "menu_ev"), None)
check("ctx: list tap picks the item (live)",
      _pick is not None and _pick.get("ev") == "pick" and _pick.get("id") == "Intro",
      str(_pick))
voutbox.clear()
ui.nav.events.queue.append(FakeKeyEvent(uimod.K_CONFIRM, True))  # held -> assign
ui.tick(_t2.monotonic())
_assign = next((m for m in voutbox if m.get("t") == "menu_ev"), None)
check("ctx: list hold reassigns the item",
      _assign is not None and _assign.get("ev") == "assign" and _assign.get("id") == "Intro",
      str(_assign))

# the app answers menu_result -> the menu closes with a toast
ui.on_menu_result({"t": "menu_result", "ok": True, "toast": ["SCENE", "Saved"]})
check("ctx: menu_result closes to a toast", ui.state == uimod.S_TOAST)

# a status card: CONFIRM sends a "fire" event, the app performs the action
ui._enter_grid()
ui.state = uimod.S_SELECT
vapp.host_menus = True
_write_key1({"name": "Rec", "kind": "obs", "obs": {"action": "recordToggle"}})
_confirm_key1()
ui.on_menu({"t": "menu", "mtype": "card", "key": 1, "title": "RECORD",
            "big": "REC", "l1": "ready", "hint": "toggle"})
check("ctx: card menu renders", ui.ctx["mtype"] == "card")
voutbox.clear()
ui.nav.events.queue.append(FakeKeyEvent(uimod.K_CONFIRM, True))
ui.tick(_t2.monotonic())
_fire = next((m for m in voutbox if m.get("t") == "menu_ev"), None)
check("ctx: card CONFIRM fires", _fire is not None and _fire.get("ev") == "fire",
      str(_fire))

# mtype "obs" (proto v11): a live status screen rather than a chooser. The app
# re-pushes it while the recorder runs; the device owns the blink so the dot
# keeps its rhythm even when a push is late.
_obs = {"t": "menu", "mtype": "obs", "key": 1, "title": "OBS", "obsview": "rec",
        "rec": True, "live": False, "mic": 60, "time": "00:12", "scene": "Intro",
        "hint": "stop"}
ui.on_menu(dict(_obs))
check("ctx: obs menu renders", ui.ctx["mtype"] == "obs" and ui.ctx["rec"],
      str(ui.ctx.get("mtype")))
check("ctx: obs record dot starts lit", ui._blink_on is True)
check("ctx: obs carries the view", ui.ctx["obsview"] == "rec")
_ob = _t2.monotonic()
ui.tick(_ob + 0.7)   # no input: only the blink moves
check("ctx: obs blinks on the device's own clock", ui._blink_on is False)
check("ctx: obs blink does not close the menu", ui.state == uimod.S_CTX)
voutbox.clear()
ui.nav.events.queue.append(FakeKeyEvent(uimod.K_CONFIRM, True))
ui.tick(_t2.monotonic())
_fire = next((m for m in voutbox if m.get("t") == "menu_ev"), None)
check("ctx: obs CONFIRM fires the action",
      _fire is not None and _fire.get("ev") == "fire", str(_fire))
# "main" is the full status screen, "rec" the recorder card — both must draw
ui.on_menu(dict(_obs, obsview="main", rec=False, live=True))
check("ctx: obs main view renders",
      ui.ctx["obsview"] == "main" and ui.ctx["live"] and not ui.ctx["rec"])

# the app going away abandons an open host menu
ui.on_menu({"t": "menu", "mtype": "card", "key": 1, "title": "RECORD", "big": "REC"})
ui.on_host_gone()
check("ctx: host disconnect closes the menu", ui.state == uimod.S_SELECT)

# volume kind: app present -> host slider (ctx asked); app absent -> a local
# HID volume knob card (press mutes)
ui.state = uimod.S_SELECT
vapp.host_menus = True
_write_key1({"name": "Vol", "kind": "volume",
             "events": [{"delay": 0, "type": "consumer", "usage": "mute"}]})
voutbox.clear()
_confirm_key1()
check("ctx: volume with app asks for a host slider",
      any(m.get("t") == "ctx" and m.get("kind") == "volume" for m in voutbox)
      and ui.ctx["mode"] == "wait", "ctx=%s" % (ui.ctx,))
vapp.host_menus = False
_confirm_key1()
check("ctx: volume without app falls back to a local knob",
      ui.state == uimod.S_CTX and ui.ctx["mode"] == "adjust"
      and ui.ctx["conf"] == "mute", "ctx=%s" % (ui.ctx,))

# a volume key opens its wheel menu when the PHYSICAL key is pressed (acts as
# PSH) — a slider kind has no useful "run"
_write_key1({"name": "Vol", "kind": "volume",
             "events": [{"delay": 0, "type": "consumer", "usage": "mute"}]})
ui._enter_grid()
check("press: volume key wants the menu on press", ui.wants_press_menu(1) is True)
ui.open_key_menu(1)
check("press: pressing a volume key opens its menu",
      ui.state == uimod.S_CTX and ui.ctx["mode"] == "adjust", "state=%d" % ui.state)
_write_key1({"name": "Play", "kind": "media", "media": "play_pause",
             "events": [{"delay": 0, "type": "consumer", "usage": "play_pause"}]})
ui._enter_grid()
check("press: a media key still runs (no press-menu)", ui.wants_press_menu(1) is False)

# live system volume shows on volume-kind grid cells (app pushes sysvol)
_write_key1({"name": "Vol", "kind": "volume",
             "events": [{"delay": 0, "type": "consumer", "usage": "mute"}]})
ui._enter_grid()
ui.on_sysvol(40)
check("sysvol: stored", ui.sysvol == 40)
_gl = ui._grid_labels(0)
check("sysvol: volume cell shows the percent", _gl[0][1] == "%40", str(_gl[0]))
ui.on_host_gone()
check("sysvol: cleared when the app disconnects", ui.sysvol is None)

# mic level is host-only: pressing asks the app for a slider
vapp.host_menus = True
_write_key1({"name": "MicLvl", "kind": "mic_level", "events": []})
ui._enter_grid()
voutbox.clear()
ui.open_key_menu(1)
check("ctx: mic_level asks the app for a slider",
      any(m.get("t") == "ctx" and m.get("kind") == "mic_level" for m in voutbox)
      and ui.ctx["mode"] == "wait", "ctx=%s" % (ui.ctx,))
vapp.host_menus = False

# --- Dial module (kind enc_module, proto v15) ------------------------------
# A device-native encoder toolset: the key's file carries six slots, a bare
# press opens the module, the six keys select slots, and the wheel drives the
# selected one as plain HID. Fully standalone — the ctx is only an announce.
_dial = {
    "name": "DaVinci", "kind": "enc_module",
    "enc_module": {"slots": [
        {"l": "JOG", "t": "keys",
         "cw": {"mods": [], "key": "right"}, "ccw": {"mods": [], "key": "left"},
         "m": 1, "b": {"t": "combo", "mods": [], "key": "space"}},
        {"l": "ZOOM", "t": "scroll", "axis": "v", "mods": ["cmd"], "m": 1},
        {"l": "WHEEL", "t": "move", "axis": "y", "step": 4, "drag": True,
         "m": 1, "b": {"t": "click"}},
        {"l": "VOL", "t": "consumer", "cw": "volume_up", "ccw": "volume_down",
         "m": 1, "b": {"t": "consumer", "u": "play_pause"}},
        None, None]}}
_write_key1(dict(_dial))
ui._enter_grid()
check("dial: a bare key press opens the module", ui.wants_press_menu(1) is True)
voutbox.clear()
ui.open_key_menu(1)
check("dial: module opens with the first slot selected",
      ui.state == uimod.S_CTX and ui.ctx["mode"] == "encmod"
      and ui.ctx["sel"] == 0, "ctx=%s" % (ui.ctx,))
check("dial: announced to the app as a plain ctx",
      any(m.get("t") == "ctx" and m.get("kind") == "enc_module"
          for m in voutbox), str(voutbox))
check("dial: keypad belongs to the module",
      ui.enc_module_active() and vapp.enc_module_active())

# a stray menu reply (an OLD app answering the announce) must not clobber it
ui.on_menu({"t": "menu", "mtype": "card", "key": 1, "title": "WHEEL", "big": "X"})
check("dial: a stray app menu is ignored", ui.ctx.get("mode") == "encmod")

# key edges route to slot selection — the local macro must NOT play
_kmap = vapp.config["key_map"]
vplays.clear()
vapp.on_edge(_kmap.index(4), True)
vapp.on_edge(_kmap.index(4), False)
check("dial: a key press selects that slot, plays nothing",
      ui.ctx["sel"] == 3 and vplays == [], "sel=%s plays=%s"
      % (ui.ctx["sel"], vplays))
vapp.on_edge(_kmap.index(5), True)  # empty slot: a dead key
check("dial: an empty slot's key is dead", ui.ctx["sel"] == 3)

# keys slot: one detent -> one tap of the combo (velocity accel forced off)
vapp.on_edge(_kmap.index(1), True)
_dnow = _t2.monotonic()
ui.last_move = _dnow - 1.0
sent_reports.clear()
ui.enc.position += 1
ui.tick(_dnow)
_dial_kbd = [r[2] for r in sent_reports if r[1] == 0x06]
check("dial: jog detent taps the cw combo once",
      sum(1 for r in _dial_kbd if r[2] == 0x4F) == 1, str(_dial_kbd))
# encoder button -> the slot's own action (space)
sent_reports.clear()
ui.nav.events.queue.append(FakeKeyEvent(uimod.K_CONFIRM, True))
ui.nav.events.queue.append(FakeKeyEvent(uimod.K_CONFIRM, False))
ui.tick(_t2.monotonic())
_dial_kbd = [r[2] for r in sent_reports if r[1] == 0x06]
check("dial: wheel press fires the slot's button action",
      any(r[2] == 0x2C for r in _dial_kbd), str(_dial_kbd))

# scroll slot: modifiers held around the wheel ticks (cmd+scroll zoom)
vapp.on_edge(_kmap.index(2), True)
_dnow = _t2.monotonic()
ui.last_move = _dnow - 1.0
sent_reports.clear()
ui.enc.position += 1
ui.tick(_dnow)
_dial_wheel = [struct.unpack("<bb", r[2]) for r in sent_reports
               if r[1] == 0x02 and len(r[2]) == 2]
_dial_kbd = [r[2] for r in sent_reports if r[1] == 0x06]
check("dial: zoom detent scrolls once with cmd held",
      [m[0] for m in _dial_wheel] == [1]
      and _dial_kbd and _dial_kbd[0][0] == 0x08
      and _dial_kbd[-1][0] == 0x00,
      "wheel=%s kbd=%s" % (_dial_wheel, _dial_kbd))

# move slot: rel pointer drag — button down rides the turn, released after
# the gesture window with the cursor untouched
vapp.on_edge(_kmap.index(3), True)
_dnow = _t2.monotonic()
ui.last_move = _dnow - 1.0
sent_reports.clear()
ui.enc.position += 1
ui.tick(_dnow)
_dial_rel = [struct.unpack("<Bbb", r[2]) for r in sent_reports
             if r[1] == 0x02 and len(r[2]) == 3]
check("dial: drag detent holds the button and nudges the cursor",
      _dial_rel == [(1, 0, 0), (1, 0, 4)], str(_dial_rel))
sent_reports.clear()
ui.tick(_dnow + 0.5)  # past DRAG_RELEASE_S with no detent
_dial_rel = [struct.unpack("<Bbb", r[2]) for r in sent_reports
             if r[1] == 0x02 and len(r[2]) == 3]
check("dial: the drag releases after the gesture window",
      _dial_rel == [(0, 0, 0)], str(_dial_rel))
# switching slots mid-drag releases too (must not leak across slots)
ui.enc.position += 1
ui.tick(_t2.monotonic())
sent_reports.clear()
vapp.on_edge(_kmap.index(4), True)
_dial_rel = [struct.unpack("<Bbb", r[2]) for r in sent_reports
             if r[1] == 0x02 and len(r[2]) == 3]
check("dial: switching slots drops a held drag",
      _dial_rel == [(0, 0, 0)] and ui.ctx["sel"] == 3, str(_dial_rel))

# consumer slot: turn down -> volume_down taps
_dnow = _t2.monotonic()
ui.last_move = _dnow - 1.0
sent_reports.clear()
ui.enc.position -= 1
ui.tick(_dnow)
_dial_cons = [struct.unpack("<H", r[2])[0] for r in sent_reports if r[0] == 0x0C]
check("dial: volume slot turns the volume down",
      0xEA in _dial_cons, str(_dial_cons))

# no idle timeout: a color session parks on the module for minutes
ui.activity_at = _t2.monotonic() - ui.idle_secs - 30
ui.tick(_t2.monotonic())
check("dial: the module never times out", ui.state == uimod.S_CTX
      and ui.ctx.get("mode") == "encmod", "state=%d" % ui.state)

# BACK closes: drag dropped, app told, keypad back to the grid
voutbox.clear()
ui.nav.events.queue.append(FakeKeyEvent(uimod.K_BACK, True))
ui.nav.events.queue.append(FakeKeyEvent(uimod.K_BACK, False))
ui.tick(_t2.monotonic())
check("dial: BACK returns to the grid", ui.state == uimod.S_SELECT
      and not ui.enc_module_active(), "state=%d" % ui.state)

# --- Dial midi_cc slots (proto v16) ----------------------------------------
# One slot per encoding. The relative ones send a DELTA so the DAW's value is
# the only one that matters; absolute counts on the device and can jump.
_write_key1({
    "name": "Mixer", "kind": "enc_module",
    "enc_module": {"slots": [
        {"l": "2C", "t": "midi_cc", "cc": 74, "ch": 0, "mode": "rel_2c", "m": 1},
        {"l": "BIN", "t": "midi_cc", "cc": 74, "ch": 0, "mode": "rel_bin", "m": 1},
        {"l": "SM", "t": "midi_cc", "cc": 74, "ch": 0, "mode": "rel_sm", "m": 1},
        {"l": "MCU", "t": "midi_cc", "cc": 74, "ch": 0, "mode": "rel_mackie", "m": 1},
        {"l": "ABS", "t": "midi_cc", "cc": 74, "ch": 0, "mode": "abs", "m": 1},
        None]}})
ui._enter_grid()
ui.open_key_menu(1)
check("dial: a midi_cc module opens",
      ui.state == uimod.S_CTX and ui.ctx["mode"] == "encmod", "ctx=%s" % (ui.ctx,))


def _dial_turn(key_no, delta):
    """Select a slot, turn one detent, return the MIDI bytes it sent."""
    vapp.on_edge(_kmap.index(key_no), True)
    now = _t2.monotonic()
    ui.last_move = now - 1.0   # slow detent: no velocity acceleration
    sent_midi.clear()
    ui.enc.position += delta
    ui.tick(now)
    return list(sent_midi)


check("dial midi: two's complement counts up 1..63",
      _dial_turn(1, 1) == [b"\xb0\x4a\x01"], str(sent_midi))
check("dial midi: two's complement counts down from 127",
      _dial_turn(1, -1) == [b"\xb0\x4a\x7f"], str(sent_midi))
check("dial midi: binary offset centres on 64",
      _dial_turn(2, 1) == [b"\xb0\x4a\x41"]
      and _dial_turn(2, -1) == [b"\xb0\x4a\x3f"], str(sent_midi))
check("dial midi: sign magnitude puts the sign in bit 6",
      _dial_turn(3, 1) == [b"\xb0\x4a\x01"]
      and _dial_turn(3, -1) == [b"\xb0\x4a\x41"], str(sent_midi))
check("dial midi: mackie matches sign magnitude",
      _dial_turn(4, 1) == [b"\xb0\x4a\x01"]
      and _dial_turn(4, -1) == [b"\xb0\x4a\x41"], str(sent_midi))
# absolute walks a value the device owns, starting from the mid point
check("dial midi: absolute walks up from 64", _dial_turn(5, 1) == [b"\xb0\x4a\x41"],
      str(sent_midi))
check("dial midi: absolute keeps its place", _dial_turn(5, 1) == [b"\xb0\x4a\x42"],
      str(sent_midi))
# the absolute value lives in the ctx, so closing the module forgets it — the
# parsed slot dict is thrown away and must never be written back to
ui.nav.events.queue.append(FakeKeyEvent(uimod.K_BACK, True))
ui.nav.events.queue.append(FakeKeyEvent(uimod.K_BACK, False))
ui.tick(_t2.monotonic())
ui.open_key_menu(1)
check("dial midi: absolute resets when the module reopens",
      _dial_turn(5, 1) == [b"\xb0\x4a\x41"], str(sent_midi))
ui.nav.events.queue.append(FakeKeyEvent(uimod.K_BACK, True))
ui.nav.events.queue.append(FakeKeyEvent(uimod.K_BACK, False))
ui.tick(_t2.monotonic())
check("dial: closing tells the app (menu_ev close)",
      any(m.get("t") == "menu_ev" and m.get("ev") == "close" for m in voutbox),
      str(voutbox))

# move slot with gesture modifiers (Ctrl+Opt+drag = Photoshop brush scrub):
# mods go down BEFORE the button, ride the whole gesture, and the release
# drops the button first, then the mods — the host never sees a bare drag
_write_key1({"name": "PS", "kind": "enc_module",
             "enc_module": {"slots": [
                 {"l": "BRUSH", "t": "move", "axis": "x", "step": 3,
                  "drag": True, "mods": ["CTRL", "ALT"], "m": 1},
                 None, None, None, None, None]}})
ui._enter_grid()
ui.open_key_menu(1)
_dnow = _t2.monotonic()
ui.last_move = _dnow - 1.0
sent_reports.clear()
ui.enc.position += 1
ui.tick(_dnow)
_kbd_i = next((i for i, r in enumerate(sent_reports) if r[1] == 0x06), None)
_btn_i = next((i for i, r in enumerate(sent_reports)
               if r[1] == 0x02 and len(r[2]) == 3), None)
check("dial: gesture mods go down before the drag button",
      _kbd_i is not None and _btn_i is not None and _kbd_i < _btn_i
      and sent_reports[_kbd_i][2][0] == 0x05,
      str([(r[1], bytes(r[2])) for r in sent_reports]))
sent_reports.clear()
ui.tick(_dnow + 0.5)  # inside the LONGER modded-gesture window: still held
check("dial: modded gesture outlives the plain-drag window",
      not sent_reports and vapp.engine.rel_buttons, str(sent_reports))
ui.tick(_dnow + 1.0)  # past MOD_DRAG_RELEASE_S
_btn_i = next((i for i, r in enumerate(sent_reports)
               if r[1] == 0x02 and len(r[2]) == 3), None)
_kbd_i = next((i for i, r in enumerate(sent_reports) if r[1] == 0x06), None)
check("dial: release drops the button first, then the mods",
      _btn_i is not None and _kbd_i is not None and _btn_i < _kbd_i
      and sent_reports[_kbd_i][2][0] == 0x00,
      str([(r[1], bytes(r[2])) for r in sent_reports]))
check("dial: no modifier left behind", vapp.engine.mods == 0)
ui.nav.events.queue.append(FakeKeyEvent(uimod.K_BACK, True))
ui.nav.events.queue.append(FakeKeyEvent(uimod.K_BACK, False))
ui.tick(_t2.monotonic())

# an all-empty module toasts instead of opening a dead screen
_write_key1({"name": "Empty", "kind": "enc_module",
             "enc_module": {"slots": [None] * 6}})
ui._enter_grid()
ui.open_key_menu(1)
check("dial: an empty module shows a toast", ui.state == uimod.S_TOAST,
      "state=%d" % ui.state)

# restore key1 to its original stream file for any later expectations
with open(vpath(1, 0), "w") as f:
    f.write(json.dumps({"format": "mkyada-macro", "version": 4, "stream": True,
                        "name": "volume up", "settings": {"speed": 3.0}}) + "\n")
    f.write(json.dumps({"delay": 0, "type": "key", "action": "down", "key": "a"}) + "\n")
    f.write(json.dumps({"delay": 0, "type": "key", "action": "up", "key": "a"}) + "\n")
ui.invalidate_labels("/macros/key1.json")
ui._enter_grid()

# per-context overrides: enc-cw@home plays on the layer picker; the other
# direction of a half-assigned wheel is dead; unassigned BACK stays default
vapp.slot_ctx_path = lambda s, c: mpath("%s@%s.json" % (s, c))
with open(vapp.slot_ctx_path("enc-cw", "home"), "w") as f:
    json.dump({"format": "mkyada-macro", "version": 2, "name": "vol+",
               "events": []}, f)
ui._ctx_slots.clear()
ui.state = uimod.S_HOME
ui.home_pos = 0
vplays.clear()
ui._dispatch(_t2.monotonic(), 1, None)
check("home ctx encoder override plays",
      vplays == [vapp.slot_ctx_path("enc-cw", "home")], str(vplays))
vplays.clear()
ui._dispatch(_t2.monotonic(), -1, None)
check("half-assigned home wheel other direction is dead",
      vplays == [] and ui.home_pos == 0, "pos=%d %s" % (ui.home_pos, vplays))
ui._dispatch(_t2.monotonic(), 0, uimod.K_BACK)
check("home ctx unassigned BACK keeps default", ui.state == uimod.S_SELECT)
ui.invalidate_labels("/macros/enc-cw@home.json")
check("ctx invalidate drops the context cache", "home" not in ui._ctx_slots)

# select mode entered on the grid keeps default nav inside home too
ui.state = uimod.S_HOME
ui.sel_mode = True
ui.home_pos = 0
vplays.clear()
ui._ctx_slots.clear()
ui._dispatch(_t2.monotonic(), 1, None)
check("select mode overrides home ctx customs",
      vplays == [] and ui.home_pos == 1, "pos=%d %s" % (ui.home_pos, vplays))
ui.sel_mode = False
ui._enter_grid()

# cleanup: drop the issue-19 slot files so earlier expectations stay valid
for _f in ("btn-psh.json", "enc-ccw.json", "enc-cw@home.json"):
    try:
        os.remove(mpath(_f))
    except OSError:
        pass
ui.invalidate_labels()
ui._ctx_slots.clear()

# --- language (config "lang", i18n tables) --------------------------------
from mkyada import i18n as i18nmod  # noqa: E402

check("lang default en", vapp.config["lang"] == "en", str(vapp.config.get("lang")))
_b.open = _cfg_open({"model": "vision6", "lang": "tr"})
vapp.load_config()
check("lang tr accepted", vapp.config["lang"] == "tr")
_b.open = _cfg_open({"model": "vision6", "lang": "xx"})
vapp.load_config()
check("lang invalid -> en", vapp.config["lang"] == "en")
_b.open = _real_open
i18nmod.set_lang("tr")
check("i18n tr strings", i18nmod.tr("settings") == "AYARLAR"
      and i18nmod.tr("restart") == "Yeniden Başlat")
# The Turkish table used to be ASCII-folded because the bundled BDF fonts had
# no Turkish glyphs. It is real Turkish now, so the invariant flips: every
# character of every string must be one the shipped font actually DRAWS —
# reaching font.py's fold table would mean a letter silently degrades.
_f = _Font(os.path.join(FFW, "fonts", "mkyada.fnt"))
_missing = sorted({ch for tbl in i18nmod.STRINGS.values() for v in tbl.values()
                   for ch in v
                   if not (_f.first <= ord(ch) <= _f.last or ord(ch) in _f.extra)}
                  | {ch for d in i18nmod.LANG_DESC for ch in d
                     if not (_f.first <= ord(ch) <= _f.last or ord(ch) in _f.extra)})
check("every UI string is drawable by the shipped font", not _missing, str(_missing))
# str.upper() is locale-blind, so the device drew "SERI" where Turkish spells
# it "SERİ". i18n.upper() handles the dotted/dotless pair; every screen that
# uppercases goes through it.
i18nmod.set_lang("tr")
check("tr upper dots the i", i18nmod.upper("seri") == "SERİ",
      i18nmod.upper("seri"))
check("tr upper leaves the dotless one alone", i18nmod.upper("hız") == "HIZ",
      i18nmod.upper("hız"))
check("tr upper on a real string", i18nmod.upper(i18nmod.tr("language")) == "DİL",
      i18nmod.upper(i18nmod.tr("language")))
i18nmod.set_lang("en")
check("en upper is unchanged", i18nmod.upper("serial") == "SERIAL",
      i18nmod.upper("serial"))
# Uppercasing must never introduce a character the font cannot draw.
_upper_missing = sorted({ch for lang in i18nmod.LANGS
                         for _ in [i18nmod.set_lang(lang)]
                         for v in i18nmod.STRINGS[lang].values()
                         for ch in i18nmod.upper(v)
                         if not (_f.first <= ord(ch) <= _f.last or ord(ch) in _f.extra)})
check("every uppercased UI string is drawable too", not _upper_missing,
      str(_upper_missing))
i18nmod.set_lang("en")
check("i18n back to en", i18nmod.tr("settings") == "SETTINGS")
check("i18n unknown key echoes", i18nmod.tr("nope-key") == "nope-key")

# settings menu: localized items incl. Language and the band toggles
# Rows are (label, kind, value) now: the redesigned screen has a value
# column, so a toggle's state is a switch instead of ": on" glued to the label,
# and Language finally shows which language is selected.
_items = ui._set_items()
check("set menu has language", _items[uimod.SET_LANG][0] == "Language")
check("set menu language shows the value",
      _items[uimod.SET_LANG][1] == "text" and _items[uimod.SET_LANG][2] in
      i18nmod.LANG_DESC, str(_items[uimod.SET_LANG]))
check("set menu band toggles carry state, not label text",
      _items[uimod.SET_BAND_LAYER] == ("Layer band", "toggle", False)
      and _items[uimod.SET_BAND_PROFILE] == ("Profile band", "toggle", False),
      str(_items))
check("set menu has wheel layers",
      _items[uimod.SET_WHEEL_LAYERS] == ("Wheel layers", "toggle", False),
      str(_items[uimod.SET_WHEEL_LAYERS]))
check("set menu has key test", _items[uimod.SET_KEYTEST][0] == "Key test")

# Settings > Key test: the Setup wiring check, run from the device with no app
# attached. Confirming the entry suppresses playback and takes over the screen;
# PSH held TEST_EXIT_HOLD_S goes back to Settings, Auto-return goes to the grid.
# Settings > Pixel test: the whole panel lights so a dead column or a stuck row
# shows up. Nothing on it is readable, so EVERY button has to be a way out —
# that is the invariant worth locking down.
from mkyada import icons as fw_icons  # noqa: E402

# --- the grid's six icons: named, drawn, absent, retired, or refused ---
# Three states are easy to collapse into two by accident: no "icon" field means
# "the action family chooses", and only the reserved name "none" means "draw
# nothing". Without the second there was no way to ask for a bare, full-width
# name on a key whose kind has a default.
_ico_l = ui.app.layer
ui._icons.clear()
ui._kinds.clear()
for _k in range(6):
    ui._kinds[(_ico_l, _k)] = ("keystroke", None)
ui._icons[(_ico_l, 0)] = "rocket"
ui._icons[(_ico_l, 1)] = "none"
ui._icons[(_ico_l, 2)] = "px:183c7effc3c30000"
ui._icons[(_ico_l, 3)] = "no-such-icon-was-ever-shipped"
_ico = ui._grid_icons(_ico_l)
check("a named icon is drawn", _ico[0] == fw_icons.get("rocket"))
check("\"none\" draws nothing, not the kind default", _ico[1] is None)
check("a hand-drawn icon is drawn",
      _ico[2] == b"\x18\x3c\x7e\xff\xc3\xc3\x00\x00")
# A retired name must fall back rather than blank the tile — the opposite of
# "none", and the reason "none" had to be a name of its own.
check("a retired name falls back to the kind default",
      _ico[3] == fw_icons.get("keyboard"))
check("no icon field means the kind default",
      _ico[4] == fw_icons.get("keyboard"))
ui._icons.clear()
ui._kinds.clear()

_px = 4000.0
ui.state = uimod.S_SET_MENU
ui.set_menu_sel = uimod.SET_PIXTEST
ui._set_menu_default(_px, 0, uimod.K_CONFIRM)
check("pixel test entry opens the pixel screen", ui.state == uimod.S_PIXELS,
      "state=%d" % ui.state)
# (that it actually lights every pixel is checked in tests/oled_render_test.py —
# the display is headless here, so there is nothing to count)
# the press that opened it must not immediately close it again
ui.tick(_px + 0.01)
check("pixel test survives the press that opened it", ui.state == uimod.S_PIXELS)
for _btn, _name in ((uimod.K_PSH, "PSH"), (uimod.K_BACK, "BACK"),
                    (uimod.K_CONFIRM, "CONFIRM")):
    ui.set_menu_sel = uimod.SET_PIXTEST
    ui._set_menu_default(_px, 0, uimod.K_CONFIRM)
    ui.nav.events.queue.append(FakeKeyEvent(_btn, True))
    ui.tick(_px + 1)
    check("pixel test %s returns to settings" % _name,
          ui.state == uimod.S_SET_MENU, "state=%d" % ui.state)
# and Auto-return is still a backstop if nothing is pressed at all
ui.set_menu_sel = uimod.SET_PIXTEST
ui._set_menu_default(_px, 0, uimod.K_CONFIRM)
ui.tick(_px + ui.idle_secs + 1)
check("pixel test idles back to settings", ui.state == uimod.S_SET_MENU)
ui._drain_inputs()

_kt = 5000.0
ui.state = uimod.S_SET_MENU
ui.set_menu_sel = uimod.SET_KEYTEST
ui._set_menu_default(_kt, 0, uimod.K_CONFIRM)
check("key test entry opens the test screen",
      ui.state == uimod.S_TEST and ui.test_ui == "self", "state=%d" % ui.state)
check("key test suppresses playback",
      vapp.test_mode and vapp.test_local)
vplays.clear()
vapp.on_edge(0, True)   # a macro key reports itself instead of playing
check("key test key press plays nothing", vplays == [], str(vplays))
# the wheel and the module buttons report too, and each one is activity
ui.enc.position += 1
ui.tick(_kt + 1)
check("key test wheel keeps the screen", ui.state == uimod.S_TEST)
ui.nav.events.queue.append(FakeKeyEvent(uimod.K_BACK, True))
ui.tick(_kt + 2)
check("key test BACK reports instead of leaving", ui.state == uimod.S_TEST)
# Settings > Key test is device-owned, so its wheel and nav events must NOT be
# mirrored to a connected app. They used to be: the app answered the traffic
# with test_enter, which reset test_ui to "wiring", and a single detent turned
# the user's own key test into the app's setup test under them.
_kt_ser = vapp.proto.ser
vapp.proto.ser = FakeSerial([])   # "connected" — Proto.connected reads the port
voutbox.clear()
ui.enc.position += 1
ui.tick(_kt + 2.1)
ui.nav.events.queue.append(FakeKeyEvent(uimod.K_CONFIRM, True))
ui.tick(_kt + 2.2)
check("key test does not stream the wheel to the app",
      not any(m.get("t") == "enc" for m in voutbox), str(voutbox))
check("key test does not stream the nav buttons to the app",
      not any(m.get("t") == "btn" and "slot" in m for m in voutbox), str(voutbox))
check("key test stays the key test with an app connected",
      ui.state == uimod.S_TEST and ui.test_ui == "self", "ui=%s" % ui.test_ui)
# The app-driven wiring test still streams — that IS its whole purpose.
ui.test_ui = "wiring"
voutbox.clear()
ui.enc.position += 1
ui.tick(_kt + 2.3)
check("the app-driven wiring test still streams the wheel",
      any(m.get("t") == "enc" for m in voutbox), str(voutbox))
# ...but only the WIRING test names the control on the glass. The Keys tab
# (test_ui "keys") puts up a static "macros are paused, use the other tab"
# warning and leaves it up; repainting a SETUP TEST card over it for a wheel
# detent or a BACK press turned the Keys test into a different test in front
# of the user. Key presses already knew this (on_test_key); the wheel and the
# nav buttons were the two paths that didn't.
_toasts = []
_orig_toast = ui.oled.show_toast
ui.oled.show_toast = lambda *a, **k: _toasts.append(a)
ui.test_ui = "keys"
voutbox.clear()
ui.enc.position += 1
ui.tick(_kt + 2.4)
ui.nav.events.queue.append(FakeKeyEvent(uimod.K_BACK, True))
ui.tick(_kt + 2.5)
check("the Keys tab test does not repaint over its own warning",
      not _toasts, str(_toasts))
check("the Keys tab test still streams the wheel to the app",
      any(m.get("t") == "enc" for m in voutbox), str(voutbox))
check("the Keys tab test still streams the nav buttons to the app",
      any(m.get("t") == "btn" and "slot" in m for m in voutbox), str(voutbox))
ui.test_ui = "wiring"
ui.nav.events.queue.append(FakeKeyEvent(uimod.K_BACK, True))
ui.tick(_kt + 2.6)
check("the wiring test does still name the button it saw", bool(_toasts))
ui.oled.show_toast = _orig_toast
ui.test_ui = "self"
vapp.proto.ser = _kt_ser
ui._drain_inputs()
# PSH: a press alone reports like any other button...
ui.nav.events.queue.append(FakeKeyEvent(uimod.K_PSH, True))
ui.tick(_kt + 3)
check("key test PSH press stays", ui.state == uimod.S_TEST)
ui.tick(_kt + 3 + uimod.TEST_EXIT_HOLD_S - 0.1)
check("key test PSH not held long enough", ui.state == uimod.S_TEST)
# ...and only leaves once it has been held out the full three seconds
ui.tick(_kt + 3 + uimod.TEST_EXIT_HOLD_S)
check("key test PSH hold returns to settings",
      ui.state == uimod.S_SET_MENU, "state=%d" % ui.state)
check("key test hold-exit restores playback",
      not vapp.test_mode and not vapp.test_local)
# Auto-return is the other way out, floored so a 3s timeout can't make the
# screen unusable
ui.idle_secs = 3
ui._set_menu_default(_kt, 0, uimod.K_CONFIRM)
ui.tick(_kt + uimod.TEST_IDLE_MIN_S)
check("key test survives a short Auto-return", ui.state == uimod.S_TEST)
ui.tick(_kt + uimod.TEST_IDLE_MIN_S + 1)
check("key test idles back to the grid",
      ui.state == uimod.S_SELECT and not vapp.test_mode, "state=%d" % ui.state)
ui.idle_secs = uimod.DEFAULT_TIMEOUT

# grid band composition (fw 0.9.0): layer part is device-side, profile part
# is whatever the app last pushed via {"t":"label"}
vapp.config["show_layer"] = False
vapp.config["show_profile"] = False
vapp.host_label = "Photoshop"
check("band both off -> none", ui._band() is None, str(ui._band()))
vapp.config["show_layer"] = True
vapp.layer = 1
check("band layer only", ui._band() == "Layer B", str(ui._band()))
vapp.config["show_profile"] = True
check("band layer + profile", ui._band() == "(B) Photoshop", str(ui._band()))
# the app-pushed label (live OBS scene / profile) outranks the stored nickname
vapp.config["layer_names"] = [None, "studyo"]
check("band label beats nickname", ui._band() == "(B) Photoshop", str(ui._band()))
vapp.host_label = None
check("band nickname without label", ui._band() == "(B) studyo", str(ui._band()))
vapp.host_label = "Photoshop"
vapp.config["layer_names"] = None
# Recording/live are drawn as a chip and a blinking dot at the band's right
# end now, so they are no longer spliced into the text — the band string is the
# layer and the label, and _band_state() carries the rest.
vapp.host_rec = True
ui._blink_on = True
check("band text has no state markers", ui._band() == "(B) Photoshop",
      str(ui._band()))
check("band state reports recording", ui._band_state() == (True, False, True),
      str(ui._band_state()))
vapp.host_live = True
check("band state reports rec+live", ui._band_state() == (True, True, True),
      str(ui._band_state()))
ui._blink_on = False
check("band state carries the blink phase",
      ui._band_state() == (True, True, False), str(ui._band_state()))
ui._blink_on = True
vapp.host_rec = False
vapp.host_live = False
check("band state idle", ui._band_state() == (False, False, True),
      str(ui._band_state()))
check("band text unchanged when idle", ui._band() == "(B) Photoshop",
      str(ui._band()))

# hello advertises the biggest fs_write chunk this board's heap can hold in
# one contiguous block, so the app never has to discover it by failing
_h = vapp.hello()
check("hello advertises fs_chunk", _h.get("fs_chunk") == vis_mod.FS_WRITE_CHUNK,
      str(_h.get("fs_chunk")))
check("display model caps write chunk at 512B", vis_mod.FS_WRITE_CHUNK == 512,
      str(vis_mod.FS_WRITE_CHUNK))

# the blink tick: idle _st_select calls flip the phase every ~0.6s while a
# marker is active, throttled in between
vapp.host_rec = True
ui.state = uimod.S_SELECT
ui.sel_mode = False
ui._blink_at = 0.0
ui.activity_at = 1000.0
_b0 = ui._blink_on
ui._st_select(1000.0, 0, None)
check("blink tick flips phase", ui._blink_on == (not _b0), str(ui._blink_on))
ui._st_select(1000.2, 0, None)
check("blink tick throttled <0.6s", ui._blink_on == (not _b0), str(ui._blink_on))
ui._st_select(1000.7, 0, None)
check("blink tick flips again", ui._blink_on == _b0, str(ui._blink_on))
vapp.host_rec = False
ui._blink_on = True
vapp.config["show_layer"] = False
check("band profile only", ui._band() == "Photoshop", str(ui._band()))
vapp.host_label = None
check("band profile without label -> none", ui._band() is None, str(ui._band()))

# {"t":"label"} lands in host_label and redraws through on_label (headless
# no-op here — the point is it must not crash mid-grid)
ui.state = uimod.S_SELECT
vapp.handle_msg({"t": "label", "text": "GIMP", "rec": True, "live": True})
check("vision6 label stored", vapp.host_label == "GIMP", str(vapp.host_label))
check("vision6 rec/live flags stored", vapp.host_rec and vapp.host_live)
vapp.handle_msg({"t": "label", "text": ""})
check("vision6 label cleared", vapp.host_label is None)
check("vision6 rec/live flags cleared", not vapp.host_rec and not vapp.host_live)
vapp.config["show_profile"] = False
vapp.layer = 0

# persist_lang rewrites config.json and announces the fresh config

_lang_dir = tempfile.mkdtemp()
_lang_cfg = os.path.join(_lang_dir, "config.json")
with open(_lang_cfg, "w") as f:
    json.dump({"model": "vision6", "layer_count": 4}, f)


def _lang_open(path, *a, **k):
    p = str(path)
    if p.startswith("/config.json"):
        return _real_open(_lang_cfg + p[len("/config.json"):], *a, **k)
    return _real_open(path, *a, **k)


_orig_os_remove, _orig_os_rename = os.remove, os.rename


def _map(p):
    p = str(p)
    return _lang_cfg + p[len("/config.json"):] if p.startswith("/config.json") else p


os.remove = lambda p: _orig_os_remove(_map(p))
os.rename = lambda a, b: _orig_os_rename(_map(a), _map(b))
_b.open = _lang_open
voutbox.clear()
vapp.proto.send = lambda obj: (voutbox.append(obj), True)[1]
res_lang = ui.persist_lang("tr")
_b.open = _real_open
os.remove, os.rename = _orig_os_remove, _orig_os_rename
with open(_lang_cfg) as f:
    _lang_data = json.load(f)
check("persist_lang ok", res_lang == "ok")
check("persist_lang wrote file", _lang_data.get("lang") == "tr"
      and _lang_data.get("layer_count") == 4, str(_lang_data))
check("persist_lang announces config",
      any(m.get("t") == "config" and m.get("lang") == "tr" for m in voutbox), str(voutbox))
check("persist_lang applied", i18nmod.get_lang() == "tr")
i18nmod.set_lang("en")
vapp.config["lang"] = "en"
shutil.rmtree(_lang_dir, ignore_errors=True)

# set_cfg (proto v14): the app patches display prefs live over serial —
# config.json is rewritten, ok + config go out, nothing needs a reload
_sc_dir = tempfile.mkdtemp()
_sc_cfg = os.path.join(_sc_dir, "config.json")
with open(_sc_cfg, "w") as f:
    json.dump({"model": "vision6", "layer_count": 1}, f)


def _sc_open(path, *a, **k):
    p = str(path)
    if p.startswith("/config.json"):
        return _real_open(_sc_cfg + p[len("/config.json"):], *a, **k)
    return _real_open(path, *a, **k)


def _sc_map(p):
    p = str(p)
    return _sc_cfg + p[len("/config.json"):] if p.startswith("/config.json") else p
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
