asilbalaban/MKYADA/firmware/mkyada/ui.py

# Vision 6 menu module: EC11 encoder + PSH/BACK/CONFIRM buttons driving the
# OLED screens in mkyada/oled.py. Non-blocking — App.run_loop() calls tick()
# every iteration; playback never waits on the UI.
#
# Default interaction (the bring-up demo, productionized):
#   home     encoder scrolls layer letters + SETTINGS, PSH/CONFIRM enters
#   grid     the active layer's 6 macro names; encoder selects a cell,
#            CONFIRM opens that key's speed editor, BACK returns home
#   speed    encoder edits 0.1x-10.0x, CONFIRM persists it into the key's
#            macro file (settings.speed) — the app sees the same value
# Custom slots (macros/enc-cw.json etc., written by the app) override the
# resting grid: rotation/BACK/CONFIRM/PSH then play their macros, and the
# menus keep default navigation. Each menu context can be overridden on its
# own too (issue #19): macros/<slot>@home.json applies on the layer picker,
# macros/<slot>@menu.json inside settings. Button slots may carry key-logic
# variants (double / hold) resolved here from nav events; a "menu"-kind
# assignment drives the BUILT-IN navigation (never other custom slots).
# Escape hatch: on a customized grid PSH toggles a temporary default-nav
# "select mode"; with PSH itself assigned, holding it ESC_HOLD_S does —
# unless the user deliberately gave PSH its own hold action (then the menu
# stays reachable via keys mapped to menu actions, or the app).
#
# NVM keeps only UI prefs: [magic, idle_secs, last_layer].
# Macro speeds live in /macros/meta.json (proto v14, mkyada/meta.py): a
# speed edit writes that small sidecar, never the macro body — the old
# whole-file rewrite could out-run the watchdog on a long recording and
# take the FAT with it. Headers keep settings.speed as the fallback.

import gc
import json
import os
import time
from binascii import crc32

import board
import keypad
import rotaryio

from mkyada import meta

try:
    import microcontroller
except Exception:
    microcontroller = None
try:
    NVM = microcontroller.nvm if microcontroller else None
except Exception:
    NVM = None

from mkyada import i18n
from mkyada.i18n import tr, upper
from mkyada.models import MODELS, UI_SLOTS
from mkyada.oled import fmt_speed

LAYER_NAMES = "abcdefgh"

# Bumped from 0x4E when the font byte left the layout: a board written by an
# older firmware holds [magic, font_idx, idle_secs, last_layer], and reading
# that as the new layout would restore a font index as the idle timeout.
# A mismatched magic just falls back to defaults, which is the right answer.
MAGIC = 0x4F
NVM_LEN = 3

SPEED_MIN_T, SPEED_MAX_T, SPEED_DEF_T = 1, 100, 10
TMO_MIN, TMO_MAX, DEFAULT_TIMEOUT = 3, 60, 10

K_PSH, K_BACK, K_CONFIRM = 0, 1, 2
NAV_SLOT = ("psh", "back", "confirm")  # host-mode event names
# nav key -> its assignable slot name (standalone custom assignments)
NAV_SLOTS = {K_PSH: "btn-psh", K_BACK: "btn-back", K_CONFIRM: "btn-confirm"}
# PSH held this long toggles select mode when its slot has no hold variant —
# past the 400 ms variant default so an assigned hold still wins cleanly
ESC_HOLD_S = 1.2
# Settings > Key test: PSH held this long leaves the screen. Deliberately long
# — PSH is one of the buttons under test, so a tap has to stay a tap.
TEST_EXIT_HOLD_S = 3.0
# ...and the test also returns to the grid on the Auto-return timeout, but
# never sooner than this: reading a pin name off the screen between presses is
# the whole point, and Auto-return goes as low as 3 seconds.
TEST_IDLE_MIN_S = 15
# how long the device waits for the app to answer a host-kind CONFIRM with a
# `menu` before giving up and showing the "app required" toast. Long enough
# for the app's cold-cache path: the first open of a key's menu reads its
# macro file over serial (with retries if the link is busy) before answering.
CTX_WAIT_S = 3.0
# Dial module: a turn gesture on a drag slot is one continuous mouse drag;
# the held left button is released this long after the last detent. Long
# enough to survive detent gaps at slow deliberate turns, short enough that
# the control is dropped as soon as the hand leaves the wheel.
DRAG_RELEASE_S = 0.35
# Gestures that also hold modifiers get a longer window: on macOS a
# Ctrl+click that ends without enough travel is SYNTHESIZED into a right
# click (field bug: the Photoshop brush scrub popped the context menu on
# slow single detents). A longer window merges hesitant detents into one
# button-hold, so the release almost always follows real drag distance.
MOD_DRAG_RELEASE_S = 0.8

(S_HOME, S_SELECT, S_SPEED, S_SAVED, S_SET_MENU, S_TIMEOUT,
 S_PLAYING, S_HOST, S_TOAST, S_LANG, S_TEST, S_ABOUT, S_CTX,
 S_PIXELS, S_XFER) = range(15)

# media usages the wheel treats as a "turn to adjust" knob rather than a
# single transport key (see _enter_ctx). Volume rotates up/down, CONFIRM mutes.
VOL_USAGES = ("volume_up", "volume_down", "mute")
BRIGHT_USAGES = ("brightness_up", "brightness_down")

# the media wheel menu is a browser of every consumer usage: turn to highlight
# one, tap to fire it once, hold to reassign the key to it (issue: wheel-menu
# grammar). Order is the on-screen list order.
# Prev before Next everywhere a pair like this is listed — the order the
# transport controls sit in on any physical remote.
NOTE_NAMES = ("C", "C#", "D", "D#", "E", "F", "F#", "G", "G#", "A", "A#", "B")


def note_name(n):
    """MIDI note number -> the name DAWs print (60 = C3)."""
    return "%s%d" % (NOTE_NAMES[n % 12], n // 12 - 2)


class _LabelView:
    """len()/[] over an option list, labelling only the rows show_menu draws.

    The browsers used to build every label on every detent. That is fine for
    nine media keys and ruinous for 128 MIDI notes on a heap this fragmented:
    a redraw would allocate 128 strings per turn. show_menu only ever reads
    its visible window, so nothing else needs to exist."""

    def __init__(self, ui, kind, opts):
        self._ui = ui
        self._kind = kind
        self._opts = opts

    def __len__(self):
        return len(self._opts)

    def __getitem__(self, i):
        return self._ui._opt_label(self._kind, self._opts[i])


MEDIA_OPTS = ("play_pause", "prev_track", "next_track", "stop", "mute",
              "volume_up", "volume_down", "brightness_up", "brightness_down")
MEDIA_LABEL = {"play_pause": "Play/Pause", "next_track": "Next",
               "prev_track": "Prev", "stop": "Stop", "mute": "Mute",
               "volume_up": "Vol +", "volume_down": "Vol -",
               "brightness_up": "Bright +", "brightness_down": "Bright -"}

# menu-kind (layer / nav) options the wheel browser offers: switch layers or
# jump to a screen. The absolute layer_a.. entries are appended per device from
# layer_count. All are runnable on-device with no host, so the browser reassigns
# standalone just like the media one (issue: layer keys only ran "next layer").
MENU_FIXED_OPTS = ("layer_prev", "layer_next", "home", "grid", "settings")
MENU_LABEL = {"layer_next": "Next layer", "layer_prev": "Prev layer",
              "home": "Home", "grid": "Grid", "settings": "Settings"}

# how long CONFIRM/PSH must be held inside a menu to mean "assign" (vs a tap =
# "do it once"). Matches the key-logic hold default.
MENU_HOLD_S = 0.4

# Action family -> icon name, for macros that don't name one themselves. The
# names are the ones in icons/src/icons.txt; kinds are docs/actions.md.
KIND_ICON = {"keystroke": "keyboard", "combo": "keyboard", "text": "text",
             "recorded": "record", "media": "play", "volume": "volume",
             "scroll": "scroll-v", "menu": "layers", "sequence": "sequence",
             "launch": "rocket", "command": "terminal", "sound": "music",
             "mic": "mic", "mic_level": "mic", "webhook": "webhook",
             "obs": "camera", "obs_center": "camera", "enc_module": "dial",
             "midi": "note"}

# mtype:"obs" menu fields the app may push (proto v13): a re-send while the
# menu is open merges only the fields present in the message into the open
# ctx, so the app can push tiny deltas ({"mic": 42}) between full re-asserts.
# A field the app never sends stays None and its widget is simply not drawn.
OBS_FIELDS = ("obsview", "rec", "live", "mic", "time", "scene",
              "mute", "cpu", "fps", "drop", "klabels", "focus")

(SET_TMO, SET_LANG, SET_BAND_LAYER, SET_BAND_PROFILE, SET_WHEEL_LAYERS,
 SET_KEYTEST, SET_PIXTEST, SET_ABOUT, SET_REBOOT) = range(9)

SAVED_DWELL_S = 1.1
TOAST_DWELL_S = 1.6
META_MAX_WHOLE = 4096  # parse pretty-printed files only up to this size


def clamp(v, lo, hi):
    return lo if v < lo else (hi if v > hi else v)


class Ui:
    def __init__(self, app, oled):
        self.app = app
        self.oled = oled
        m = MODELS[app.model]
        ea, eb = m["encoder"]
        if app.config.get("enc_swap"):
            ea, eb = eb, ea  # encoder soldered backwards: flip CW/CCW
        self.enc = rotaryio.IncrementalEncoder(getattr(board, ea),
                                               getattr(board, eb))
        nav_pins = app.config.get("nav") or m["nav"]
        self.nav = keypad.Keys(tuple(getattr(board, n) for n in nav_pins),
                               value_when_pressed=False, pull=True)
        self.last_enc = self.enc.position

        i18n.set_lang(app.config.get("lang"))
        self.idle_secs, last_layer = self._nvm_load()
        # config.json can carry timeout (the app-facing mirror). When it does,
        # it wins over NVM so a value set from the app applies; either way we
        # publish the resolved value into app.config so hello reports it
        # without waiting for the first on-device change.
        ct = app.config.get("timeout")
        if isinstance(ct, int) and TMO_MIN <= ct <= TMO_MAX:
            self.idle_secs = ct
        app.config["timeout"] = self.idle_secs
        self.lang_sel = 0
        self.state = S_HOME
        self.prev_state = S_HOME  # where to return after host mode / toast
        self.test_ui = "wiring"  # S_TEST flavour: app "wiring"/"keys", or "self"
        # Settings > Key test counters. The old screen named one control
        # at a time, so the silent key was found by pressing them in turn;
        # this holds all of them so it stands out on its own.
        self._kt = None
        self._psh_down_at = None  # PSH press time, for the key test's hold-exit
        self.home_pos = 0
        self.sel_key = 0
        self.sel_mode = False  # temporary default-nav mode on a custom grid
        # Set while a wheel detent is carrying the selection across a layer
        # boundary, so on_layer knows the tile has already been chosen.
        self._wheel_move = False
        self.speed_t = SPEED_DEF_T
        self.set_menu_sel = 0
        self.tmo_val = self.idle_secs
        self.saved_at = 0.0
        self.toast_at = 0.0
        self.last_move = 0.0
        self.activity_at = time.monotonic()
        self.playing_cell = None
        self.ctx = None  # active context-menu (S_CTX) descriptor
        self._blink_at = 0  # last (R)/(L) band-marker blink flip
        self._blink_on = True
        self.sysvol = None  # live system output volume % pushed by the app
        self._pending_layer = clamp(last_layer, 0,
                                    app.config["layer_count"] - 1)
        self._enc_batch = 0  # host mode: accumulated detents
        self._labels = {}  # layer -> [(l1, l2)] * 6
        self._speeds = {}  # (layer, key0) -> tenths
        self._kinds = {}   # (layer, key0) -> (kind, sub) for the wheel menu
        self._icons = {}   # (layer, key0) -> the macro's own icon name, if any
        self._slots = {}   # layer -> {slot: meta dict or None} (grid context)
        self._ctx_slots = {}  # "home" / "menu" -> {slot: meta dict or None}
        self._injecting = 0  # >0 while a macro key drives the menu (inject)

    # --- NVM prefs ---
    def _nvm_load(self):
        if NVM is not None and len(NVM) >= NVM_LEN and NVM[0] == MAGIC:
            tmo, lyr = NVM[1], NVM[2]
            if not TMO_MIN <= tmo <= TMO_MAX:
                tmo = DEFAULT_TIMEOUT
            if not 0 <= lyr < len(LAYER_NAMES):
                lyr = 0
            return tmo, lyr
        return DEFAULT_TIMEOUT, 0

    def _nvm_save(self):
        if NVM is None:
            return
        try:
            NVM[0:NVM_LEN] = bytes((MAGIC, self.idle_secs, self.app.layer))
        except Exception:
            pass

    # --- labels / speeds / slots (lazy per layer) ---
    def _read_meta(self, path):
        """(name, speed_tenths, kind, sub) from a macro file's header without
        loading events: stream files carry it in line 1, legacy app files are
        one line anyway; small pretty-printed files get a full parse. `kind`
        drives the context-aware wheel menu (issue: wheel-menu redesign); `sub`
        is the one extra field that menu needs (media usage, obs action, ...)."""
        try:
            size = os.stat(path)[6]
        except OSError:
            return None, SPEED_DEF_T, None, None, None
        data = None
        try:
            with open(path, "rb") as f:
                try:
                    data = json.loads(f.readline())
                except ValueError:
                    if size <= META_MAX_WHOLE:
                        f.seek(0)
                        data = json.load(f)
        except (OSError, ValueError, MemoryError):
            data = None
        if not isinstance(data, dict):
            return None, SPEED_DEF_T, None, None, None
        name = data.get("name")
        speed = (data.get("settings") or {}).get("speed", 1.0)
        try:
            t = clamp(int(round(float(speed) * 10)), SPEED_MIN_T, SPEED_MAX_T)
        except (TypeError, ValueError):
            t = SPEED_DEF_T
        kind = data.get("kind")
        sub = None
        if kind == "obs":
            o = data.get("obs")
            sub = o.get("action") if isinstance(o, dict) else None
        elif kind == "media":
            sub = data.get("media")
        elif kind == "mic":
            sub = data.get("mic_mode") or "toggle"
        elif kind == "scroll":
            sc = data.get("scroll")
            sub = sc.get("dir") if isinstance(sc, dict) else None
        elif kind == "midi":
            m = data.get("midi")
            sub = m.get("msg") if isinstance(m, dict) else None
        elif kind == "menu":
            sub = data.get("menu")
        # The icon a macro picks for itself, by name. Validated in oled/
        # icons.get(): an unknown one is simply not found and the caller falls
        # back to the action family default.
        icon = data.get("icon")
        if not isinstance(icon, str) or not icon:
            icon = None
        return (name if isinstance(name, str) and name else None), t, kind, sub, icon

    def _node(self, d):
        """Classify what an assignment (macro dict) does when it fires:
        ("menu", action) drives the built-in navigation, ("play",) plays
        the macro file. None for an absent/invalid variant."""
        if not isinstance(d, dict):
            return None
        if d.get("kind") == "menu":
            return ("menu", d.get("menu") or "default")
        return ("play",)

    def _read_slot_meta(self, path):
        """What a slot file's tap/double/hold gestures do, parsed from the
        header line without loading events (same cost as _read_meta).
        Returns a meta dict, or None when the file doesn't exist."""
        try:
            size = os.stat(path)[6]
        except OSError:
            return None
        data = None
        try:
            with open(path, "rb") as f:
                try:
                    data = json.loads(f.readline())
                except ValueError:
                    if size <= META_MAX_WHOLE:
                        f.seek(0)
                        data = json.load(f)
        except (OSError, ValueError, MemoryError):
            data = None
        if not isinstance(data, dict):
            data = {}
        variants = data.get("variants")
        if data.get("stream") or not isinstance(variants, dict):
            variants = {}  # stream files never carry variants
        s = data.get("settings") or {}
        return {"path": path,
                "tap": self._node(data) or ("play",),
                "double": self._node(variants.get("double")),
                "hold": self._node(variants.get("hold")),
                "hold_s": (s.get("hold_ms") or 400) / 1000.0,
                "double_s": (s.get("double_ms") or 250) / 1000.0}

    def _set_items(self):
        """(label, kind, value) per row. The state used to be baked into the
        label ("Layer band: on") because the old list had nowhere else to put
        it; the redesigned screen has a value column, so a toggle draws as a
        switch and Language finally shows which language is selected."""
        cfg = self.app.config
        return ((tr("auto_return"), "text", "%ds" % self.idle_secs),
                (tr("language"), "text", i18n.LANG_DESC[
                    i18n.LANGS.index(i18n.get_lang())]),
                (tr("show_layer"), "toggle", cfg["show_layer"]),
                (tr("show_profile"), "toggle", cfg["show_profile"]),
                (tr("wheel_layers"), "toggle", cfg["wheel_layers"]),
                (tr("key_test"), "none", None),
                (tr("pixel_test"), "none", None),
                (tr("about"), "none", None),
                (tr("restart"), "none", None))

    def _split_name(self, name):
        return self.oled.split_name(name)

    def _exists(self, path):
        try:
            os.stat(path)
            return True
        except OSError:
            return False

    def load_layer(self, l):
        labels = []
        chars = set()
        for k in range(1, 7):
            path = self.app.macro_path_for(k, l)
            name, t, kind, sub, icon = self._read_meta(path)
            # meta.json overrides (proto v14) shadow the header: a speed or
            # icon edit on a big recorded macro lands there, not in the body
            ov = self.app.meta_ov.get(meta.stem_of(path))
            if ov:
                if "s" in ov:
                    try:
                        t = clamp(int(ov["s"]), SPEED_MIN_T, SPEED_MAX_T)
                    except (TypeError, ValueError):
                        pass
                if isinstance(ov.get("n"), str) and ov["n"]:
                    name = ov["n"]
                if isinstance(ov.get("i"), str) and ov["i"]:
                    icon = ov["i"]
            self._speeds[(l, k - 1)] = t
            self._kinds[(l, k - 1)] = (kind, sub)
            self._icons[(l, k - 1)] = icon
            pair = self._split_name(name or ("K%d" % k))
            labels.append(pair)
        self._labels[l] = labels
        slots = {}
        for s in UI_SLOTS:
            p = self.app.slot_path(s, l)
            if not self._exists(p):
                p0 = self.app.slot_path(s, 0)
                p = p0 if (l != 0 and self._exists(p0)) else None
            slots[s] = self._read_slot_meta(p) if p else None
        self._slots[l] = slots
        gc.collect()

    def labels(self, l):
        if l not in self._labels:
            self.load_layer(l)
        return self._labels[l]

    def slots(self, l):
        if l not in self._slots:
            self.load_layer(l)
        return self._slots[l]

    def ctx_slots(self, ctx):
        """Per-context nav overrides ("home" = layer picker, "menu" =
        settings): macros/<slot>@<ctx>.json — global files, no layers."""
        if ctx not in self._ctx_slots:
            slots = {}
            for s in UI_SLOTS:
                slots[s] = self._read_slot_meta(self.app.slot_ctx_path(s, ctx))
            self._ctx_slots[ctx] = slots
        return self._ctx_slots[ctx]

    def speed_tenths(self, l, key0):
        if (l, key0) not in self._speeds:
            self.load_layer(l)
        return self._speeds.get((l, key0), SPEED_DEF_T)

    def kind_sub(self, l, key0):
        """(kind, sub) for the key's assignment, driving the wheel menu."""
        if (l, key0) not in self._kinds:
            self.load_layer(l)
        return self._kinds.get((l, key0), (None, None))

    def cache_stats(self):
        """Container sizes for the console heap telemetry — the growing one
        names the retainer when free memory declines over a session."""
        return (len(self._labels), len(self._slots), len(self._kinds),
                len(self._speeds), len(self._ctx_slots))

    def invalidate_labels(self, path=None):
        """A macro file changed (app upload / delete). Drop the affected
        layer's cache; None drops everything."""
        if path is None:
            layers = list(self._labels.keys()) + list(self._slots.keys())
            self._ctx_slots.clear()
        else:
            name = path.rsplit("/", 1)[-1]
            if name.endswith(".json"):
                name = name[:-5]
            if "@" in name:
                # context override (enc-cw@home) — global, not layered
                self._ctx_slots.pop(name.rsplit("@", 1)[-1], None)
                return
            base, l = name, 0
            if "-" in name:
                stem, suffix = name.rsplit("-", 1)
                if len(suffix) == 1 and suffix in LAYER_NAMES:
                    base, l = stem, LAYER_NAMES.index(suffix)
            # Only grid key files (keyN[-l]) and slot files (enc-cw[-l], ...)
            # live in these caches. Anything else — profile copies
            # (p_<id>_key1) and sequence/variant part files (key3-b.2) — used
            # to be misread as "layer A changed" and wipe EVERY layer: the
            # app's connect-time profile sync then caused ~15 back-to-back
            # full wipes + repaints, refilling the caches mid-session and
            # shredding the heap until repaints died.
            if not ((base.startswith("key") and base[3:].isdigit())
                    or base in UI_SLOTS):
                return
            layers = [l]
            if l == 0 and base in UI_SLOTS:
                # layer-A slot files are the fallback other layers inherit
                layers = list(set([0] + list(self._slots.keys())))
        for l in set(layers):
            self._labels.pop(l, None)
            self._slots.pop(l, None)
            for k in range(6):
                self._speeds.pop((l, k), None)
                self._kinds.pop((l, k), None)
                self._icons.pop((l, k), None)
        if self.state == S_SELECT and self.app.layer in set(layers):
            self._draw_grid()

    # --- speed persistence ---
    def persist_speed(self, l, key0, tenths):
        """Write the key's speed override into /macros/meta.json. Returns
        "ok" | "missing" | "readonly" | "error".

        The macro body is never touched — the old whole-file rewrite could
        out-run the 8s watchdog on a long recording and corrupt the FAT
        mid-write (the incident that reformatted a board). Under an active
        profile the override keys on the profile's stem, so a per-app speed
        never shadows the shared standalone macro (issue #23) — and the
        copy-on-write of the whole file is gone with the rewrite.
        """
        path = self.app.macro_path_for(key0 + 1, l)  # profile file or std
        try:
            os.stat(path)
        except OSError:
            return "missing"
        stem = meta.stem_of(path)
        if not stem:
            return "error"
        res = meta.update(stem, fields={"s": tenths})
        if res != "ok":
            return res
        ov = self.app.meta_ov.get(stem)
        if not isinstance(ov, dict):
            ov = {}
            self.app.meta_ov[stem] = ov
        ov["s"] = tenths
        self._speeds[(l, key0)] = tenths
        self.app.proto.send({"t": "macro_changed", "file": path,
                             "reason": "speed"})
        return "ok"

    # --- hooks from App ---
    def start(self):
        """First draw; runs once from App.run_loop()."""
        self.oled.boot_progress(1.0)
        if self._pending_layer:
            self.app.set_layer_idx(self._pending_layer)  # re-enters on_layer
        l = self.app.layer
        # Preload EVERY layer now, while the heap is young. These caches are
        # small but long-lived; loading them lazily on first visit used to pin
        # them into the middle of an aging heap, and since CircuitPython's GC
        # never compacts, the heap shredded until layer repaints died on
        # double-digit-byte allocations ("B never shows"). Front-loading them
        # (and every layer's glyphs, in one font pass) keeps the long-lived
        # objects low and the rest of the heap in one piece.
        n = self.app.config["layer_count"]
        try:
            for i in range(n):
                self.labels(i)
        except MemoryError:
            gc.collect()
        # Boot straight into the last active layer's macro grid, not the layer
        # picker: the common case is "use the keypad", and the picker still
        # sits one BACK away. Avoids the boot-time picker feeling stuck while
        # the first layer's labels load.
        self.home_pos = l
        self.sel_key = 0
        self.sel_mode = False
        self.state = S_SELECT
        self.activity_at = time.monotonic()
        self._draw_grid()

    def on_label(self):
        """The app pushed (or cleared) its profile label, key names or live
        OBS state."""
        if self.state == S_HOST:
            self._draw_host()
        elif self.state == S_SELECT:
            # Gating this on show_profile alone was issue #37: with only the
            # LAYER band on, the band still renders the pushed text and the
            # (R)/(L) markers — but nothing repainted until the next unrelated
            # redraw, so "R" appeared one action late (or never).
            cfg = self.app.config
            if cfg["show_layer"] or cfg["show_profile"]:
                self._band_repaint()

    def _band_repaint(self):
        """Update just the band strip (blink markers, live OBS scene). Falls
        back to a full grid paint when there's no persistent group to poke."""
        if not self.oled.update_band(self._band(), self._grid_page(),
                                     self._band_state()):
            self._draw_grid()

    def _drop_macro_cache(self):
        """Forget everything read out of the macro files. Whatever changed
        them — a profile switch, a config reload, the app writing new ones —
        this cache is now describing files that no longer exist."""
        self._labels.clear()
        self._speeds.clear()
        self._kinds.clear()
        self._icons.clear()
        self._slots.clear()

    def on_profile(self):
        """A per-app profile was activated or cleared (issue #23): the macro
        files behind every key/slot changed, so drop the cached labels,
        speeds and slots and repaint the grid with the new set."""
        self._drop_macro_cache()
        if self.state in (S_SELECT, S_CTX):
            self._enter_grid()

    def _draw_host(self):
        """Host-mode screen: the active profile's six key names as a grid
        (pushed by the app in the "label" message, proto v6) so the user
        sees what the keys do — not just that an app owns them. Falls back
        to the plain "Connected to app" text when the app sent no names."""
        keys = self.app.host_keys
        if not keys:
            self.oled.show_host()
            return
        labels = []
        chars = set()
        for i in range(6):
            name = keys[i] if i < len(keys) and keys[i] else "K%d" % (i + 1)
            pair = self._split_name(name)
            labels.append(pair)
        self.oled.show_grid(labels, None, False, self._band(), None,
                            self._grid_page(), self._band_state())

    def on_layer(self):
        if self.state not in (S_HOME, S_SELECT):
            return
        if self._wheel_move:
            # The wheel is mid-detent: it has already worked out which tile of
            # the new layer it is landing on and repaints once itself. Resetting
            # the selection and painting here as well is what made every detent
            # flash the first tile on its way past ("2 -> 1 -> 3"). Select mode
            # has to survive too — dropping it here would make the next detent
            # fire the custom encoder macro instead of paging on.
            return
        self.sel_key = 0
        self.sel_mode = False
        if self.state == S_SELECT:
            self._draw_grid()
        else:
            self.home_pos = self.app.layer
            self._draw_home()

    def on_reload(self):
        i18n.set_lang(self.app.config.get("lang"))
        # the app may have changed timeout in config.json — apply it
        ct = self.app.config.get("timeout")
        if isinstance(ct, int) and TMO_MIN <= ct <= TMO_MAX and ct != self.idle_secs:
            self.idle_secs = ct
            self._nvm_save()
        self.app.config["timeout"] = self.idle_secs
        self._drop_macro_cache()
        self._ctx_slots.clear()
        self.sel_key = 0
        self.sel_mode = False
        if self.state == S_TEST and self.test_ui == "self":
            # The on-device key test doesn't survive a config reload — and it
            # must not leave playback suppressed behind it.
            self.app.test_mode = False
            self.app.test_local = False
            self.test_ui = "wiring"
        if self.state not in (S_HOST, S_PLAYING):
            self.state = S_SELECT
            self._draw_grid()

    def on_mode(self, mode):
        if mode == "host":
            if self.state != S_HOST:
                self.prev_state = S_SELECT
                self.state = S_HOST
                self._draw_host()
        elif self.state == S_HOST:
            self.state = S_SELECT
            self._drain_inputs()
            self._draw_grid()

    def on_play_start(self, trigger, path):
        # Only a physical macro-key press changes the screen; encoder-slot
        # and host-commanded plays leave it alone (they can fire fast, and a
        # full SH1106 refresh per detent would crawl).
        if trigger is None or self.state == S_HOST:
            return
        key_no = self.app.config["key_map"][trigger]
        self.playing_cell = key_no - 1
        self.state = S_PLAYING
        self.oled.show_grid(self.labels(self.app.layer), self.playing_cell,
                            True, self._band(),
                            self._grid_icons(self.app.layer),
                            self._grid_page(), self._band_state())

    def on_play_done(self):
        self._drain_inputs()  # inputs queued during playback are stale
        if self.state == S_PLAYING:
            self.sel_key = self.playing_cell or 0
            self.playing_cell = None
            self.state = S_SELECT
            self._draw_grid()

    # --- input plumbing ---
    def _enc_delta(self):
        p = self.enc.position
        d = p - self.last_enc
        self.last_enc = p
        return d

    def _drain_inputs(self):
        self.last_enc = self.enc.position
        while self.nav.events.get():
            pass

    def _toggle_sel_mode(self):
        self.sel_mode = not self.sel_mode
        if self.state == S_SELECT:
            self._draw_grid()

    def _resolve_nav(self, key, has_double, has_hold, hold_s, double_s):
        """Blocking tap/double/hold pick for a nav button — the counterpart
        of App.resolve_variant, fed by keypad events instead of Buttons.
        Zero added latency when only a tap exists (callers skip this)."""
        t0 = time.monotonic()
        while True:
            if has_hold and time.monotonic() - t0 >= hold_s:
                return "hold"
            ev = self.nav.events.get()
            if ev and ev.key_number == key and not ev.pressed:
                break
            self.app.pump()  # serial keeps draining while the gesture holds
            self.app.led.tick()
            time.sleep(0.002)
        if not has_double:
            return "tap"
        t1 = time.monotonic()
        while time.monotonic() - t1 < double_s:
            ev = self.nav.events.get()
            if ev and ev.key_number == key and ev.pressed:
                return "double"
            self.app.pump()
            self.app.led.tick()
            time.sleep(0.002)
        return "tap"

    def _run_node(self, node, meta, choice, now, default, dflt):
        """Fire one resolved slot gesture. A "menu"-kind assignment drives
        the BUILT-IN navigation (never another custom slot — no recursion);
        its "default" action means whatever this input does out of the box,
        and "none" turns the control off — the input is swallowed."""
        if node[0] == "menu":
            act = node[1]
            if act == "left":
                default(now, -1, None)
            elif act == "right":
                default(now, 1, None)
            elif act == "confirm":
                default(now, 0, K_CONFIRM)
            elif act == "back":
                default(now, 0, K_BACK)
            elif act == "home":
                self._go_home()
            elif act == "settings":
                self._goto_settings()
            elif act == "grid":
                self._enter_grid()
            elif act == "layer_next":
                self._jump_layer(1)
            elif act == "layer_prev":
                self._jump_layer(-1)
            elif act[:6] == "layer_" and len(act) == 7:
                self._goto_layer(LAYER_NAMES.find(act[6]))
            elif act == "select":
                self._toggle_sel_mode()  # built-in PSH-hold escape, now assignable (issue #26)
            elif act == "none":
                pass  # assigned "Do nothing" in the app
            else:
                dflt()
        else:
            self.app.play_file(meta["path"], trigger=None, variant=choice)

    def _custom_input(self, now, d, press, slots, default):
        """Layer a context's custom slot assignments over its built-in
        (now, d, press) handler. Select mode bypasses every assignment;
        injected menu actions (macro keys) resolve as plain taps — there
        is no physical press whose release could be waited on."""
        if d:
            cw = ccw = None
            if not self.sel_mode:
                cw = slots.get("enc-cw")
                ccw = slots.get("enc-ccw")
            if cw or ccw:
                meta = cw if d > 0 else ccw
                if meta:  # other direction of a half-assigned wheel: no-op
                    step = 1 if d > 0 else -1
                    for _ in range(min(abs(d), 4)):  # cap a fast spin burst
                        self._run_node(meta["tap"], meta, "tap", now, default,
                                       lambda: default(now, step, None))
            else:
                default(now, d, None)
        if press is None:
            return
        meta = None if self.sel_mode else slots.get(NAV_SLOTS.get(press))
        if not meta:
            default(now, 0, press)
            return
        esc = press == K_PSH and not self._injecting  # PSH hold escape
        has_hold = bool(meta["hold"]) or esc
        choice = "tap"
        if not self._injecting and (has_hold or meta["double"]):
            choice = self._resolve_nav(press, bool(meta["double"]), has_hold,
                                       meta["hold_s"] if meta["hold"]
                                       else ESC_HOLD_S, meta["double_s"])
        if choice == "hold" and not meta["hold"]:
            self._toggle_sel_mode()  # the escape, not an assignment
            return
        node = meta.get(choice) or meta["tap"]
        self._run_node(node, meta, choice, now, default,
                       lambda: default(now, 0, press))

    # --- drawing shortcuts ---
    def _draw_home(self):
        c = self.app.config["layer_count"]
        names = self.app.config.get("layer_names")
        p = self.home_pos
        nick = names[p] if names and p < len(names) else None
        self.oled.show_home(p, c, LAYER_NAMES[:c], nick, p == self.app.layer)
        if self.home_pos < c:
            self.app.led.set(layer=self.home_pos)  # preview color
        else:
            self.app.led.set(layer=self.app.layer)

    def _band(self):
        """Status-strip text over the grid, or None. Layer part is always
        device-known; the profile part is whatever label the app last
        pushed (t:"label") and vanishes with the app. A per-layer nickname
        (config "layer_names") replaces the plain "Layer A" with "(A) NAME"."""
        cfg = self.app.config
        label = self.app.host_label if cfg["show_profile"] else None
        if cfg["show_layer"]:
            idx = self.app.layer
            letter = LAYER_NAMES[idx].upper()
            names = cfg.get("layer_names")
            nick = names[idx] if names and idx < len(names) else None
            # The app-pushed label (live OBS scene / profile name) wins over
            # the stored nickname: it's the dynamic status the user watches.
            if label:
                return "(%s) %s" % (letter, label)
            if nick:
                return "(%s) %s" % (letter, nick)
            return tr("layer_band") % letter
        return label

    def _band_state(self):
        """(recording, live, blink phase) for the band's right-hand end.

        These used to be "(R)"/"(L)" spliced into the band text, which meant
        the eye had to read a word to learn the keypad was recording. They are
        a chip and a blinking dot now, drawn by oled.py — and only the dot
        blinks, so REC stays readable through both phases."""
        return (bool(self.app.host_rec), bool(self.app.host_live),
                self._blink_on)

    def _grid_page(self):
        """(layer, layer_count) when the wheel walks layers, else None. The
        band then carries a position and a dot row appears under the tiles."""
        if not self.app.config["wheel_layers"]:
            return None
        return (self.app.layer, self.app.config["layer_count"])

    def _grid_icons(self, l):
        """The six action icons. A macro's own "icon" name wins; without one
        the action family's default is used. An unknown name also falls back —
        an icon retired from the set must never blank a tile.

        The one name that means "draw nothing" is "none": a macro with no icon
        field at all gets the family default, so without a way to say it out
        loud there was no way to ask for a bare, full-width name."""
        from mkyada import icons
        out = []
        for k in range(6):
            name = self._icons.get((l, k))
            if name == "none":
                out.append(None)
                continue
            art = icons.get(name) if name else None
            if art is None:
                kind = self._kinds.get((l, k), (None, None))[0]
                art = icons.get(KIND_ICON.get(kind)) if kind else None
            out.append(art)
        return out

    def on_sysvol(self, percent):
        """The app pushed the live system volume (the device can't read it).
        Shown on volume-kind grid cells; repaint the grid if it's up."""
        try:
            v = clamp(int(percent), 0, 100)
        except (TypeError, ValueError):
            v = None
        if v == self.sysvol:
            return
        self.sysvol = v
        if self.state == S_SELECT:
            self._draw_grid()

    def _grid_labels(self, l):
        """Base labels with the live system volume overlaid on volume-kind
        cells (their second line becomes '%NN')."""
        labels = self.labels(l)
        if self.sysvol is None:
            return labels
        out = None
        for k in range(6):
            kind, _ = self._kinds.get((l, k), (None, None))
            if kind == "volume":
                if out is None:
                    out = list(labels)
                a = labels[k][0] if k < len(labels) else "Vol"
                out[k] = (a or "Vol", "%%%d" % self.sysvol)
        return out if out is not None else labels

    def _draw_grid(self):
        # show_grid itself compacts, retries and degrades per-cell — no
        # wrapper here: the extra nested handler frames exhausted the fixed
        # pystack ("pystack exhausted" in on_layer).
        l = self.app.layer
        invert = self.sel_mode or not self._enc_custom()
        self.oled.show_grid(self._grid_labels(l), self.sel_key, invert,
                            self._band(), self._grid_icons(l),
                            self._grid_page(), self._band_state())

    def _enc_custom(self):
        """Wheel rotation is customized — the selection highlight rests."""
        s = self.slots(self.app.layer)
        return bool(s.get("enc-cw") or s.get("enc-ccw"))

    def _grid_custom(self):
        """Any grid slot assigned: PSH becomes the select-mode toggle."""
        s = self.slots(self.app.layer)
        for k in UI_SLOTS:
            if s.get(k):
                return True
        return False

    def _enter_grid(self):
        self.sel_mode = False
        self.state = S_SELECT
        self._draw_grid()

    def _enter_speed(self):
        l = self.app.layer
        self.speed_t = self.speed_tenths(l, self.sel_key)
        self.last_move = 0.0
        self.state = S_SPEED
        self.oled.show_speed(LAYER_NAMES[l], self.sel_key + 1, self.speed_t)

    def _cell_name(self, l, k0):
        """The key's display label, joined back from the two grid lines."""
        try:
            a, b = self.labels(l)[k0]
            return (a + " " + b).strip() or ("K%d" % (k0 + 1))
        except Exception:
            return "K%d" % (k0 + 1)

    # kinds whose whole point is the wheel menu (a continuous slider or the
    # OBS dashboard), so pressing the physical key should open the menu, not
    # "run" a poor default
    PRESS_MENU_KINDS = ("volume", "mic_level", "obs_center", "enc_module")

    def wants_press_menu(self, key_no, layer=None):
        """True if pressing key `key_no` should open its wheel menu (slider
        kinds) rather than play its macro. Called from App.on_edge (and a
        v17 remote press, which may name another layer)."""
        kind, _ = self.kind_sub(self.app.layer if layer is None else layer,
                                key_no - 1)
        return kind in self.PRESS_MENU_KINDS

    def open_key_menu(self, key_no):
        """Open the given key's wheel menu as if it were selected on the grid
        and CONFIRM pressed — the physical key press is the entry point."""
        if self.state in (S_HOST, S_PLAYING, S_TEST):
            return
        self.sel_key = clamp(key_no - 1, 0, 5)
        self.sel_mode = False
        self._enter_ctx()

    def _enter_ctx(self):
        """Context-aware wheel menu: CONFIRM on the selected key opens a menu
        that fits the key's action instead of always the speed editor.
        Speed-editing kinds (recorded / typed text / legacy files) keep the
        speed screen; the rest get an action card that's useful on its own."""
        l = self.app.layer
        k0 = self.sel_key
        kind, sub = self.kind_sub(l, k0)
        path = self.app.macro_path_for(k0 + 1, l)
        # Speed-editing kinds: recorded / typed text / multi-step sequences
        # (their delays scale) / legacy files. Playback obeys settings.speed
        # both here and host-side.
        if kind in (None, "recorded", "text", "sequence"):
            self._enter_speed()
            return
        name = self._cell_name(l, k0)
        if kind in ("keystroke", "combo"):
            # turn = fire the key again and again (turbo); CONFIRM = fire once
            self._card_state("key", path, tr("key_t"), name, tr("hint_repeat"))
        elif kind == "scroll":
            self._card_state("scroll", path, tr("scroll_t"), name,
                             tr("hint_scroll"))
        elif kind == "midi":
            # browse every note (or controller / program): turn to highlight,
            # tap to hear it, hold to reassign this key to it
            self._enter_midi_list(path)
        elif kind == "media":
            # browse every media key: turn to highlight, tap to fire once,
            # hold to reassign this key to the highlighted one
            self._enter_optlist("media", path, MEDIA_OPTS, sub, tr("media"))
        elif kind == "volume":
            # app running -> absolute % slider (host reads/sets system volume);
            # app closed -> a relative HID volume knob (press mutes), with a
            # line explaining why there is no percent without the app
            if self.app.proto.connected and self.app.host_menus:
                self._ctx_host(kind, sub, path, k0, l)
            else:
                self._card_state("adjust", path, tr("volume"), name,
                                 tr("hint_vol"), up="volume_up",
                                 down="volume_down", conf="mute",
                                 line=tr("vol_app_note"))
        elif kind == "menu":
            # layer / navigation keys: browse the whole family (next/prev layer,
            # jump to a specific layer, Home/Grid/Settings), tap to run it live,
            # hold to reassign — all standalone, the device rewrites the file
            self._enter_optlist("menu", path, self._menu_opts(), sub,
                                 tr("menu_t"))
        elif kind == "enc_module":
            self._enter_encmod(path, name)
        elif kind in ("launch", "command", "sound", "mic", "mic_level",
                      "webhook", "obs", "obs_center"):
            self._ctx_host(kind, sub, path, k0, l)
        else:
            self._enter_speed()

    def _card_state(self, mode, path, title, big, hint,
                    up=None, down=None, conf=None, line=None):
        self.ctx = {"mode": mode, "path": path, "up": up, "down": down,
                    "conf": conf}
        self.state = S_CTX
        self.activity_at = time.monotonic()
        self.oled.show_card(title, big[:12], line, hint)

    def _menu_opts(self):
        """The layer/nav actions the menu-kind browser offers on this device:
        step layers, jump to each existing layer, then Home/Grid/Settings."""
        n = self.app.config["layer_count"]
        opts = ["layer_next", "layer_prev"]
        opts += ["layer_" + LAYER_NAMES[i] for i in range(n)]
        opts += ["home", "grid", "settings"]
        return opts

    def _opt_label(self, kind, o):
        if kind == "midi_note":
            return note_name(o)
        if kind == "midi_cc":
            return "CC %d" % o
        if kind == "midi_pc":
            return "PC %d" % o
        if kind == "media":
            return MEDIA_LABEL.get(o, o)
        if kind == "menu":
            if len(o) == 7 and o[:6] == "layer_":
                return "Layer " + o[6].upper()
            return MENU_LABEL.get(o, o)
        return str(o)

    def _enter_optlist(self, kind, path, opts, cur, title):
        """A local option browser (media): turn highlights, a tap fires the
        highlighted option, a hold reassigns the key to it. `cur` = the option
        the key is assigned to now (shown marked, cursor starts on it)."""
        opts = list(opts)
        sel = opts.index(cur) if cur in opts else 0
        self.ctx = {"mode": "optlist", "kind": kind, "opts": opts,
                    "assigned": sel, "sel": sel, "path": path, "title": title}
        self.state = S_CTX
        self.activity_at = time.monotonic()
        self.last_move = 0.0  # so the first detent is never accelerated
        self._draw_optlist()

    def _draw_optlist(self):
        c = self.ctx
        self.oled.show_menu(c["title"], _LabelView(self, c["kind"], c["opts"]),
                            c["sel"], marked=c["assigned"], action=tr("run"),
                            hold=tr("hold_set"))

    def _resolve_hold(self, key, hold_s=MENU_HOLD_S):
        """Blocking tap-vs-hold pick for a menu press: "hold" once held past
        hold_s, else "tap" on release. Serial/LED keep pumping meanwhile."""
        t0 = time.monotonic()
        while True:
            if time.monotonic() - t0 >= hold_s:
                return "hold"
            ev = self.nav.events.get()
            if ev and ev.key_number == key and not ev.pressed:
                return "tap"
            self.app.pump()
            self.app.led.tick()
            time.sleep(0.002)

    def _write_macro(self, path, data):
        """Atomically (re)write a whole-file macro, refresh caches and tell the
        app. Returns "ok" | "readonly" | "error". Profile-aware: `path` is
        already the active target (macro_path_for)."""
        tmp = path + ".part"
        try:
            raw = json.dumps(data).encode("utf-8")
            with open(tmp, "wb") as f:
                f.write(raw)
        except (OSError, MemoryError) as e:
            try:
                os.remove(tmp)
            except OSError:
                pass
            if isinstance(e, OSError) and e.args and e.args[0] == 30:
                return "readonly"
            return "error"
        try:
            os.remove(path)
        except OSError:
            pass
        try:
            os.rename(tmp, path)
        except OSError:
            return "error"
        # manifest upkeep (proto v14): the body changed on-device, so the
        # app's cached copy must stop matching — and any stale override
        # would shadow the fresh header
        stem = meta.stem_of(path)
        if stem:
            meta.update(stem, crc=crc32(raw), size=len(raw),
                        clear_overrides=True)
            self.app.meta_ov.pop(stem, None)
        self.invalidate_labels(path)
        self.app.proto.send({"t": "macro_changed", "file": path,
                             "reason": "assign"})
        return "ok"

    def _enter_midi_list(self, path):
        """Open the MIDI browser for this key. The payload is read from the
        file rather than the label cache because the picker has to keep the
        parts it is not editing — channel, velocity and the note mode all
        survive a reassign."""
        try:
            with open(path, "rb") as f:
                data = json.load(f)
        except (OSError, ValueError, MemoryError):
            data = None
        m = (data or {}).get("midi")
        if not isinstance(m, dict):
            m = {}
        msg = m.get("msg") or "note"
        try:
            cur = clamp(int(m.get("d1") or 0), 0, 127)
            ch = clamp(int(m.get("ch") or 0), 0, 15)
            d2 = clamp(int(m.get("d2", 100)), 0, 127)
        except (TypeError, ValueError):
            cur, ch, d2 = 0, 0, 100
        mode = m.get("mode") or "momentary"
        del data, m
        gc.collect()
        if msg not in ("note", "cc", "pc"):
            msg = "note"
        self._enter_optlist("midi_" + msg, path, range(128), cur, tr("midi_t"))
        # what the picker is not editing, kept for the audition and the write
        # NOT "mode": that key is the ctx's own dispatch tag ("optlist").
        self.ctx["ch"] = ch
        self.ctx["d2"] = d2
        self.ctx["note_mode"] = mode
        self.ctx["msg"] = msg

    def _midi_audition(self, c, d1):
        """Tap in the browser: send the highlighted message so it can be heard
        before it is committed. A note is a real on/off pair, not a bare
        note-on that would hang."""
        eng = self.app.engine
        msg = c["msg"]
        if msg == "cc":
            eng.midi_send("cc", c["ch"], d1, c["d2"])
        elif msg == "pc":
            eng.midi_send("pc", c["ch"], d1)
        else:
            eng.midi_send("note_on", c["ch"], d1, c["d2"])
            time.sleep(0.12)
            eng.midi_send("note_off", c["ch"], d1)

    def _midi_macro_name(self, msg, ch, d1, d2):
        """The name the APP would compile for this message (macro-model.ts
        midiName). It has to match character for character: the app treats a
        name it did not generate as a user-typed label and freezes it, so a
        shorter device name would stick to the key forever after."""
        suffix = " (ch %d)" % (ch + 1)
        if msg == "cc":
            return "CC %d = %d%s" % (d1, d2, suffix)
        if msg == "pc":
            return "Program %d%s" % (d1, suffix)
        return "Note %s%s" % (note_name(d1), suffix)

    def _write_midi_macro(self, path, c, d1):
        msg, ch, d2 = c["msg"], c["ch"], c["d2"]
        pay = {"msg": msg, "ch": ch, "d1": d1}
        if msg != "pc":
            pay["d2"] = d2
        if msg == "note":
            pay["mode"] = c["note_mode"]
            evs = [{"delay": 0, "type": "midi", "m": "note_on",
                    "ch": ch, "d1": d1, "d2": d2},
                   {"delay": 20, "type": "midi", "m": "note_off",
                    "ch": ch, "d1": d1}]
        elif msg == "cc":
            evs = [{"delay": 0, "type": "midi", "m": "cc",
                    "ch": ch, "d1": d1, "d2": d2}]
        else:
            evs = [{"delay": 0, "type": "midi", "m": "pc", "ch": ch, "d1": d1}]
        # Merge rather than rewrite: a reassign moves the note, it does not
        # throw away the key's icon, its speed setting or its tap/hold
        # variants — and rebuilding the file from scratch would also downgrade
        # a format-v3 (variants) macro to v2.
        try:
            with open(path, "rb") as f:
                data = json.load(f)
            if not isinstance(data, dict):
                data = None
        except (OSError, ValueError, MemoryError):
            data = None
        if data is None:
            data = {"format": "mkyada-macro", "version": 2}
        data["kind"] = "midi"
        data["name"] = self._midi_macro_name(msg, ch, d1, d2)
        data["midi"] = pay
        data["events"] = evs
        return self._write_macro(path, data)

    def _write_media_macro(self, path, usage):
        return self._write_macro(path, {
            "format": "mkyada-macro", "version": 2,
            "name": MEDIA_LABEL.get(usage, usage), "kind": "media",
            "media": usage,
            "events": [{"delay": 0, "type": "consumer", "usage": usage}]})

    def _write_menu_macro(self, path, act):
        return self._write_macro(path, {
            "format": "mkyada-macro", "version": 2,
            "name": self._opt_label("menu", act), "kind": "menu",
            "menu": act, "events": []})

    def _run_menu_act(self, act):
        """Perform a layer/nav menu action live (tap in the menu browser). Each
        of these transitions the UI itself, so the wheel menu is replaced by the
        action's own screen — no redraw of the browser needed."""
        if act == "layer_next":
            self._jump_layer(1)
        elif act == "layer_prev":
            self._jump_layer(-1)
        elif len(act) == 7 and act[:6] == "layer_":
            self._goto_layer(LAYER_NAMES.find(act[6]))
        elif act == "home":
            self._go_home()
        elif act == "grid":
            self._enter_grid()
        elif act == "settings":
            self._goto_settings()

    def _ctx_host(self, kind, sub, path, k0, l):
        """A host-only action (OBS, webhook, mic, ...). The device can't perform
        it alone: ask the app for a menu (proto v9). The app answers with a
        `menu` message rendered by on_menu; if it never does (or isn't there),
        fall back to the "app required" toast."""
        if self.app.proto.connected and self.app.host_menus:
            self.app.proto.send({"t": "ctx", "key": k0 + 1,
                                 "layer": LAYER_NAMES[l], "kind": kind,
                                 "sub": sub, "file": path})
            self.ctx = {"mode": "wait", "key": k0 + 1, "layer": LAYER_NAMES[l],
                        "kind": kind,
                        "deadline": time.monotonic() + CTX_WAIT_S}
            self.state = S_CTX
            self.activity_at = time.monotonic()
            self.oled.show_card(tr("wheel"), "...", None, None)
        else:
            self._toast(tr("wheel"), tr("app_needed"), tr("open_app"))

    def _obs_val(self, f, v):
        """Coerce one mtype:"obs" field. None passes through untouched — it
        means "the app disabled this widget", and the screen skips it."""
        if v is None:
            return None
        if f in ("rec", "live", "mute"):
            return bool(v)
        if f in ("mic", "cpu", "fps", "drop"):
            return int(v)
        if f == "klabels":
            try:
                return [str(x)[:6] for x in v[:6]]
            except (TypeError, IndexError):
                return None
        return str(v)

    def obs_center_active(self):
        """True while the OBS Center dashboard owns the keypad: the six keys
        are the app's quick actions, so App.on_edge must swallow the local
        play (the btn stream already carried the edge to the app)."""
        if self.state != S_CTX or not self.ctx:
            return False
        c = self.ctx
        mode = c.get("mode")
        if mode == "wait":
            return c.get("kind") == "obs_center"
        return (mode == "host" and c.get("mtype") == "obs"
                and c.get("obsview") == "center")

    # --- Dial module (kind enc_module) ---
    # A user-defined encoder toolset: the key's file carries up to six slots
    # (enc_module.slots), each mapping a wheel turn to plain HID — a shortcut
    # pair, a scroll axis, a relative mouse drag or a consumer usage. While
    # the module owns the screen the six keys select slots (App.on_edge
    # routes edges here) and the wheel drives the selected one. Everything
    # runs on the device: no app, no host round-trip.

    def enc_module_active(self):
        """True while a Dial module owns the keypad: the six keys are slot
        selectors, so App.on_edge must route the edge to encmod_key instead
        of playing that key's macro."""
        return (self.state == S_CTX and self.ctx is not None
                and self.ctx.get("mode") == "encmod")

    def _enter_encmod(self, path, name):
        """Open the Dial module: the one kind whose payload the device needs
        beyond the header, so the file gets a full parse here (small — the
        payload is six tiny dicts) and the slots live only while the module
        is open."""
        try:
            with open(path, "rb") as f:
                data = json.load(f)
        except (OSError, ValueError, MemoryError):
            data = None
        em = (data or {}).get("enc_module")
        raw = em.get("slots") if isinstance(em, dict) else None
        slots = [None] * 6
        if isinstance(raw, list):
            for i in range(min(6, len(raw))):
                s = raw[i]
                if isinstance(s, dict) and s.get("t"):
                    s["l"] = str(s.get("l") or "")[:6]
                    slots[i] = s
        del data, em, raw
        gc.collect()
        if not any(slots):
            self._toast(upper(name or "DIAL")[:12], tr("no_slots"),
                        tr("assign_app"))
            return
        sel = 0
        while not slots[sel]:
            sel += 1
        self.ctx = {"mode": "encmod", "name": name or "Dial",
                    "slots": slots, "sel": sel, "drag_until": 0.0, "held": 0}
        self.state = S_CTX
        self.activity_at = time.monotonic()
        self.last_move = 0.0
        self._draw_encmod()
        if self.app.proto.connected:
            # Announce only (proto v15): the app must NOT answer with a menu
            # (on_menu ignores it while the module is open) — it uses this to
            # suppress its own handling of the key edges streamed while the
            # keypad belongs to the module.
            self.app.proto.send({"t": "ctx", "key": self.sel_key + 1,
                                 "layer": LAYER_NAMES[self.app.layer],
                                 "kind": "enc_module", "file": path})

    def _draw_encmod(self):
        c = self.ctx
        labels = [(s["l"] or "K%d" % (i + 1)) if s else None
                  for i, s in enumerate(c["slots"])]
        self.oled.show_encmod(c["name"], labels, c["sel"])

    def encmod_key(self, key_no):
        """A physical key pressed while the module is open: select that slot.
        Empty slots are dead keys; re-pressing the selected one is a no-op."""
        c = self.ctx
        if not self.enc_module_active():
            return
        i = clamp(key_no - 1, 0, 5)
        if i == c["sel"] or not c["slots"][i]:
            return
        self._encmod_drag_release(c)  # a held drag must not leak across slots
        c["sel"] = i
        self.activity_at = time.monotonic()
        self._draw_encmod()

    def _encmod_drag_release(self, c):
        # button up first, then the gesture modifiers — the reverse of how
        # the gesture began, so the host never sees a bare modifier-drag
        eng = self.app.engine
        if eng.rel_buttons:
            eng.rel_button("left", False)
        if c.get("held"):
            eng.drop_mods(c["held"])
            c["held"] = 0
        c["drag_until"] = 0.0

    def _encmod_turn(self, now, d, c):
        s = c["slots"][c["sel"]]
        if not s:
            return
        # velocity acceleration, same feel as the speed editor: fast detents
        # (or coalesced multi-detent ticks) count double/triple
        dt = now - self.last_move
        self.last_move = now
        ad = abs(d)
        per = 3 if (ad > 1 or dt < 0.04) else (2 if dt < 0.09 else 1)
        try:
            mult = clamp(int(s.get("m") or 1), 1, 10)
        except (TypeError, ValueError):
            mult = 1
        n = ad * per * mult
        pos = d > 0
        if s.get("inv"):
            pos = not pos
        eng = self.app.engine
        t = s.get("t")
        if t == "keys":
            node = s.get("cw") if pos else s.get("ccw")
            if isinstance(node, dict) and node.get("key"):
                # short hold: 6 taps at the default 30 ms would stall the
                # wheel for ~0.2 s — jog must feel like a jog wheel
                for _ in range(min(n, 6)):
                    eng.tap_combo(node.get("mods") or (), node["key"],
                                  hold_ms=12)
        elif t == "scroll":
            amt = n if pos else -n
            if s.get("axis") == "h":
                eng.wheel_burst(0, amt, s.get("mods"))
            else:
                eng.wheel_burst(amt, 0, s.get("mods"))
        elif t == "move":
            try:
                step = clamp(int(s.get("step") or 1), 1, 30)
            except (TypeError, ValueError):
                step = 1
            amt = n * step
            if not pos:
                amt = -amt
            mods = s.get("mods")
            if mods and not c.get("held"):
                # gesture modifiers (Ctrl+Opt+drag = Photoshop brush scrub)
                # go down once, BEFORE the button, and ride the whole turn
                # gesture — released with it below
                c["held"] = eng.hold_mods(mods)
            if s.get("drag") and not eng.rel_buttons:
                eng.rel_button("left", True)
            if mods or s.get("drag"):
                c["drag_until"] = now + (MOD_DRAG_RELEASE_S if mods
                                         else DRAG_RELEASE_S)
            if s.get("axis") == "x":
                eng.rel_move(amt, 0)
            else:
                eng.rel_move(0, amt)
        elif t == "consumer":
            usage = s.get("cw") if pos else s.get("ccw")
            if usage:
                for _ in range(min(n, 4)):
                    eng.consumer_tap(usage)
        elif t == "midi_cc":
            # No tap cap here, unlike the branches above: a CC is one 3-byte
            # message with no sleep, so a fast spin costs nothing.
            try:
                cc = clamp(int(s.get("cc") or 0), 0, 127)
                chan = clamp(int(s.get("ch") or 0), 0, 15)
            except (TypeError, ValueError):
                cc, chan = 0, 0
            mode = s.get("mode") or "rel_2c"
            if mode == "abs":
                # An absolute knob has to remember where it is. That state
                # lives in the ctx, not in s: s is the parsed macro file and
                # is dropped when the module closes.
                vals = c.get("cc")
                if vals is None:
                    vals = c["cc"] = {}
                cur = vals.get(c["sel"], 64)
                cur = clamp(cur + (n if pos else -n), 0, 127)
                vals[c["sel"]] = cur
                eng.midi_send("cc", chan, cc, cur)
            else:
                # Relative: send the DELTA, so the DAW's own value is the only
                # one that matters and the knob can never jump. 63 is the most
                # a 7-bit relative encoding can say in one message.
                step = min(n, 63)
                if mode == "rel_bin":       # binary offset: 64 = no change
                    v = 64 + step if pos else 64 - step
                elif mode in ("rel_sm", "rel_mackie"):  # sign in bit 6
                    v = step if pos else 0x40 + step
                else:                       # two's complement (the default)
                    v = step if pos else 128 - step
                eng.midi_send("cc", chan, cc, v)

    def _encmod_fire(self, s):
        """The encoder button inside the module: the slot's own press action
        (play/pause on a jog slot, a left click on a drag slot, ...)."""
        b = s.get("b") if isinstance(s, dict) else None
        if not isinstance(b, dict):
            return
        eng = self.app.engine
        t = b.get("t")
        if t == "combo":
            if b.get("key"):
                eng.tap_combo(b.get("mods") or (), b["key"])
        elif t == "click":
            eng.rel_button("left", True)
            time.sleep(0.03)
            eng.rel_button("left", False)
        elif t == "consumer":
            if b.get("u"):
                eng.consumer_tap(b["u"])

    def _st_encmod(self, now, d, press):
        c = self.ctx
        if d:
            self._encmod_turn(now, d, c)
            self.activity_at = now
        elif c["drag_until"] and now > c["drag_until"]:
            # the turn gesture ended: drop the held drag button
            self._encmod_drag_release(c)
        if press == K_BACK:
            self._encmod_drag_release(c)
            if self.app.proto.connected:
                self.app.proto.send({"t": "menu_ev", "ev": "close"})
            c["slots"] = None
            self._enter_grid()
            gc.collect()
        elif press in (K_PSH, K_CONFIRM):
            self._encmod_fire(c["slots"][c["sel"]])
            self.activity_at = now
        # no idle timeout: like the OBS Center this is a dashboard, not a
        # chooser — a color session parks on it for minutes at a time

    def on_menu(self, msg):
        """The app rendered/updated the open wheel menu (host-fed list, slider
        or status card). Ignored unless a menu is open for this key."""
        if self.state != S_CTX or not self.ctx:
            return
        if self.ctx.get("mode") == "encmod":
            # The Dial module is device-local; its ctx announce is info-only.
            # An old app answers it with a default card anyway — swallowing
            # the reply here keeps the module on screen.
            return
        key = msg.get("key")
        if key is not None and self.ctx.get("key") not in (None, key):
            return  # a menu meant for a different key
        # a live re-render of the same menu (REC timer, external volume) keeps
        # the user's cursor and doesn't reset the idle timer
        prev = self.ctx if self.ctx.get("mode") == "host" else None
        if prev is not None and prev.get("mtype") == "obs" \
                and (msg.get("mtype") or "card") == "obs":
            # Sticky re-render (proto v13): merge only the fields present in
            # the message into the open ctx — the app pushes tiny deltas
            # between 5s full re-asserts, and nothing is rebuilt per push.
            for f in OBS_FIELDS:
                if f in msg:
                    prev[f] = self._obs_val(f, msg[f])
            self._draw_host_menu()
            return
        items = msg.get("items") or []
        sel_in = msg.get("sel")
        sel = int(sel_in) if sel_in is not None else (prev["sel"] if prev else 0)
        self.ctx = {"mode": "host", "mtype": msg.get("mtype") or "card",
                    "key": self.ctx.get("key") or key,
                    "layer": self.ctx.get("layer") or msg.get("layer"),
                    "title": str(msg.get("title") or tr("wheel")),
                    "big": str(msg.get("big") or ""),
                    "l1": str(msg.get("l1") or ""),
                    "l2": str(msg.get("l2") or ""),
                    "hint": msg.get("hint"), "action": msg.get("action"),
                    "hold": msg.get("hold"), "items": items,
                    "sel": clamp(sel, 0, max(0, len(items) - 1)),
                    "value": msg.get("value"),
                    "min": int(msg.get("min") or 0),
                    "max": int(msg.get("max") or 100),
                    "step": int(msg.get("step") or 1),
                    "unit": str(msg.get("unit") or ""),
                    # mtype "obs" (proto v11): a live OBS status screen. These
                    # carry no cursor, so a re-render is pure data — which is
                    # the point, the app pushes one twice a second while the
                    # recorder runs. Since v13 an absent field stays None so
                    # the center view can hide that widget entirely.
                    "obsview": str(msg.get("obsview") or "main"),
                    "rec": self._obs_val("rec", msg.get("rec")),
                    "live": self._obs_val("live", msg.get("live")),
                    "mic": self._obs_val("mic", msg.get("mic")),
                    "time": self._obs_val("time", msg.get("time")),
                    "scene": self._obs_val("scene", msg.get("scene")),
                    "mute": self._obs_val("mute", msg.get("mute")),
                    "cpu": self._obs_val("cpu", msg.get("cpu")),
                    "fps": self._obs_val("fps", msg.get("fps")),
                    "drop": self._obs_val("drop", msg.get("drop")),
                    "klabels": self._obs_val("klabels", msg.get("klabels")),
                    "focus": self._obs_val("focus", msg.get("focus"))}
        if prev is None:
            self.activity_at = time.monotonic()
            # Start the record dot lit: leaving _blink_at at zero makes the
            # first tick extinguish it immediately.
            self._blink_at = self.activity_at
            self._blink_on = True
        self._draw_host_menu()

    def on_menu_result(self, msg):
        """The app finished a picked/fired action: optionally refresh a
        rewritten macro's label, show a brief toast, and close the menu."""
        if self.state != S_CTX:
            return
        changed = msg.get("changed")
        if changed:
            self.invalidate_labels(changed)
        toast = msg.get("toast")
        if isinstance(toast, list) and toast:
            title = str(toast[0])
            line1 = str(toast[1]) if len(toast) > 1 else ""
            self._toast(title, line1, "")
        else:
            self._enter_grid()

    def on_host_gone(self):
        """The app disconnected: abandon any open host menu and drop the live
        system-volume readout (it would otherwise freeze on a stale value)."""
        had_vol = self.sysvol is not None
        self.sysvol = None
        if self.state == S_CTX and self.ctx and \
                self.ctx.get("mode") in ("host", "wait"):
            self._enter_grid()
        elif had_vol and self.state == S_SELECT:
            self._draw_grid()

    def _item_label(self, it):
        try:
            return str(it[1])[:21]
        except (IndexError, TypeError):
            return ""

    def _draw_host_menu(self):
        c = self.ctx
        mt = c["mtype"]
        if mt == "list":
            items = [self._item_label(it) for it in c["items"]] or [""]
            marked = None
            for i, it in enumerate(c["items"]):
                if len(it) > 2 and it[2]:
                    marked = i
                    break
            self.oled.show_menu(c["title"], items, c["sel"], marked=marked,
                                action=c.get("action") or tr("select"),
                                hold=tr("hold_set") if c.get("hold") else None)
        elif mt == "slider":
            v = c["value"] or 0
            span = c["max"] - c["min"]
            frac = (v - c["min"]) / float(span) if span else 0.0
            self.oled.show_adjust(c["title"], "%d%s" % (v, c["unit"]), frac,
                                  c.get("action") or tr("save"))
        elif mt == "obs":
            if c["obsview"] == "center":
                # The dashboard: None fields are widgets the app turned off,
                # show_obscenter reflows around them.
                o = {"rec": c["rec"], "live": c["live"], "mic": c["mic"],
                     "time": c["time"], "scene": c["scene"],
                     "mute": c.get("mute"), "cpu": c.get("cpu"),
                     "fps": c.get("fps"), "drop": c.get("drop"),
                     "klabels": c.get("klabels"),
                     "focus": c.get("focus"), "blink": self._blink_on}
                self.oled.show_obscenter(o)
                return
            o = {"rec": bool(c["rec"]), "live": bool(c["live"]),
                 "mic": c["mic"] or 0,
                 "time": c["time"] or "00:00", "scene": c["scene"] or "",
                 "blink": self._blink_on, "key": c.get("key"),
                 "hint": c.get("hint")}
            # "rec" is the recorder card (one big timer); "main" is the full
            # status screen. The app picks per action, so a Record key gets the
            # timer and a scene key gets the overview.
            if c["obsview"] == "rec":
                self.oled.show_obsrec(o)
            else:
                self.oled.show_obs(o)
        else:  # card
            self.oled.show_card(c["title"], (c["big"] or "")[:12],
                                c["l1"] or None, c.get("hint"))

    def _close_host_menu(self):
        if self.app.proto.connected:
            self.app.proto.send({"t": "menu_ev", "ev": "close"})
        self._enter_grid()

    def _st_ctx(self, now, d, press):
        """Wheel-menu handler. Local action cards run entirely on the device;
        host menus (mode "host") relay turn/press as menu_ev and re-render from
        the app's menu messages. BACK / idle close and notify the app."""
        c = self.ctx or {}
        mode = c.get("mode")
        if mode == "wait":
            if press == K_BACK:
                self._close_host_menu()
            elif now >= c.get("deadline", now):
                self._toast(tr("wheel"), tr("app_needed"), tr("open_app"))
            return
        if mode == "host":
            self._st_ctx_host(now, d, press)
            return
        if mode == "encmod":
            self._st_encmod(now, d, press)
            return
        # --- local menus (keystroke / scroll knob / media browser / volume) ---
        if press == K_BACK:
            self._enter_grid()
            return
        eng = self.app.engine
        if mode == "optlist":
            if d:
                # Nine media keys are fine one-per-detent, 128 notes are not:
                # a tick can carry several detents and dropping the surplus
                # put the far end of the list out of reach at speed. Long
                # lists get the speed editor's velocity curve; short ones stay
                # one-per-detent so they cannot overshoot.
                n = abs(d)
                if len(c["opts"]) > 32:
                    dt = now - self.last_move
                    n *= 3 if (n > 1 or dt < 0.04) else (2 if dt < 0.09 else 1)
                self.last_move = now
                c["sel"] = clamp(c["sel"] + (n if d > 0 else -n), 0,
                                 len(c["opts"]) - 1)
                self._draw_optlist()
            if press in (K_PSH, K_CONFIRM):
                self._optlist_press(press)
                return
        elif mode in ("key", "scroll"):
            if d:
                for _ in range(min(abs(d), 4)):
                    self.app.play_file(path=c["path"], trigger=None)
            if press in (K_PSH, K_CONFIRM):
                self.app.play_file(path=c["path"], trigger=None)
        elif mode == "fire":  # sequence: CONFIRM runs the whole macro once
            if press in (K_PSH, K_CONFIRM):
                self.app.play_file(path=c["path"], trigger=None)
        elif mode == "adjust":  # volume/brightness knob (standalone fallback)
            if d:
                usage = c["up"] if d > 0 else c["down"]
                if usage:
                    for _ in range(min(abs(d), 4)):
                        eng.consumer_tap(usage)
            if press in (K_PSH, K_CONFIRM) and c.get("conf"):
                eng.consumer_tap(c["conf"])
        if press is None and not d and now - self.activity_at > self.idle_secs:
            self._enter_grid()

    def _optlist_press(self, press):
        """A tap fires the highlighted option once; a hold reassigns the key to
        it (device-written macro, so it works standalone)."""
        c = self.ctx
        opt = c["opts"][c["sel"]]
        if self._resolve_hold(press) == "hold":
            if c["kind"] == "media":
                res = self._write_media_macro(c["path"], opt)
            elif c["kind"] == "menu":
                res = self._write_menu_macro(c["path"], opt)
            elif c["kind"][:5] == "midi_":
                res = self._write_midi_macro(c["path"], c, opt)
            else:
                res = "error"
            if res == "ok":
                c["assigned"] = c["sel"]
                self._toast(c["title"], tr("assigned"),
                            self._opt_label(c["kind"], opt))
            elif res == "readonly":
                self._toast(c["title"], tr("usb_on"), tr("read_only"))
            else:
                self._toast(c["title"], tr("save_fail"), "")
        elif c["kind"] == "media":
            self.app.engine.consumer_tap(opt)
        elif c["kind"][:5] == "midi_":
            self._midi_audition(c, opt)
        elif c["kind"] == "menu":
            self._run_menu_act(opt)  # transitions the UI itself

    def _st_ctx_host(self, now, d, press):
        c = self.ctx
        mt = c["mtype"]
        send = self.app.proto.send
        if mt == "list":
            if d and c["items"]:
                c["sel"] = clamp(c["sel"] + (1 if d > 0 else -1), 0,
                                 len(c["items"]) - 1)
                self._draw_host_menu()
            if press in (K_PSH, K_CONFIRM):
                it = c["items"][c["sel"]] if c["items"] else None
                # tap = use it now (switch scene / do the mode); hold = reassign
                ev = "assign" if self._resolve_hold(press) == "hold" else "pick"
                send({"t": "menu_ev", "ev": ev,
                      "id": (it[0] if it else None)})
            elif press == K_BACK:
                self._close_host_menu()
        elif mt == "slider":
            if d:
                step = c["step"] or 1
                c["value"] = clamp((c["value"] or 0) + d * step,
                                   c["min"], c["max"])
                self._draw_host_menu()
                send({"t": "menu_ev", "ev": "value", "v": c["value"]})
            if press in (K_PSH, K_CONFIRM):
                send({"t": "menu_ev", "ev": "close"})
                self._enter_grid()
            elif press == K_BACK:
                self._close_host_menu()
        elif mt == "obs":
            # A status screen, not a chooser: CONFIRM fires the key's action
            # (start/stop the recorder), the wheel reports a step so the app can
            # ride the mic level with it. On the center view a HOLD instead
            # moves the wheel's focus to the next control row (mic <-> scene) —
            # the app owns the cycle and answers with a new "focus" push.
            if press in (K_PSH, K_CONFIRM):
                if c.get("obsview") == "center" and \
                        self._resolve_hold(press) == "hold":
                    send({"t": "menu_ev", "ev": "mode"})
                else:
                    send({"t": "menu_ev", "ev": "fire"})
            elif d:
                send({"t": "menu_ev", "ev": "value", "v": 1 if d > 0 else -1})
            elif press == K_BACK:
                self._close_host_menu()
            elif c["rec"] and now - self._blink_at > 0.6:
                # The record dot blinks on the device's own clock: the app
                # pushes a fresh time twice a second, but the dot must keep
                # its rhythm even if a push is late.
                self._blink_at = now
                self._blink_on = not self._blink_on
                self._draw_host_menu()
        else:  # card
            if press in (K_PSH, K_CONFIRM):
                send({"t": "menu_ev", "ev": "fire"})
            elif d:
                send({"t": "menu_ev", "ev": "value", "v": 1 if d > 0 else -1})
            elif press == K_BACK:
                self._close_host_menu()
        if (press is None and not d
                and now - self.activity_at > self.idle_secs
                and not (mt == "obs" and c.get("obsview") == "center")):
            # the center view is a dashboard, not a chooser: it stays up
            # until BACK (or a transfer / the app leaving) closes it
            self._close_host_menu()

    def _toast(self, title, line1, line2=""):
        self.state = S_TOAST
        self.toast_at = time.monotonic()
        self.oled.show_toast(title, line1, line2)

    # --- per-state handlers ---
    def tick(self, now):
        if self.state == S_XFER:
            # The app owns the filesystem: the wheel and the nav buttons are
            # dropped on the floor rather than queued, so a save is not
            # followed by a burst of menus the user pressed at a dead screen.
            self._drain_inputs()
            return
        if self.state == S_HOST:
            self._tick_host()
            return
        if self.state == S_TEST:
            self._tick_test(now)
            return
        if self.state == S_PLAYING:
            return  # playback owns the loop; on_play_done() restores us
        d = self._enc_delta()
        ev = self.nav.events.get()
        # Mirror the wheel/nav to a connected app even in standalone mode, the
        # same way macro keys stream their btn events on every screen — so the
        # Setup test panel lights up live with no "host mode" round-trip. The
        # inputs still drive the menu below; the app just gets to watch.
        if self.app.proto.connected:
            if d:
                self.app.proto.send({"t": "enc", "d": 1 if d > 0 else -1,
                                     "n": abs(d)})
            if ev:
                self.app.proto.send({"t": "btn",
                                     "slot": NAV_SLOT[ev.key_number],
                                     "down": bool(ev.pressed)})
        press = ev.key_number if (ev and ev.pressed) else None
        self._dispatch(now, d, press)

    def inject(self, action):
        """A macro key mapped to a device-menu action drives the UI as if the
        encoder or CONFIRM/BACK were used (menu left/right/confirm/back).
        "home" / "settings" jump straight to that screen."""
        if self.state in (S_HOST, S_PLAYING):
            return  # menu nav is meaningless while playing / app-owned
        now = time.monotonic()
        self._injecting += 1
        try:
            if action == "left":
                self._dispatch(now, -1, None)
            elif action == "right":
                self._dispatch(now, 1, None)
            elif action == "confirm":
                self._dispatch(now, 0, K_CONFIRM)
            elif action == "back":
                self._dispatch(now, 0, K_BACK)
            elif action == "home":
                self._go_home()
            elif action == "settings":
                self._goto_settings()
            elif action == "grid":
                self._enter_grid()
            elif action == "layer_next":
                self._jump_layer(1)
            elif action == "layer_prev":
                self._jump_layer(-1)
            elif action[:6] == "layer_" and len(action) == 7:
                self._goto_layer(LAYER_NAMES.find(action[6]))
        finally:
            self._injecting -= 1

    def _dispatch(self, now, d, press):
        if d or press is not None:
            self.activity_at = now
        if self.state == S_HOME:
            self._st_home(now, d, press)
        elif self.state == S_SELECT:
            self._st_select(now, d, press)
        elif self.state == S_SPEED:
            self._st_speed(now, d, press)
        elif self.state == S_CTX:
            self._st_ctx(now, d, press)
        elif self.state == S_SAVED:
            if now - self.saved_at > SAVED_DWELL_S:
                self._enter_grid()
        elif self.state == S_TOAST:
            if press is not None or now - self.toast_at > TOAST_DWELL_S:
                self._enter_grid()
        elif self.state == S_SET_MENU:
            self._st_set_menu(now, d, press)
        elif self.state == S_TIMEOUT:
            self._st_timeout(now, d, press)
        elif self.state == S_LANG:
            self._st_lang(now, d, press)
        elif self.state == S_ABOUT:
            self._st_about(now, d, press)
        elif self.state == S_PIXELS:
            self._st_pixels(now, d, press)

    def _tick_host(self):
        """Forward encoder/nav to the app; it performs the assigned actions
        (soundboard, OBS, ...) computer-side."""
        d = self._enc_delta()
        if d:
            self.app.proto.send({"t": "enc", "d": 1 if d > 0 else -1,
                                 "n": abs(d)})
        while True:
            ev = self.nav.events.get()
            if not ev:
                break
            self.app.proto.send({"t": "btn", "slot": NAV_SLOT[ev.key_number],
                                 "down": bool(ev.pressed)})

    def _tick_test(self, now):
        """Test mode: the wheel/nav stream to the app's tester like host mode
        AND show on the screen (wheel direction / pressed nav button + its
        pin), so every control is verifiable on the device. Key presses come
        via App.on_edge (on_test_key).

        Settings > Key test (test_ui "self") runs the same check with no app in
        the loop, so it also owns its own way out: PSH held TEST_EXIT_HOLD_S,
        or the Auto-return idle timeout."""
        local = self.test_ui == "self"
        # Only the Setup tab's wiring test names the control on the glass. The
        # Keys tab (test_ui "keys") has its own static "macros are paused"
        # warning up, and repainting over it for a wheel detent or a BACK press
        # replaced that warning with a SETUP TEST card — from the user's side
        # the Keys test simply became a different test. Same rule already
        # applies to key presses in on_test_key; the wheel and nav buttons were
        # the two paths that missed it.
        wiring = self.test_ui == "wiring"
        d = self._enc_delta()
        if d:
            # Settings > Key test is device-owned: the wheel and the nav buttons
            # below must NOT be mirrored to the app. A connected app watching
            # those events answers with test_enter, which overwrites test_ui
            # with "wiring" — so one detent turned the user's own key test into
            # the app's setup test under them.
            if self.app.proto.connected and not local:
                self.app.proto.send({"t": "enc", "d": 1 if d > 0 else -1,
                                     "n": abs(d)})
            if local:
                self.activity_at = now
                self._kt_enc(1 if d > 0 else -1)
            elif wiring:
                ea, eb = MODELS[self.app.model]["encoder"]
                self.oled.show_toast(tr("setup_test"),
                                     "Wheel " + ("CW" if d > 0 else "CCW"),
                                     "%s/%s" % (ea, eb))
        while True:
            ev = self.nav.events.get()
            if not ev:
                break
            if self.app.proto.connected and not local:
                self.app.proto.send({"t": "btn",
                                     "slot": NAV_SLOT[ev.key_number],
                                     "down": bool(ev.pressed)})
            if not local:
                if wiring and ev.pressed:
                    names = self.app.nav_pin_names() or ()
                    pin = (names[ev.key_number]
                           if ev.key_number < len(names) else "?")
                    self.oled.show_toast(tr("setup_test"),
                                         NAV_SLOT[ev.key_number].upper(), pin)
                continue
            self.activity_at = now
            # PSH is both a button under test and the way out: it reports
            # itself on press like the others, and leaves once it has been
            # held past TEST_EXIT_HOLD_S (checked below, so the hold never
            # blocks the other controls from reporting).
            if ev.key_number == K_PSH:
                self._psh_down_at = now if ev.pressed else None
            if ev.pressed:
                self._kt_nav(ev.key_number)
        if not local:
            return
        if (self._psh_down_at is not None
                and now - self._psh_down_at >= TEST_EXIT_HOLD_S):
            self._leave_keytest(now, True)
        elif now - self.activity_at > max(self.idle_secs, TEST_IDLE_MIN_S):
            self._leave_keytest(now, False)

    def _kt_reset(self):
        self._kt = {"cnt": [0, 0, 0, 0, 0, 0], "nav": [0, 0, 0],
                    "enc": 0, "last": -1}

    def _kt_paint(self):
        if self._kt is None:
            self._kt_reset()
        self.oled.show_keytest(self._kt)

    def _kt_key(self, key0):
        if self._kt is None:
            self._kt_reset()
        if 0 <= key0 < 6:
            self._kt["cnt"][key0] += 1
            self._kt["last"] = key0
        self._kt_paint()

    def _kt_nav(self, slot0):
        if self._kt is None:
            self._kt_reset()
        if 0 <= slot0 < 3:
            self._kt["nav"][slot0] += 1
        self._kt_paint()

    def _kt_enc(self, d):
        if self._kt is None:
            self._kt_reset()
        self._kt["enc"] += d
        self._kt_paint()

    def _show_test_hit(self, label, pin):
        """The app-driven Setup wiring check still names one control at a
        time — it is showing which GPIO answered, which is per-press by
        definition."""
        self.oled.show_card(tr("keys_test"), label, pin, tr("hold_exit"))

    def _enter_keytest(self, now):
        """Settings > Key test: the Setup tab's wiring check, on the device
        itself. Every control names itself over the GPIO it actually came in
        on — the six macro keys, the three module buttons and the wheel — so a
        cold joint shows up as the one control that stays silent, with no
        computer attached. Macro playback is suppressed while it runs, which
        is also what stops a mapped key from firing as it's poked at."""
        self.state = S_TEST
        self.test_ui = "self"
        # Not the app's test mode: no app is holding this one open, so the
        # disconnect cleanup in App must leave it alone (test_local).
        self.app.test_mode = True
        self.app.test_local = True
        self._drain_inputs()
        self._psh_down_at = None
        self.activity_at = now
        self._kt_reset()
        self._kt_paint()

    def _leave_keytest(self, now, to_menu):
        """End the on-device key test: back to Settings when the user held PSH
        to get out, back to the grid when Auto-return did it for them."""
        self.app.test_mode = False
        self.app.test_local = False
        self.test_ui = "wiring"
        self._psh_down_at = None
        self._drain_inputs()
        if to_menu:
            self.state = S_SET_MENU
            self.activity_at = now
            self.oled.show_settings(tr("settings"), self._set_items(),
                                self.set_menu_sel)
        else:
            self._enter_grid()

    # --- Test mode: Setup wiring test (issue #24) / Keys tab (issue #33) ---
    def on_test_enter(self, ui="wiring"):
        self.state = S_TEST
        self.test_ui = ui
        self.app.test_local = False  # app-owned from here on
        self._psh_down_at = None
        self._drain_inputs()
        if ui == "keys":
            # Keys tab is open on the app: warn that macros are paused here.
            self.oled.show_toast(tr("keys_test"), tr("keys_test_paused"),
                                 tr("keys_test_switch"))
        else:
            self.oled.show_toast(tr("setup_test"), tr("press_key"), "")

    def on_test_key(self, key_no, pin):
        if self.state != S_TEST:
            return
        if self.test_ui == "self":
            # Settings > Key test: the key's logical number over the GPIO it
            # came in on. What's being checked here is the wiring, not which
            # macro sits on the key.
            self.activity_at = time.monotonic()
            self._kt_key(key_no - 1)
            return
        if self.test_ui == "keys":
            # Keys tab: the static "macros paused" warning is already up, so
            # don't repaint per press. Building the label (which reads the
            # macro file for its name and lazily loads BDF glyphs) plus the
            # blocking OLED refresh would stall the button scan long enough
            # that the release edge is reported late — the app's live key
            # highlight then lingers, looking like the key "kept running its
            # macro" even though playback is suppressed. Nothing to show here.
            return
        # Setup wiring test: showing the pressed key + pin IS the point.
        try:
            a, b = self.labels(self.app.layer)[key_no - 1]
            name = (a + " " + b).strip()
        except Exception:
            name = ""
        self.oled.show_toast(tr("setup_test"), name or ("K%d" % key_no),
                             "K%d  %s" % (key_no, pin))

    def on_test_leave(self):
        if self.state == S_TEST:
            self.app.test_local = False
            self.test_ui = "wiring"
            self._psh_down_at = None
            self._drain_inputs()
            self.state = S_SELECT
            self._draw_grid()

    def on_xfer(self, active):
        """The app started or finished moving files (App.begin_xfer).

        Two repaints for a whole save, no matter how many files it touches:
        one to put the screen up and one to give the keypad back. The grid is
        what we come back to rather than wherever the user was, because the
        files that screen was reading — macro names, icons, speeds — are the
        ones that just changed underneath it.

        A firmware update is not routed here: it has its own locked screen
        with a real progress bar, and the two must not fight over the glass."""
        if active:
            if self.state in (S_XFER, S_PLAYING):
                return
            if self.state == S_CTX and self.ctx \
                    and self.ctx.get("mode") in ("host", "wait"):
                # the app owns a live menu session (OBS Center keeps a poll
                # running behind it): tell it the menu is gone so the session
                # tears down instead of leaking behind the transfer screen
                self.app.proto.send({"t": "menu_ev", "ev": "close"})
            elif self.state == S_CTX and self.ctx \
                    and self.ctx.get("mode") == "encmod":
                # the Dial module dies under a transfer too: drop a held
                # drag (the host must not keep dragging a color wheel while
                # files move) and tell the app its edge suppression is over
                self._encmod_drag_release(self.ctx)
                self.app.proto.send({"t": "menu_ev", "ev": "close"})
                self.ctx = None
            self._drain_inputs()
            self.state = S_XFER
            self.oled.show_transfer()
        elif self.state == S_XFER:
            self._drain_inputs()
            self._drop_macro_cache()
            self._enter_grid()

    def _st_home(self, now, d, press):
        self._custom_input(now, d, press, self.ctx_slots("home"),
                           self._home_default)
        if not d and press is None and now - self.activity_at > self.idle_secs:
            self._enter_grid()  # idle returns to the confirmed layer's grid

    def _home_default(self, now, d, press):
        c = self.app.config["layer_count"]
        if d:
            self.home_pos = clamp(self.home_pos + (1 if d > 0 else -1), 0, c)
            self._draw_home()
        if press in (K_PSH, K_CONFIRM):
            if self.home_pos == c:  # SETTINGS
                self._goto_settings()
            else:
                self.app.set_layer_idx(self.home_pos)
                self._nvm_save()
                self._enter_grid()
        elif press == K_BACK:
            self._enter_grid()

    def _go_home(self):
        # sel_mode survives into home/menus: entered as the escape from a
        # customized grid, it must keep navigation default until the user
        # lands back on the grid (issue #19)
        self.home_pos = self.app.layer
        self.state = S_HOME
        self.activity_at = time.monotonic()  # injected jumps carry no press
        self._draw_home()

    def _goto_settings(self):
        """Open the settings menu — from the home SETTINGS entry, or as a
        direct-jump "settings" menu action assigned to a key/control."""
        self.set_menu_sel = 0
        self.state = S_SET_MENU
        self.activity_at = time.monotonic()
        self.oled.show_settings(tr("settings"), self._set_items(), 0)

    def _jump_layer(self, step):
        """Switch the active layer by a relative step (menu action "layer_next"
        / "layer_prev")."""
        c = self.app.config["layer_count"]
        self._goto_layer((self.app.layer + step) % c)

    def _goto_layer(self, idx):
        """Jump straight to an absolute layer index (menu action "layer_a"..)
        — same flow as confirming a layer on the home screen. Ignores an index
        past this device's layer_count."""
        if 0 <= idx < self.app.config["layer_count"]:
            self.app.set_layer_idx(idx)
            self._nvm_save()
            # no retry wrapper: show_grid is self-healing, and nested
            # except-handler retries exhausted the pystack
            self._enter_grid()

    def _st_select(self, now, d, press):
        self._custom_input(now, d, press, self.slots(self.app.layer),
                           self._select_default)
        if (not d and press is None and self.sel_mode
                and now - self.activity_at > self.idle_secs):
            self.sel_mode = False  # back to the customized resting grid
            self._draw_grid()
        # Blink the (R)/(L) OBS markers in the band. Cheap since the grid
        # group is persistent: this repaint only swaps the band label text.
        if (self.app.host_rec and not d and press is None
                and now - self._blink_at > 0.6):
            self._blink_at = now
            self._blink_on = not self._blink_on
            self._band_repaint()

    def _select_default(self, now, d, press):
        if d:
            cfg = self.app.config
            n = cfg["layer_count"]
            if cfg["wheel_layers"] and n > 1:
                # Wrap past the sixth tile into the next layer's first, the
                # way the design source pages its menu. Here a page IS a
                # layer, so the wheel also switches which macros are live —
                # app.set_layer does the LED and the label cache.
                total = n * 6
                idx = (self.app.layer * 6 + self.sel_key
                       + (1 if d > 0 else -1)) % total
                self.sel_key = idx % 6
                target = idx // 6
                if target != self.app.layer:
                    # Only when the detent actually crosses a boundary.
                    # set_layer_idx drives the LED and announces the layer over
                    # serial, and five detents in six stay inside the layer they
                    # started in — calling it every time was both a wasted
                    # announce and a second full grid paint.
                    self._wheel_move = True
                    try:
                        self.app.set_layer_idx(target)
                    finally:
                        self._wheel_move = False
            else:
                self.sel_key = clamp(self.sel_key + (1 if d > 0 else -1), 0, 5)
            self._draw_grid()
        if press == K_PSH:
            if self._grid_custom():
                # PSH is the guaranteed menu key on a customized grid:
                # toggles the temporary default-navigation "select mode"
                self._toggle_sel_mode()
            else:
                self._enter_ctx()
        elif press == K_CONFIRM:
            self._enter_ctx()
        elif press == K_BACK:
            self._go_home()

    def _st_speed(self, now, d, press):
        if d:
            dt = now - self.last_move
            self.last_move = now
            ad = abs(d)
            per = 3 if (ad > 1 or dt < 0.04) else (2 if dt < 0.09 else 1)
            self.speed_t = clamp(self.speed_t + d * per, SPEED_MIN_T, SPEED_MAX_T)
            self.oled.show_speed(LAYER_NAMES[self.app.layer], self.sel_key + 1,
                                 self.speed_t)
        if press in (K_PSH, K_CONFIRM):
            res = self.persist_speed(self.app.layer, self.sel_key, self.speed_t)
            if res == "ok":
                self.state = S_SAVED
                self.saved_at = now
                self.oled.show_saved(LAYER_NAMES[self.app.layer],
                                     self.sel_key + 1, self.speed_t)
            elif res == "missing":
                self._toast(upper(tr("speed")), tr("no_macro"), tr("assign_app"))
            elif res == "readonly":
                self._toast(upper(tr("speed")), tr("usb_on"), tr("read_only"))
            else:
                self._toast(upper(tr("speed")), tr("save_fail"), "")
        elif press == K_BACK:
            self._enter_grid()
        elif now - self.activity_at > self.idle_secs:
            self._enter_grid()

    def _st_set_menu(self, now, d, press):
        self._custom_input(now, d, press, self.ctx_slots("menu"),
                           self._set_menu_default)
        if not d and press is None and now - self.activity_at > self.idle_secs:
            self._enter_grid()

    def _set_menu_default(self, now, d, press):
        if d:
            self.set_menu_sel = clamp(self.set_menu_sel + (1 if d > 0 else -1),
                                      0, len(self._set_items()) - 1)
            self.oled.show_settings(tr("settings"), self._set_items(), self.set_menu_sel)
        if press in (K_PSH, K_CONFIRM):
            if self.set_menu_sel == SET_TMO:
                self.tmo_val = self.idle_secs
                self.last_move = 0.0
                self.state = S_TIMEOUT
                self.oled.show_timeout(self.tmo_val, TMO_MIN, TMO_MAX)
            elif self.set_menu_sel == SET_LANG:
                self.lang_sel = i18n.LANGS.index(i18n.get_lang())
                self.state = S_LANG
                self.oled.show_menu(tr("lang_title"), i18n.LANG_DESC,
                                    self.lang_sel, marked=self.lang_sel)
            elif self.set_menu_sel in (SET_BAND_LAYER, SET_BAND_PROFILE,
                                       SET_WHEEL_LAYERS):
                key = ("show_layer" if self.set_menu_sel == SET_BAND_LAYER
                       else "show_profile"
                       if self.set_menu_sel == SET_BAND_PROFILE
                       else "wheel_layers")
                title = upper(tr(key))
                res = self.persist_cfg({key: not self.app.config[key]})
                if res == "ok":
                    self.oled.show_settings(tr("settings"), self._set_items(),
                                        self.set_menu_sel)
                elif res == "readonly":
                    self._toast(title, tr("usb_on"), tr("read_only"))
                else:
                    self._toast(title, tr("save_fail"), "")
            elif self.set_menu_sel == SET_KEYTEST:
                self._enter_keytest(now)
            elif self.set_menu_sel == SET_PIXTEST:
                self.state = S_PIXELS
                self.activity_at = now
                self._drain_inputs()   # the press that opened it must not close it
                self.oled.show_pixels()
            elif self.set_menu_sel == SET_ABOUT:
                self.state = S_ABOUT
                self.oled.show_about(self._about_lines())
            elif microcontroller:
                microcontroller.reset()
        elif press == K_BACK:
            self.home_pos = self.app.config["layer_count"]
            self.state = S_HOME
            self._draw_home()

    def _about_lines(self):
        """(label, value) pairs for the About screen: model, firmware, UID."""
        app = self.app
        uid = getattr(app, "uid", None) or ""
        return ((tr("model"), app.model),
                (tr("firmware"), app.fw_version),
                (tr("device_id"), uid[:12]))

    def _st_about(self, now, d, press):
        # read-only info screen; any nav (or BACK) returns to the menu
        if press is not None or now - self.activity_at > self.idle_secs:
            self._back_to_settings()

    def _st_pixels(self, now, d, press):
        """All-white panel check. PSH / BACK / CONFIRM all return — the point of
        the screen is that nothing is readable on it, so the way out must not
        depend on reading anything. Auto-return still applies as a backstop."""
        if press is not None or now - self.activity_at > self.idle_secs:
            self._back_to_settings()

    def _back_to_settings(self):
        self.state = S_SET_MENU
        self.oled.show_settings(tr("settings"), self._set_items(),
                                self.set_menu_sel)

    def persist_cfg(self, updates):
        """Merge updates into config.json (and the live config) so the app
        always sees the same values. Returns "ok" | "readonly" | "error".
        The file work lives on App now (serial set_cfg shares it)."""
        return self.app.persist_cfg(updates)

    def on_cfg_patch(self, upd):
        """The app patched config live over serial (set_cfg, proto v14) —
        apply what has device-side state and repaint the resting screens so
        the band shows the new name/toggles without a reload."""
        if "timeout" in upd and isinstance(upd["timeout"], int):
            self.idle_secs = clamp(upd["timeout"], TMO_MIN, TMO_MAX)
            self.tmo_val = self.idle_secs
            self._nvm_save()
        # lang is applied app-side (i18n.set_lang) before this hook; the
        # repaint below redraws whatever static text is on the glass
        if self.state == S_SELECT:
            self._draw_grid()
        elif self.state == S_HOME:
            self._draw_home()

    def persist_lang(self, lang):
        """Rewrite config.json "lang" so the app sees the same choice.
        Returns "ok" | "readonly" | "error"."""
        res = self.persist_cfg({"lang": lang})
        if res == "ok":
            i18n.set_lang(lang)
        return res

    def _st_lang(self, now, d, press):
        self._custom_input(now, d, press, self.ctx_slots("menu"),
                           self._lang_default)
        if not d and press is None and now - self.activity_at > self.idle_secs:
            self._enter_grid()

    def _lang_default(self, now, d, press):
        if d:
            self.lang_sel = clamp(self.lang_sel + (1 if d > 0 else -1),
                                  0, len(i18n.LANGS) - 1)
            self.oled.show_menu(tr("lang_title"), i18n.LANG_DESC, self.lang_sel,
                                marked=i18n.LANGS.index(i18n.get_lang()))
        if press in (K_PSH, K_CONFIRM):
            res = self.persist_lang(i18n.LANGS[self.lang_sel])
            if res == "ok":
                self.state = S_SET_MENU
                self.oled.show_settings(tr("settings"), self._set_items(), self.set_menu_sel)
            elif res == "readonly":
                self._toast(upper(tr("language")), tr("usb_on"), tr("read_only"))
            else:
                self._toast(upper(tr("language")), tr("save_fail"), "")
        elif press == K_BACK:
            self.state = S_SET_MENU
            self.oled.show_settings(tr("settings"), self._set_items(), self.set_menu_sel)

    def _st_timeout(self, now, d, press):
        self._custom_input(now, d, press, self.ctx_slots("menu"),
                           self._timeout_default)
        if not d and press is None and now - self.activity_at > self.idle_secs:
            self._enter_grid()

    def _timeout_default(self, now, d, press):
        if d:
            dt = now - self.last_move
            self.last_move = now
            per = 3 if (abs(d) > 1 or dt < 0.05) else 1
            self.tmo_val = clamp(self.tmo_val + d * per, TMO_MIN, TMO_MAX)
            self.oled.show_timeout(self.tmo_val, TMO_MIN, TMO_MAX)
        if press in (K_PSH, K_CONFIRM):
            self.idle_secs = self.tmo_val
            self._nvm_save()
            self.persist_cfg({"timeout": self.idle_secs})  # app-facing mirror
            self.state = S_SET_MENU
            self.oled.show_settings(tr("settings"), self._set_items(), self.set_menu_sel)
        elif press == K_BACK:
            self.state = S_SET_MENU
            self.oled.show_settings(tr("settings"), self._set_items(), self.set_menu_sel)
